mirdej/vmix/images/IMG_1347.jpg

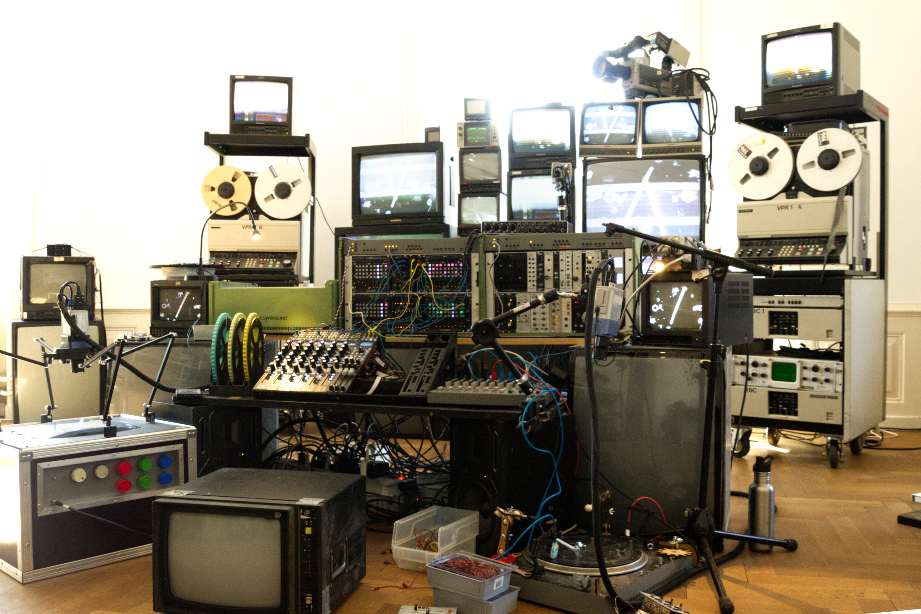
images/IMG_1347.jpg
