mirdej/vmix/electronics/vm106-mixbus/vm106-mixbus.kicad_pcb

## KiCad design electronics/vm106-mixbus/vm106-mixbus.kicad_pcb (2021-04-03)

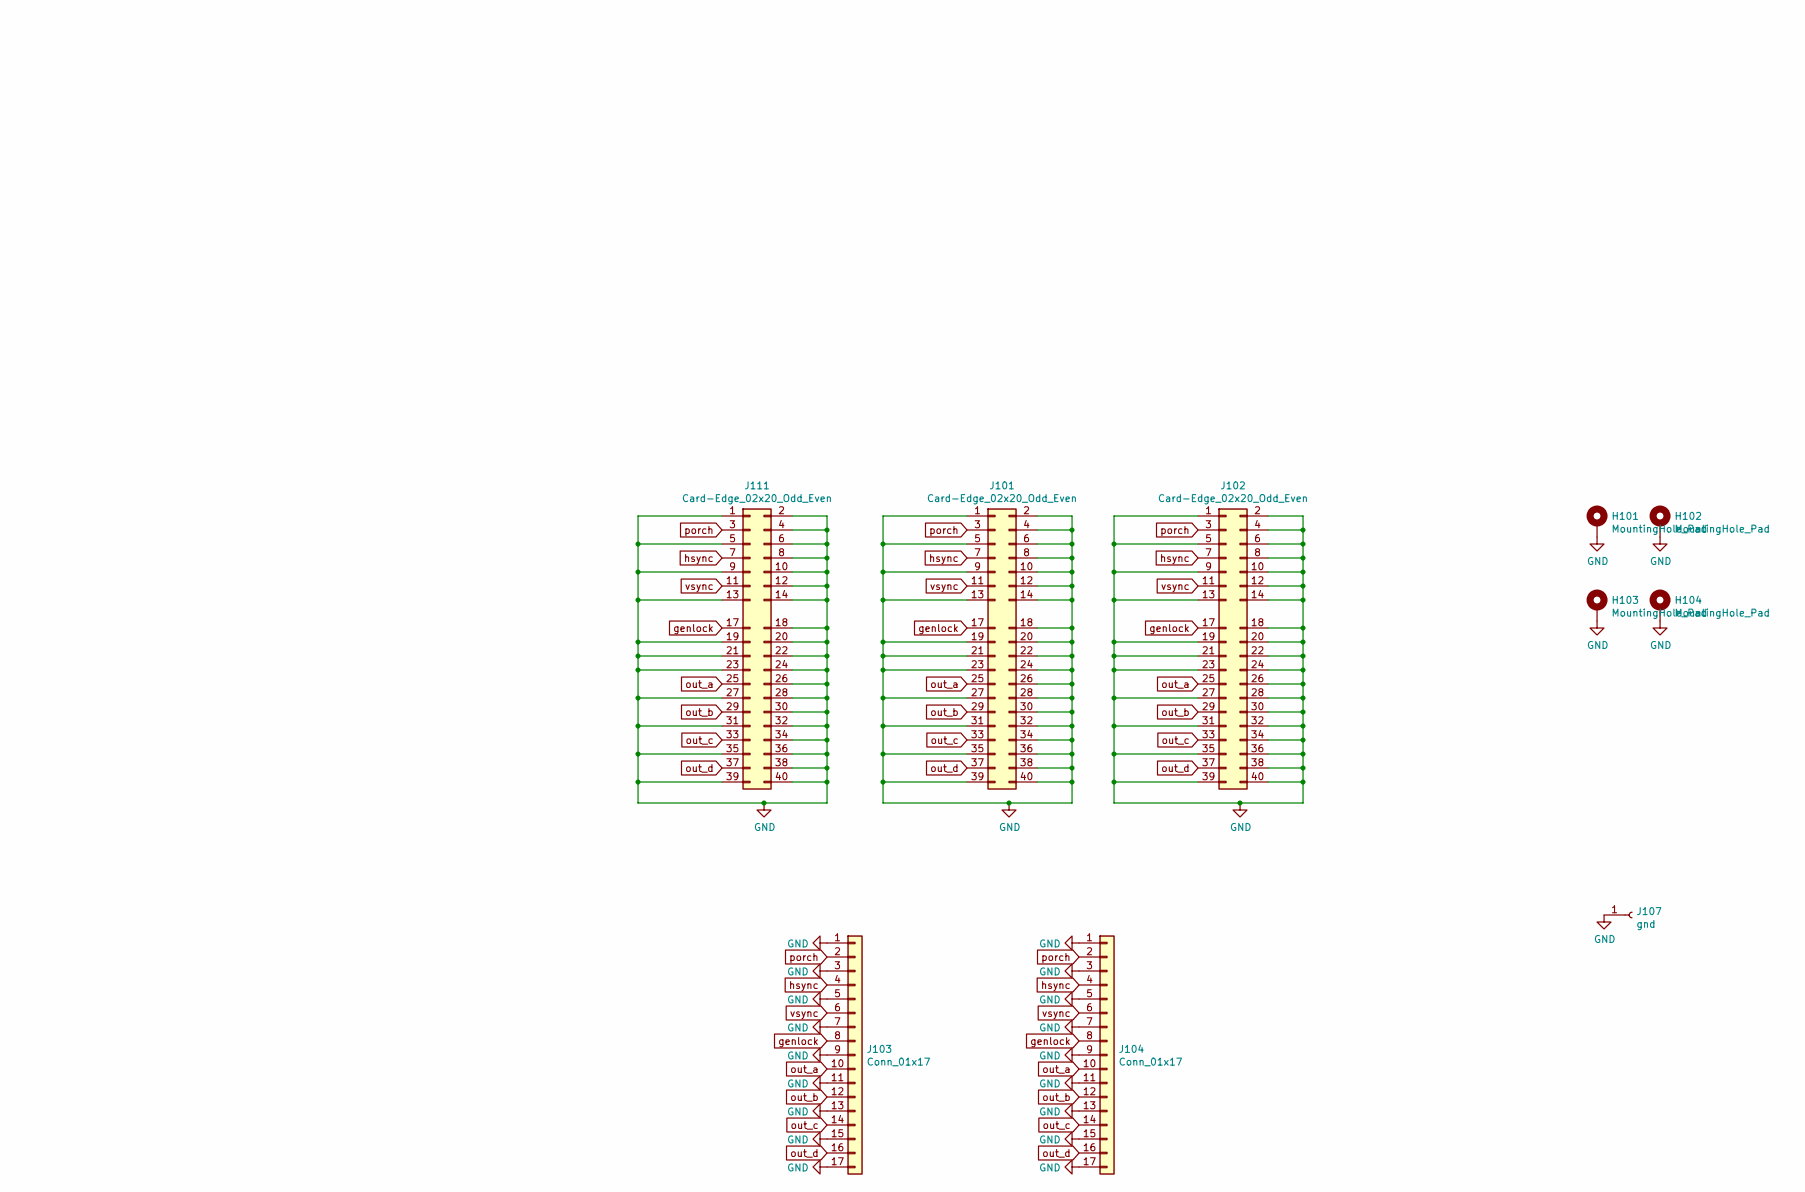
[picture p47: schematic vm106-mixbus.sch, part in row 2, column 2]

Parts:
H101, H102, H103, H104: MountingHole_Pad; MountingHole_3.2mm_M3_ISO7380_Pad
J101, J102, J111: Card-Edge_02x20_Odd_Even; Samtec_MECF-20-01-L-DV-WT_2x20_P1.27mm_Polarized_Socket_Hor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
J103, J104: Conn_01x17; 17pin-smd
J107: gnd; Solderpad_1mm

Connections:
GND: H101.1, H102.1, H103.1, H104.1, J101.1, J101.2, J101.4, J101.5, J101.6, J101.8, J101.9, J101.10, J101.12, J101.13, J101.14, J101.18, J101.19, J101.20, J101.21, J101.22, J101.23, J101.24, J101.26, J101.27, J101.28, J101.30, J101.31, J101.32, J101.34, J101.35, J101.36, J101.38, J101.39, J101.40, J102.1, J102.2, J102.4, J102.5, J102.6, J102.8, J102.9, J102.10, J102.12, J102.13, J102.14, J102.18, J102.19, J102.20, J102.21, J102.22, J102.23, J102.24, J102.26, J102.27, J102.28, J102.30, J102.31, J102.32, J102.34, J102.35, J102.36, J102.38, J102.39, J102.40, J103.1, J103.3, J103.5, J103.7, J103.9, J103.11, J103.13, J103.15, J103.17, J104.1, J104.3, J104.5, J104.7, J104.9, J104.11, J104.13, J104.15, J104.17, J107.1, J111.1, J111.2, J111.4, J111.5, J111.6, J111.8, J111.9, J111.10, J111.12, J111.13, J111.14, J111.18, J111.19, J111.20, J111.21, J111.22, J111.23, J111.24, J111.26, J111.27, J111.28, J111.30, J111.31, J111.32, J111.34, J111.35, J111.36, J111.38, J111.39, J111.40
genlock: J101.17, J102.17, J103.8, J104.8, J111.17
hsync: J101.7, J102.7, J103.4, J104.4, J111.7
out_a: J101.25, J102.25, J103.10, J104.10, J111.25
out_b: J101.29, J102.29, J103.12, J104.12, J111.29
out_c: J101.33, J102.33, J103.14, J104.14, J111.33
out_d: J101.37, J102.37, J103.16, J104.16, J111.37
porch: J101.3, J102.3, J103.2, J104.2, J111.3
vsync: J101.11, J102.11, J103.6, J104.6, J111.11

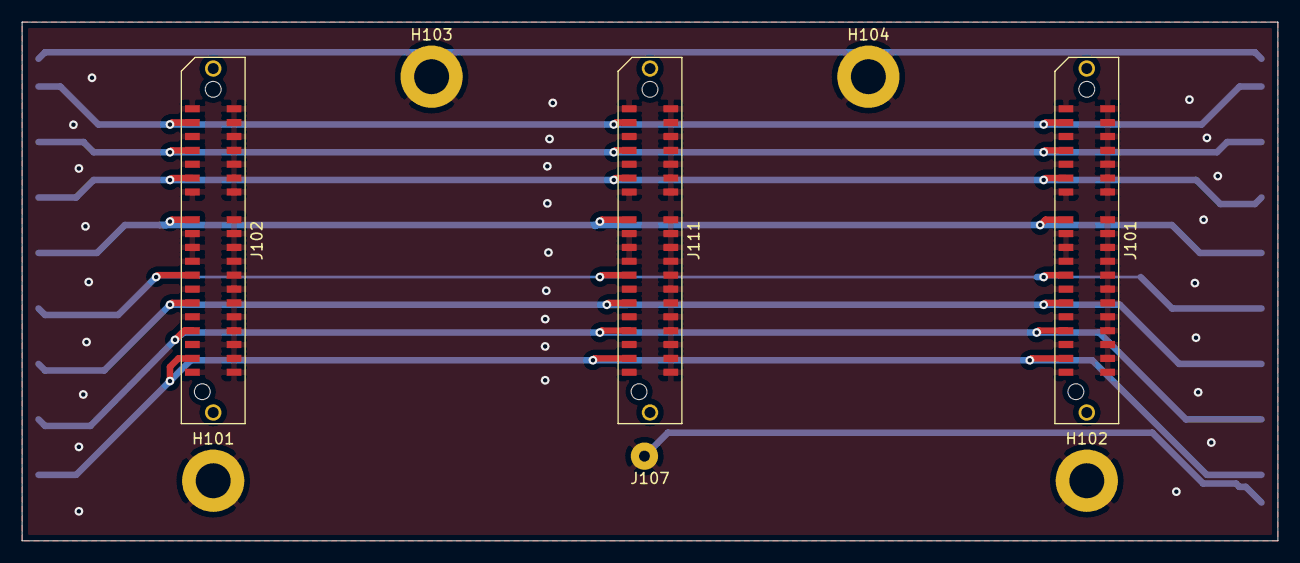
[picture p48: board vm106-mixbus.kicad_pcb from above]

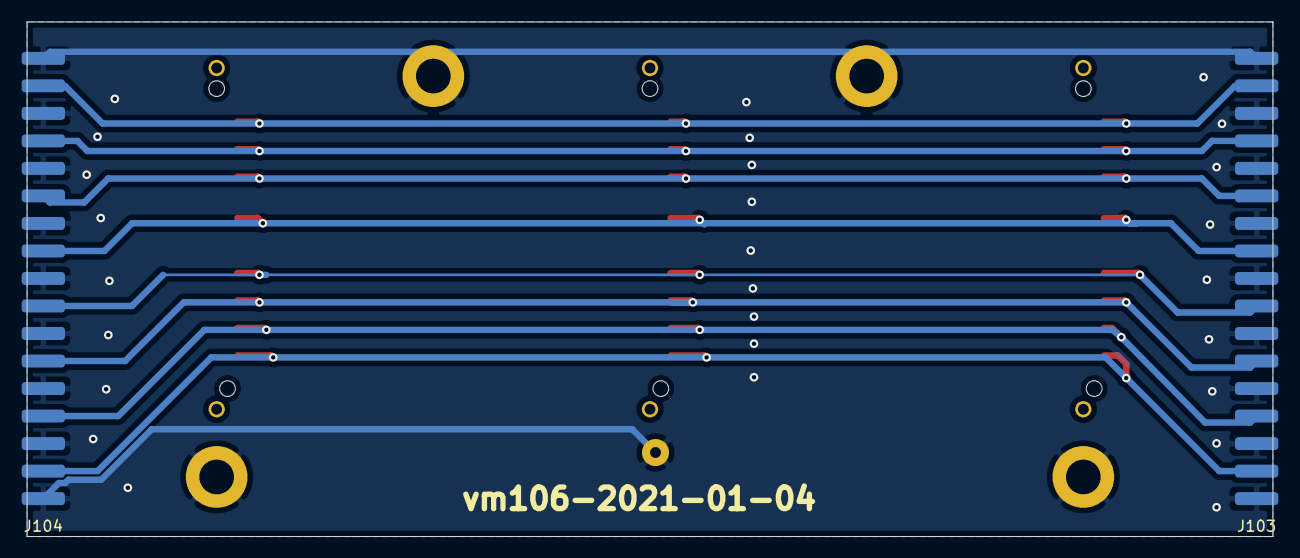
[picture p49: board vm106-mixbus.kicad_pcb from below]

Board: 2 copper layers, 115.0 x 47.5 mm, 10 parts (2 on the bottom side), 9 nets.
