mirdej/vmix/electronics/vm113-effects/vm113-effects.kicad_pcb

## KiCad design electronics/vm113-effects/vm113-effects.kicad_pcb (2021-01-17)

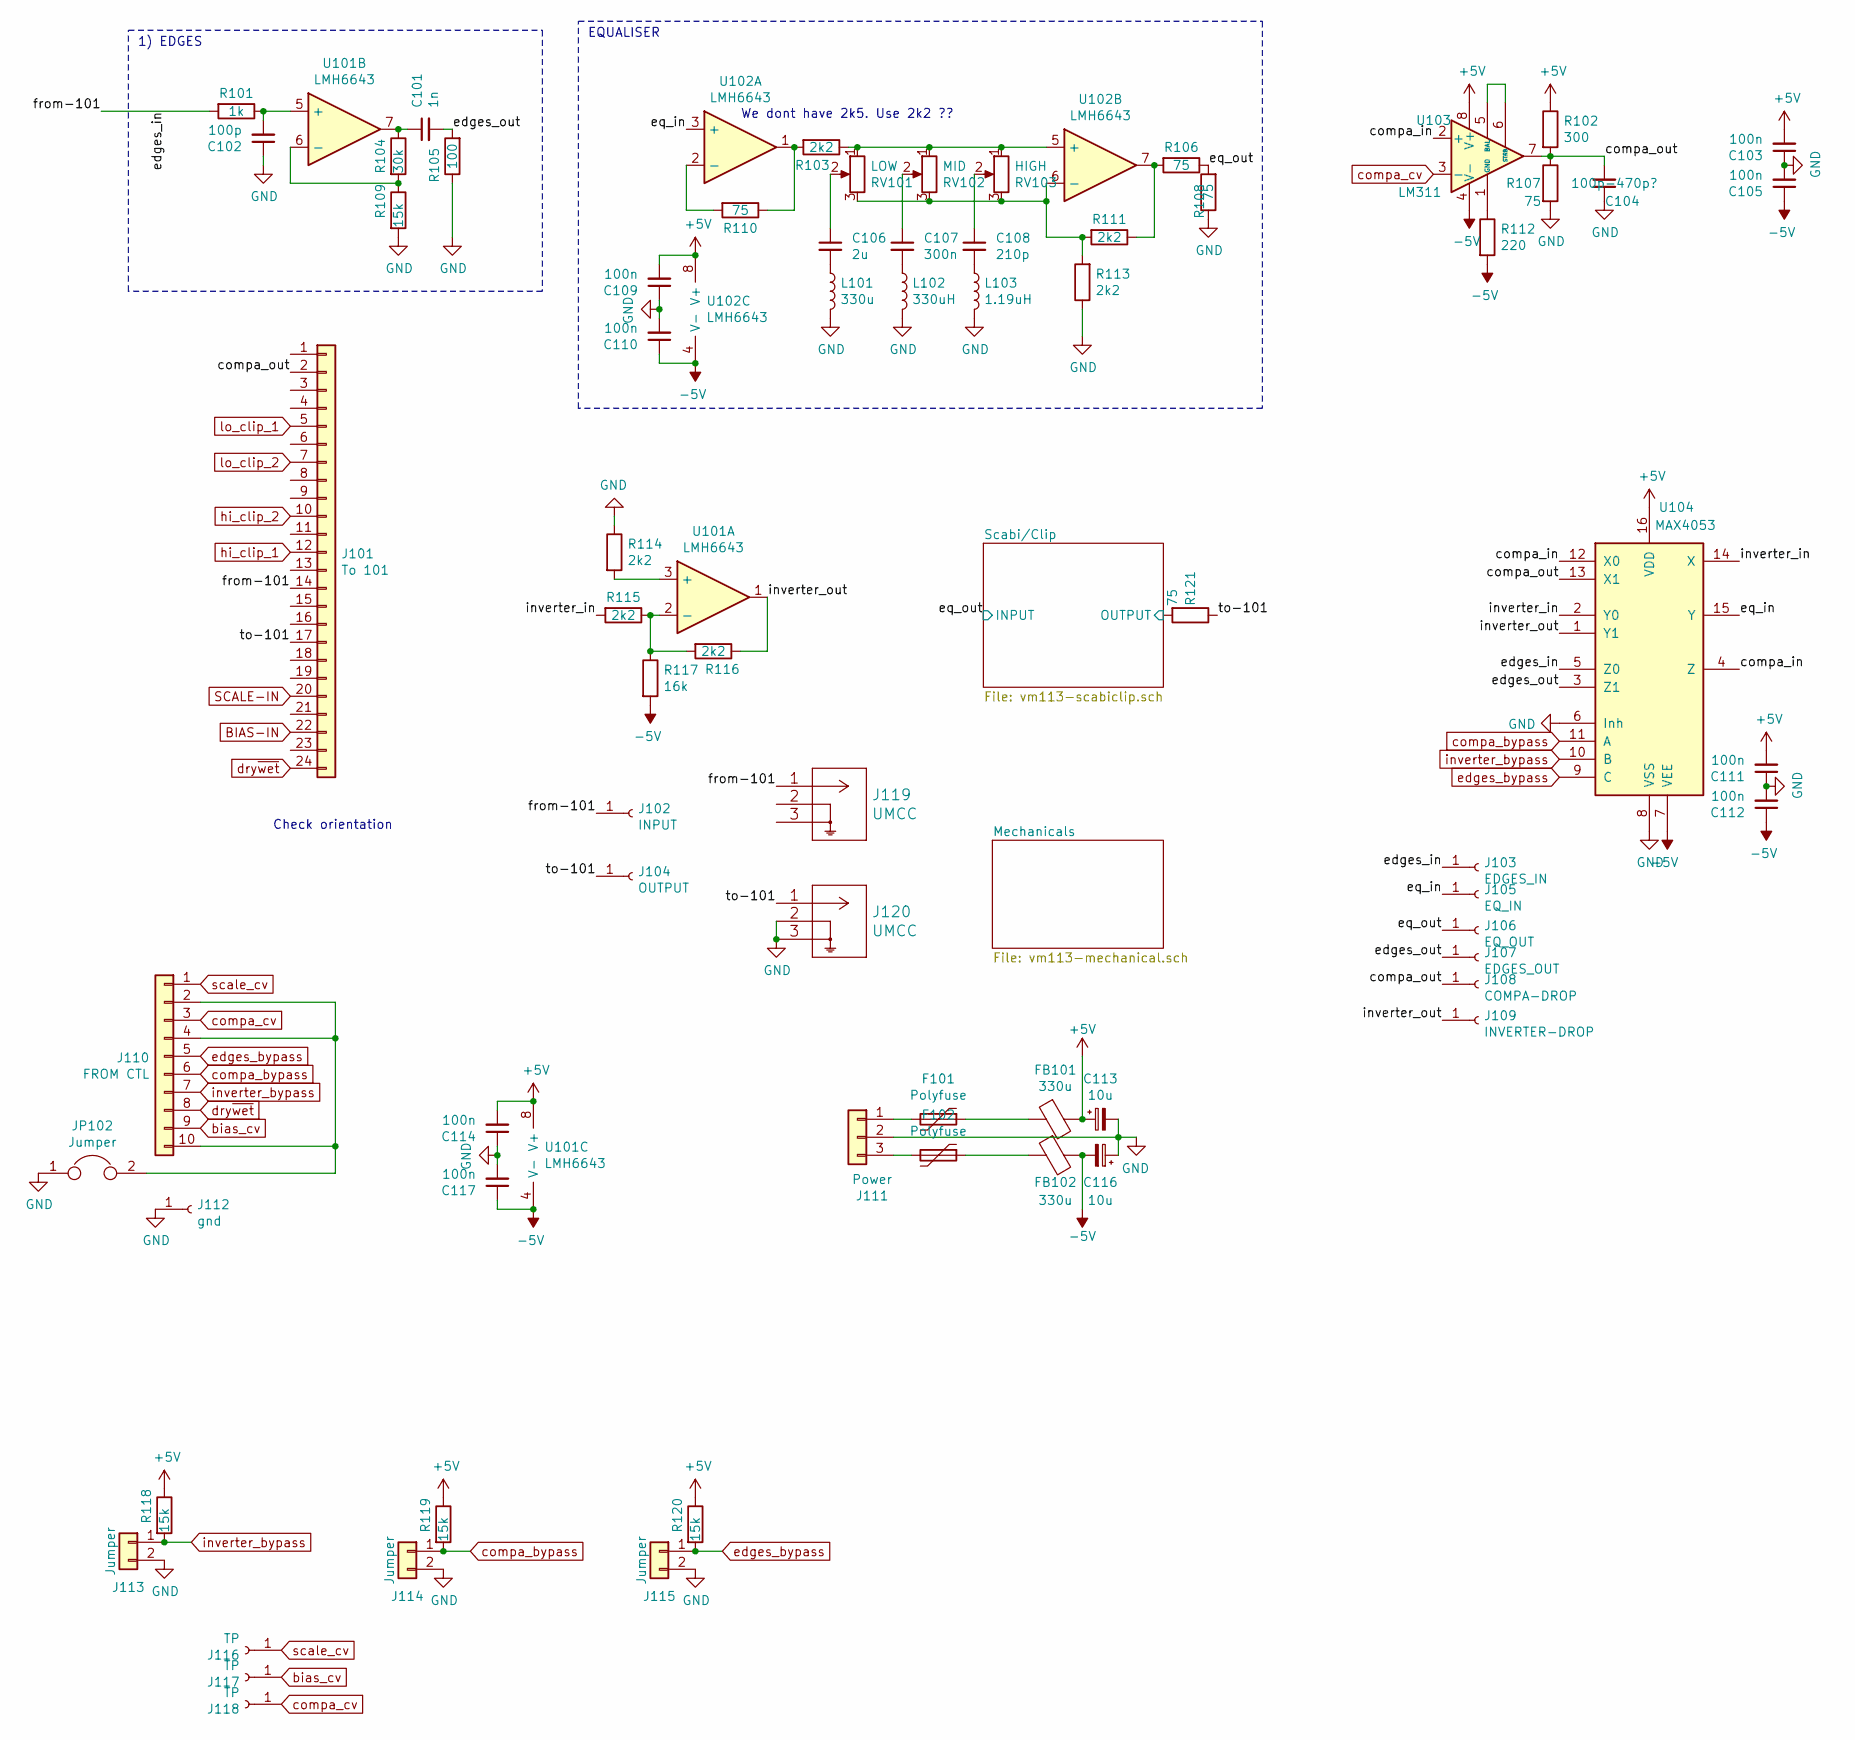
[picture p50: schematic vm113-effects.sch, vMIX20-Effects]

Parts:
C101: 1n; C_0805_2012Metric_Pad1.15x1.40mm_HandSolder
C102: 100p; C_0805_2012Metric_Pad1.15x1.40mm_HandSolder
C103, C105, C109, C110, C111, C112, C114, C117: 100n; C_0603_1608Metric_Pad1.05x0.95mm_HandSolder
C104: 100p-470p?; C_0603_1608Metric_Pad1.05x0.95mm_HandSolder
C106: 2u; C_1206_3216Metric_Pad1.42x1.75mm_HandSolder
C107: 300n; C_1206_3216Metric_Pad1.42x1.75mm_HandSolder
C108: 210p; C_0805_2012Metric_Pad1.15x1.40mm_HandSolder
C113, C116: 10u; CP_EIA-3528-21_Kemet-B_Pad1.50x2.35mm_HandSolder
F101, F102: Polyfuse; Fuse_0805_2012Metric
FB101, FB102: 330u; L_0805_2012Metric_Pad1.15x1.40mm_HandSolder
J101: To 101; Hirose_FH12-24S-0.5SH_1x24-1MP_P0.50mm_Horizontal
J102: INPUT; Solderpad_1mm
J103: EDGES_IN; Solderpad_1mm
J104: OUTPUT; Solderpad_1mm
J105: EQ_IN; Solderpad_1mm
J106: EQ_OUT; Solderpad_1mm
J107: EDGES_OUT; Solderpad_1mm
J108: COMPA-DROP; Solderpad_1mm
J109: INVERTER-DROP; Solderpad_1mm
J110: FROM CTL; IDC-Header_2x05_P2.54mm_Vertical
J111: Power; Molex_KK-254_AE-6410-03A_1x03_P2.54mm_Vertical
J112: gnd; Solderpad_1mm
J113, J114, J115: Jumper; PinHeader_1x02_P2.54mm_Vertical
J116, J117, J118: TP; Solderpad_1mm
J119, J120: UMCC; TE_UMCC_2337019-1
JP102: Jumper; SolderJumper-2_P1.3mm_Open_TrianglePad1.0x1.5mm
L101: 330u; L_1210_3225Metric_Pad1.42x2.65mm_HandSolder
L102: 330uH; L_1210_3225Metric_Pad1.42x2.65mm_HandSolder
L103: 1.19uH; L_1210_3225Metric_Pad1.42x2.65mm_HandSolder
R101: 1k; R_0805_2012Metric_Pad1.15x1.40mm_HandSolder
R102: 300; R_0805_2012Metric_Pad1.15x1.40mm_HandSolder
R103, R111, R113, R114, R115, R116: 2k2; R_0805_2012Metric_Pad1.15x1.40mm_HandSolder
R104: 30k; R_0805_2012Metric_Pad1.15x1.40mm_HandSolder
R105: 100; R_0805_2012Metric_Pad1.15x1.40mm_HandSolder
R106, R107, R108, R110, R121: 75; R_0805_2012Metric_Pad1.15x1.40mm_HandSolder
R109, R118, R119, R120: 15k; R_0805_2012Metric_Pad1.15x1.40mm_HandSolder
R112: 220; R_0805_2012Metric_Pad1.15x1.40mm_HandSolder
R117: 16k; R_0805_2012Metric_Pad1.15x1.40mm_HandSolder
RV101: LOW; Potentiometer_Alps_RK09K_Single_Horizontal
RV102: MID; Potentiometer_Alps_RK09K_Single_Horizontal
RV103: HIGH; Potentiometer_Alps_RK09K_Single_Horizontal
U101, U102: LMH6643; SOIC-8_3.9x4.9mm_P1.27mm
U103: LM311; SOIC-8_3.9x4.9mm_P1.27mm
U104: MAX4053; SOP-16_4.55x10.3mm_P1.27mm

Connections:
+5V: C103.2, C109.2, C111.2, C113.1, C114.2, FB101.2, R102.1, R118.1, R119.1, R120.1, U101.8 (V+), U102.8 (V+), U103.8 (V+), U104.16 (VDD); also elsewhere on the board
-5V: C105.1, C110.1, C112.1, C116.2, C117.1, FB102.2, R112.2, R117.2, U101.4 (V-), U102.4 (V-), U103.4 (V-), U104.7 (VEE); also elsewhere on the board
/Scabi/Clip/OUTPUT: R121.2; also elsewhere on the board
/compa_in: U103.2 (+), U104.4 (Z), U104.12 (X0)
/compa_out: C104.2, J101.2, J108.1, R102.2, R107.1, U103.7, U104.13 (X1)
/edges_in: J101.14, J102.1, J103.1, J119.1, R101.2, U104.5 (Z0)
/edges_out: C101.2, J107.1, R105.2, U104.3 (Z1)
/eq_in: J105.1, U102.3 (+), U104.15 (Y)
/eq_out: J106.1, R106.1, R108.2; also elsewhere on the board
/inverter_in: R115.2, U104.2 (Y0), U104.14 (X)
/inverter_out: J109.1, R116.1, U101.1, U104.1 (Y1)
/to-101: J101.17, J104.1, J120.1, R121.1
BIAS-IN: J101.22; also elsewhere on the board
GND: C102.1, C103.1, C104.1, C105.2, C109.1, C110.2, C111.1, C112.2, C113.2, C114.1, C116.1, C117.2, J111.2, J112.1, J113.2, J114.2, J115.2, J120.2, J120.3, JP102.1, L101.2, L102.2, L103.2, R105.1, R107.2, R108.1, R109.2, R113.1, R114.1, U104.6 (Inh), U104.8 (VSS); also elsewhere on the board
unnamed: C101.1, R104.1, U101.7
unnamed: C102.2, R101.1, U101.5 (+)
unnamed: C106.1, RV101.2
unnamed: C106.2, L101.1
unnamed: C107.1, RV102.2
unnamed: C107.2, L102.1
unnamed: C108.1, RV103.2
unnamed: C108.2, L103.1
unnamed: F101.1, FB101.1
unnamed: F101.2, J111.1
unnamed: F102.1, FB102.1
unnamed: F102.2, J111.3
unnamed: J110.2, J110.4, J110.10, JP102.2
unnamed: R103.1, RV101.1, RV102.1, RV103.1, U102.5 (+)
unnamed: R103.2, R110.1, U102.1
unnamed: R104.2, R109.1, U101.6 (-)
unnamed: R106.2, R111.1, U102.7
unnamed: R110.2, U102.2 (-)
unnamed: R111.2, R113.2, RV101.3, RV102.3, RV103.3, U102.6 (-)
unnamed: R112.1, U103.1 (GND)
unnamed: R114.2, U101.3 (+)
unnamed: R115.1, R116.2, R117.1, U101.2 (-)
unnamed: U103.5 (BAL), U103.6 (STRB)
SCALE-IN: J101.20; also elsewhere on the board
bias_cv: J110.9, J117.1; also elsewhere on the board
compa_bypass: J110.6, J114.1, R119.2, U104.11 (A)
compa_cv: J110.3, J118.1, U103.3 (-)
dry~wet~: J101.24, J110.8
edges_bypass: J110.5, J115.1, R120.2, U104.9 (C)
hi_clip_1: J101.12; also elsewhere on the board
hi_clip_2: J101.10; also elsewhere on the board
inverter_bypass: J110.7, J113.1, R118.2, U104.10 (B)
lo_clip_1: J101.5; also elsewhere on the board
lo_clip_2: J101.7; also elsewhere on the board
scale_cv: J110.1, J116.1; also elsewhere on the board

Notes on the sheet:
EQUALISER
1) EDGES
Check orientation
We dont have 2k5. Use 2k2 ??

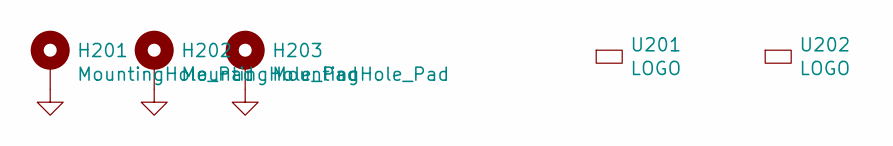
[picture p51: schematic vm113-mechanical.sch]

Parts:
H201, H202, H203: MountingHole_Pad; MountingHole_3.2mm_M3_ISO7380_Pad
U201: LOGO; logo_anyma
U202: LOGO; OSHW-Logo2_7.3x6mm_SilkScreen

Connections:
GND: H201.1, H202.1, H203.1; also elsewhere on the board

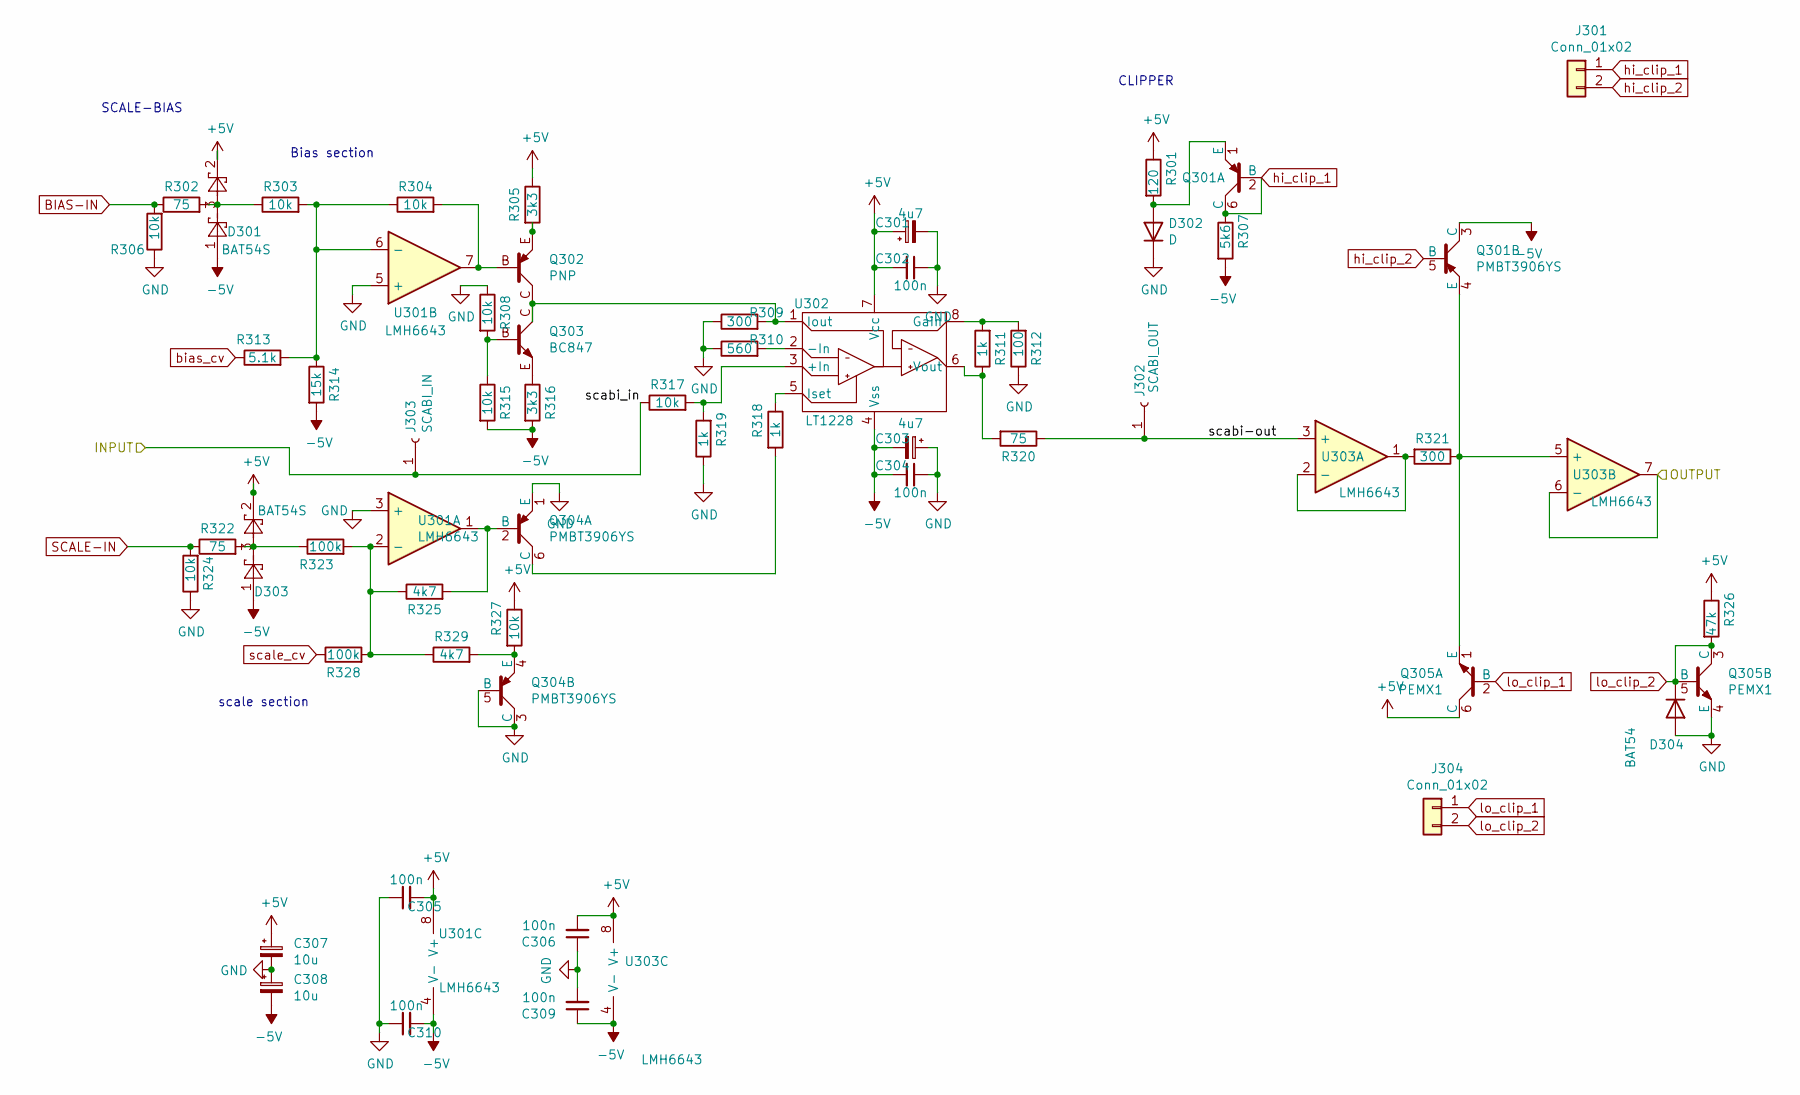
[picture p52: schematic vm113-scabiclip.sch, vMIX20-Scale,Bias, Clip]

Parts:
C301, C303: 4u7; CP_EIA-3528-21_Kemet-B_Pad1.50x2.35mm_HandSolder
C302, C304, C305, C306, C309, C310: 100n; C_0603_1608Metric_Pad1.05x0.95mm_HandSolder
C307, C308: 10u; CP_EIA-3528-21_Kemet-B_Pad1.50x2.35mm_HandSolder
D301, D303: BAT54S; SOT-23
D302: D; D_MiniMELF
D304: BAT54; D_SOT-23_ANK
J301, J304: Conn_01x02; PinHeader_1x02_P2.54mm_Vertical
J302: SCABI_OUT; Solderpad_1mm
J303: SCABI_IN; Solderpad_1mm
Q301, Q304: PMBT3906YS; SOT-363_SC-70-6_Handsoldering
Q302: PNP; SOT-23_BEC
Q303: BC847; SOT-23_BEC
Q305: PEMX1; SOT-666
R301: 120; R_0805_2012Metric_Pad1.15x1.40mm_HandSolder
R302, R320, R322: 75; R_0805_2012Metric_Pad1.15x1.40mm_HandSolder
R303, R304, R306, R308, R315, R317, R324, R327: 10k; R_0805_2012Metric_Pad1.15x1.40mm_HandSolder
R305, R316: 3k3; R_0805_2012Metric_Pad1.15x1.40mm_HandSolder
R307: 5k6; R_0805_2012Metric_Pad1.15x1.40mm_HandSolder
R309, R321: 300; R_0805_2012Metric_Pad1.15x1.40mm_HandSolder
R310: 560; R_0805_2012Metric_Pad1.15x1.40mm_HandSolder
R311, R318, R319: 1k; R_0805_2012Metric_Pad1.15x1.40mm_HandSolder
R312: 100; R_0805_2012Metric_Pad1.15x1.40mm_HandSolder
R313: 5.1k; R_0805_2012Metric_Pad1.15x1.40mm_HandSolder
R314: 15k; R_0805_2012Metric_Pad1.15x1.40mm_HandSolder
R323, R328: 100k; R_0805_2012Metric_Pad1.15x1.40mm_HandSolder
R325, R329: 4k7; R_0805_2012Metric_Pad1.15x1.40mm_HandSolder
R326: 47k; R_0805_2012Metric_Pad1.15x1.40mm_HandSolder
U301, U303: LMH6643; SOIC-8_3.9x4.9mm_P1.27mm
U302: LT1228; SOIC-8_3.9x4.9mm_P1.27mm

Connections:
+5V: C301.1, C302.2, C305.2, C306.2, C307.1, D301.2, D303.2, Q305.6 (C), R301.1, R305.1, R326.1, R327.1, U301.8 (V+), U302.7 (Vcc), U303.8 (V+); also elsewhere on the board
-5V: C303.2, C304.2, C308.2, C309.1, C310.2, D301.1, D303.1, Q301.3 (C), R307.2, R314.2, R315.2, R316.2, U301.4 (V-), U302.4 (Vss), U303.4 (V-); also elsewhere on the board
/Scabi/Clip/OUTPUT: U303.6 (-), U303.7; also elsewhere on the board
/Scabi/Clip/scabi-out: J302.1, R320.1, U303.3 (+)
/eq_out: J303.1, R317.1; also elsewhere on the board
BIAS-IN: R302.1, R306.2; also elsewhere on the board
GND: C301.2, C302.1, C303.1, C304.1, C305.1, C306.1, C307.2, C308.1, C309.2, C310.1, D302.1 (K), D304.2 (A), Q304.1 (E), Q304.3 (C), Q304.5 (B), Q305.4 (E), R306.1, R308.1, R309.1, R310.1, R312.1, R319.1, R324.1, U301.3 (+), U301.5 (+); also elsewhere on the board
unnamed: D301.3, R302.2, R303.1
unnamed: D302.2 (A), Q301.1 (E), R301.2
unnamed: D303.3, R322.2, R323.1
unnamed: Q301.4 (E), Q305.1 (E), R321.1, U303.5 (+)
unnamed: Q302.B, R304.2, U301.7
unnamed: Q302.C, Q303.C, R309.2, U302.1 (Iout)
unnamed: Q302.E, R305.2
unnamed: Q303.B, R308.2, R315.1
unnamed: Q303.E, R316.1
unnamed: Q304.2 (B), R325.2, U301.1
unnamed: Q304.4 (E), R327.2, R329.2
unnamed: Q304.6 (C), R318.2
unnamed: R303.2, R304.1, R313.2, R314.1, U301.6 (-)
unnamed: R310.2, U302.2 (-In)
unnamed: R311.1, R320.2, U302.6 (Vout)
unnamed: R311.2, R312.2, U302.8 (Gain)
unnamed: R317.2, R319.2, U302.3 (+In)
unnamed: R318.1, U302.5 (Iset)
unnamed: R321.2, U303.1, U303.2 (-)
unnamed: R323.2, R325.1, R328.2, R329.1, U301.2 (-)
SCALE-IN: R322.1, R324.2; also elsewhere on the board
bias_cv: R313.1; also elsewhere on the board
hi_clip_1: J301.1, Q301.2 (B), Q301.6 (C), R307.1; also elsewhere on the board
hi_clip_2: J301.2, Q301.5 (B); also elsewhere on the board
lo_clip_1: J304.1, Q305.2 (B); also elsewhere on the board
lo_clip_2: D304.1 (K), J304.2, Q305.3 (C), Q305.5 (B), R326.2; also elsewhere on the board
scale_cv: R328.1; also elsewhere on the board

Notes on the sheet:
Bias section
scale section
SCALE-BIAS
CLIPPER

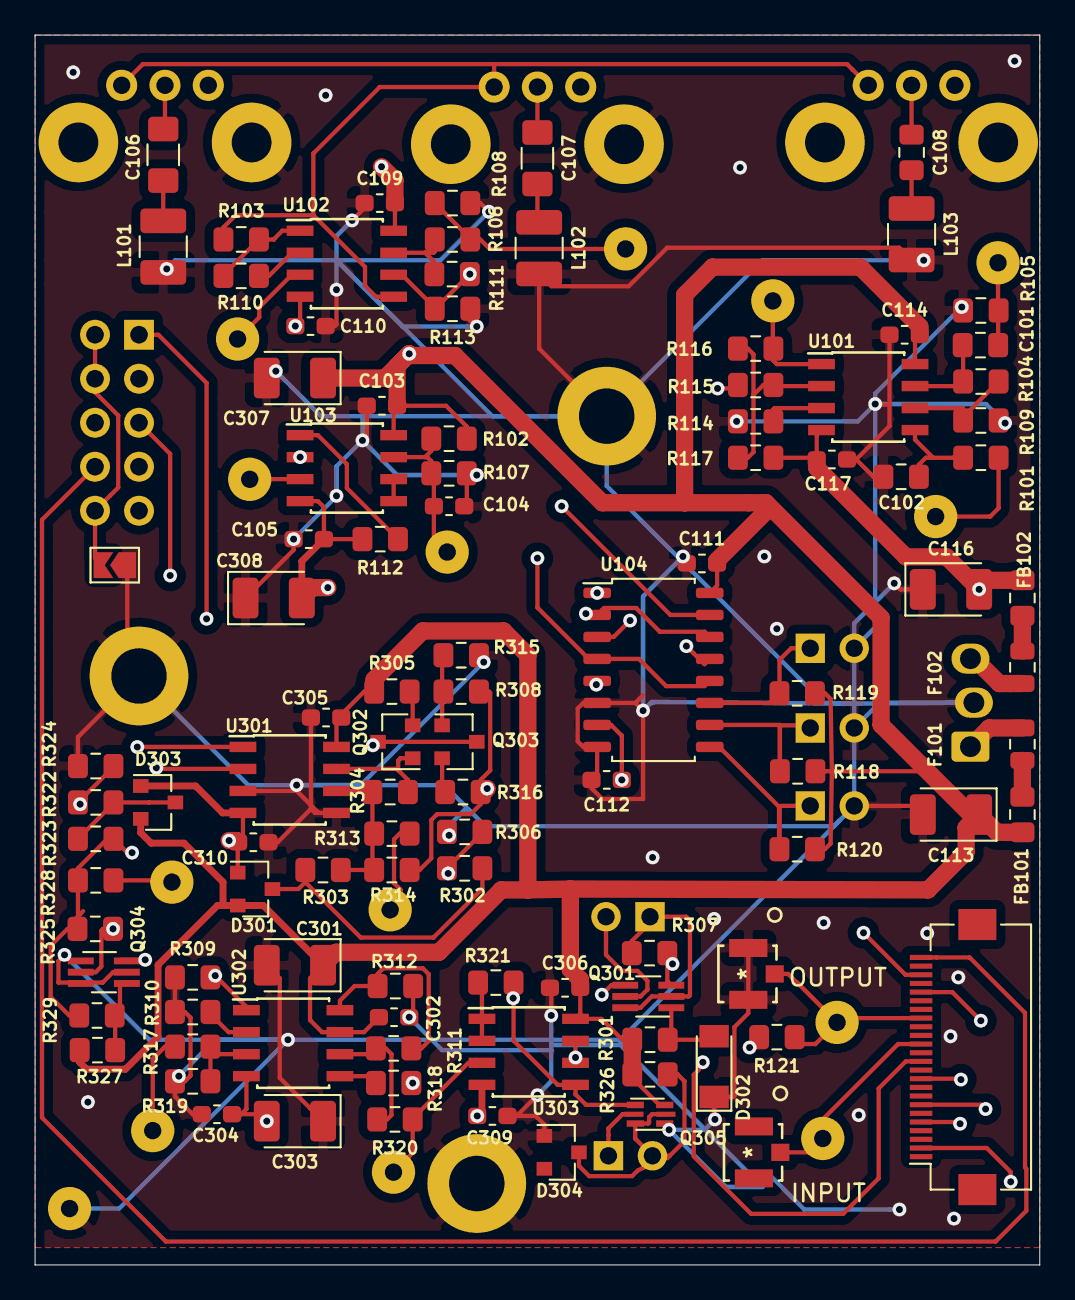
[picture p53: board vm113-effects.kicad_pcb from above]

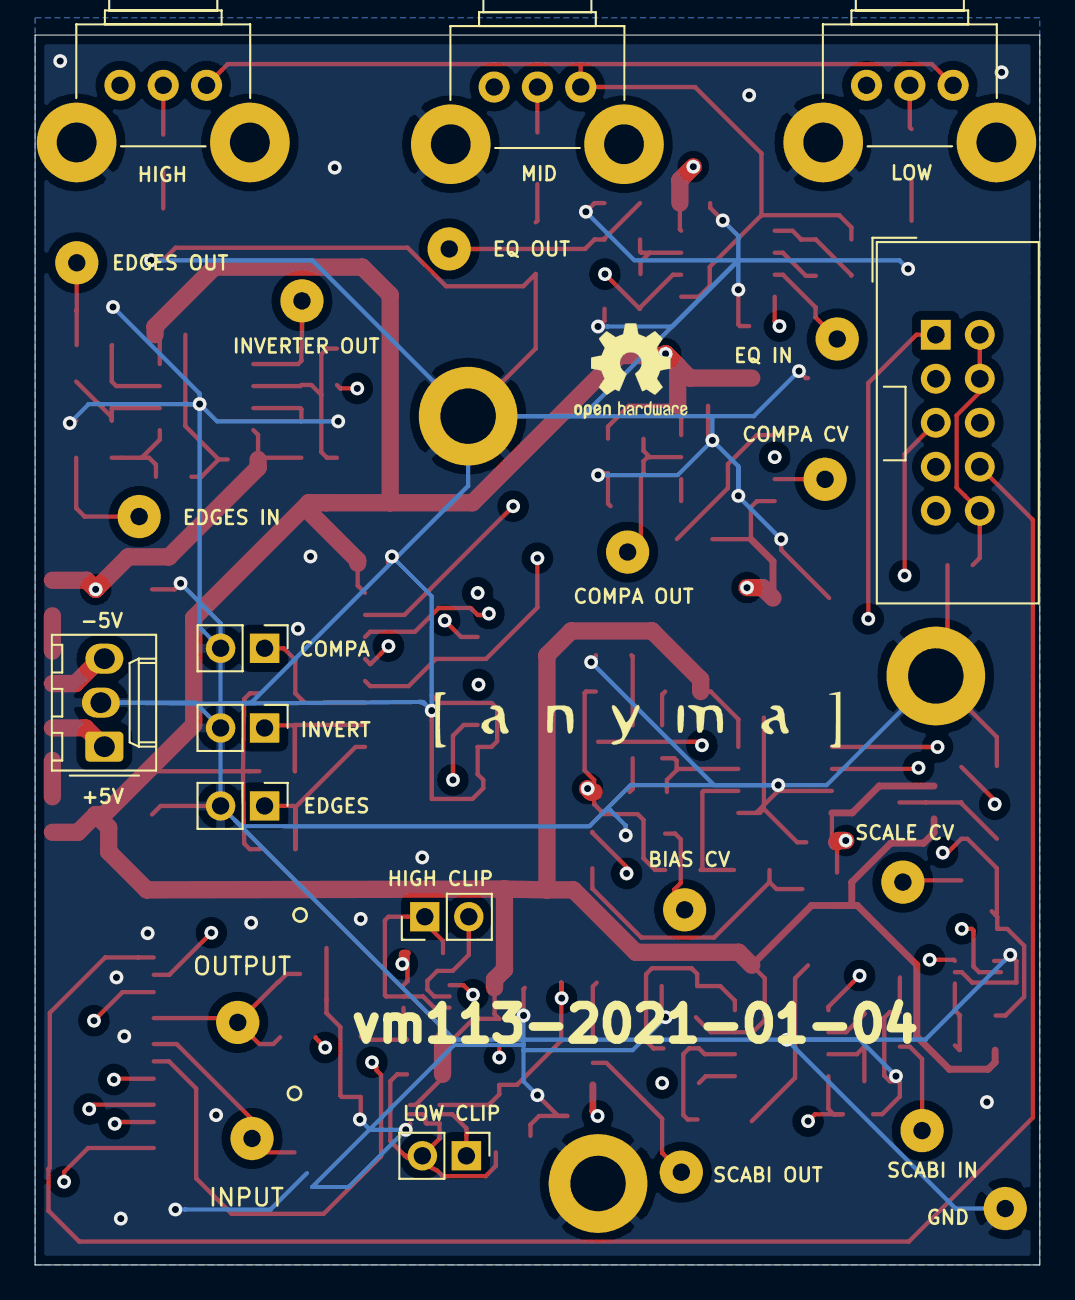
[picture p54: board vm113-effects.kicad_pcb from below]

Board: 4 copper layers, 58.0 x 71.0 mm, 132 parts (12 on the bottom side), 70 nets.
