mirdej/vmix/electronics/vm123-genlock-in/vm123-genlock-in.kicad_pcb

## KiCad design electronics/vm123-genlock-in/vm123-genlock-in.kicad_pcb (2021-03-14)

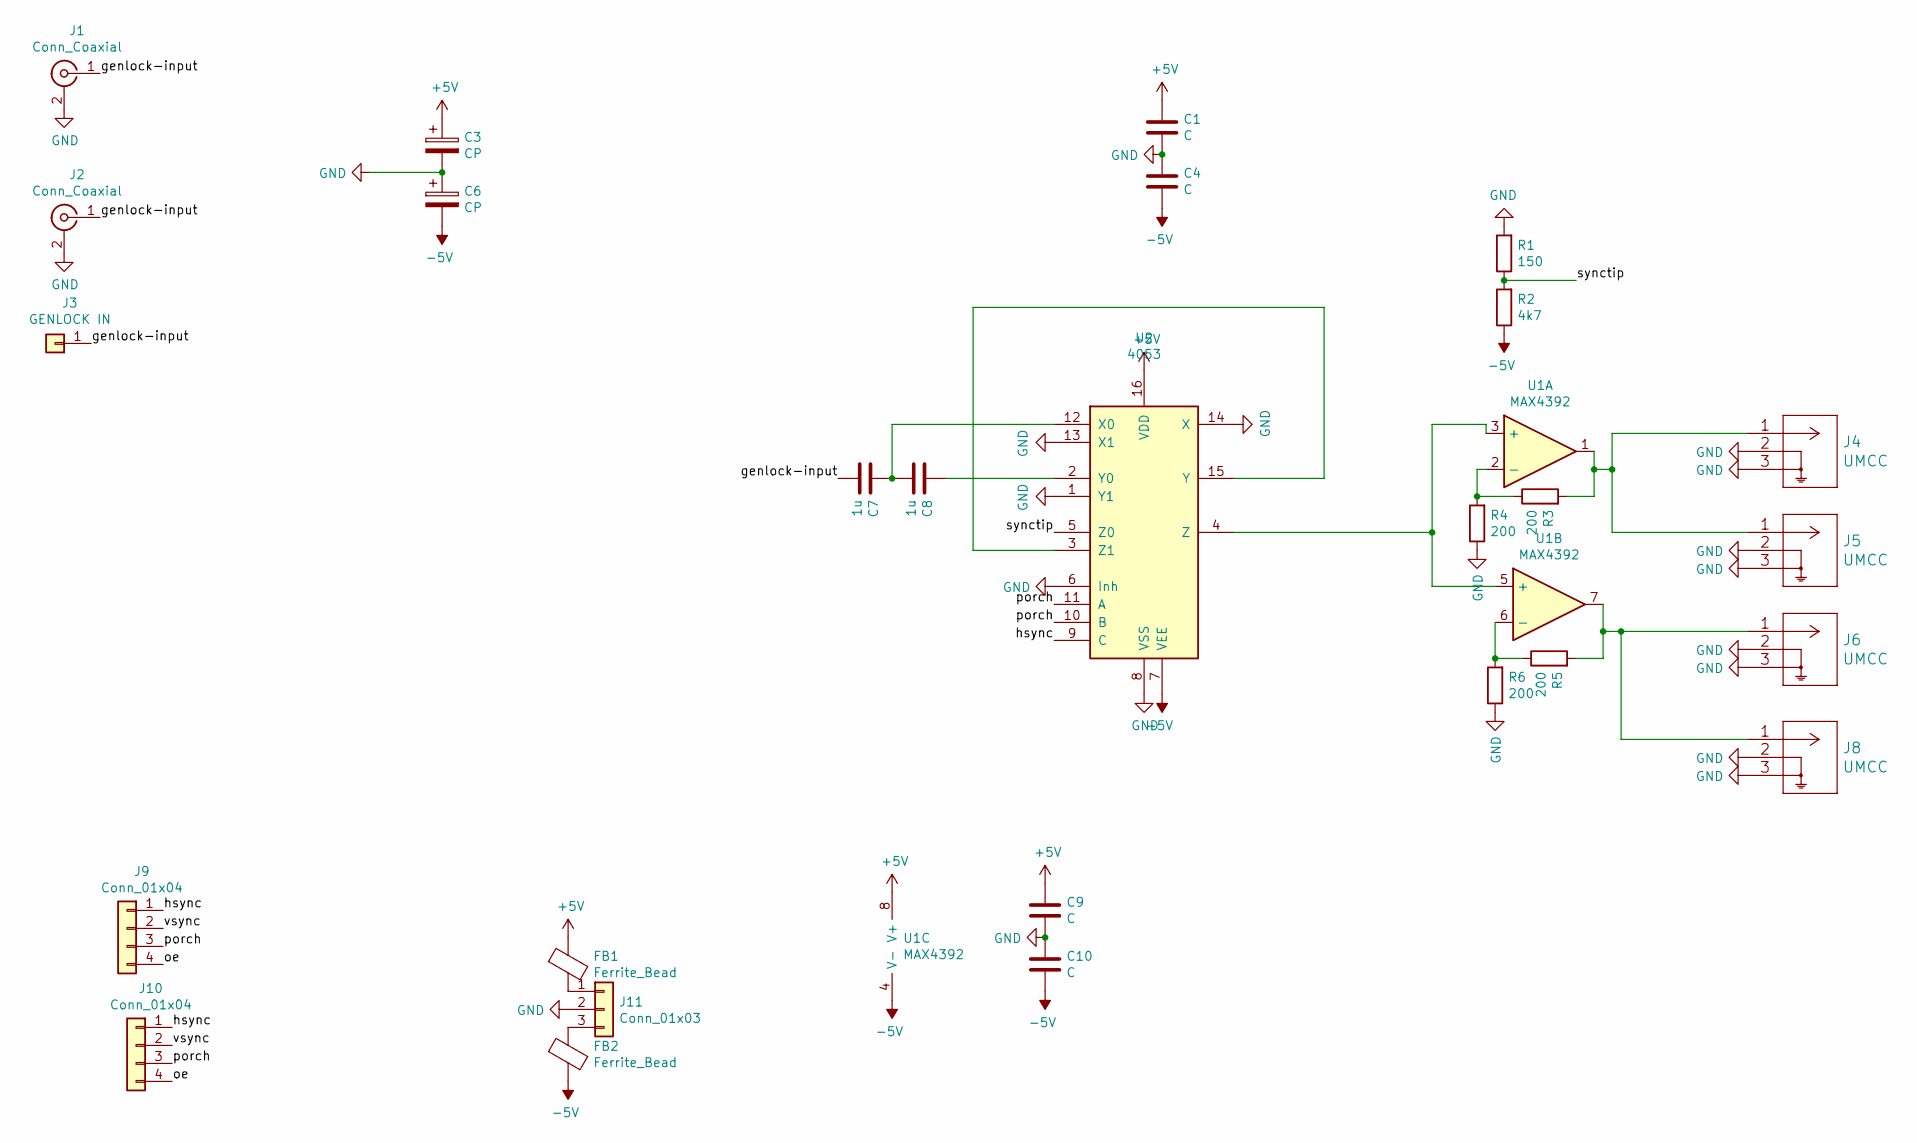
[picture p55: schematic vm123-genlock-in.sch]

Parts:
C1, C4, C9, C10: C; C_0603_1608Metric_Pad1.05x0.95mm_HandSolder
C3, C6: CP; CP_EIA-3528-21_Kemet-B_Pad1.50x2.35mm_HandSolder
C7, C8: 1u; C_1206_3216Metric_Pad1.42x1.75mm_HandSolder
FB1, FB2: Ferrite_Bead; L_1206_3216Metric_Pad1.42x1.75mm_HandSolder
J1, J2: Conn_Coaxial; BNC_MOLEX_0731000080_Horizontal
J3: GENLOCK IN; Solderpad_1mm
J4, J5, J6, J8: UMCC; TE_UMCC_2337019-1
J9, J10: Conn_01x04; Molex_KK-254_AE-6410-04A_1x04_P2.54mm_Vertical
J11: Conn_01x03; PinHeader_1x03_P2.54mm_Vertical
R1: 150; R_1206_3216Metric_Pad1.42x1.75mm_HandSolder
R2: 4k7; R_1206_3216Metric_Pad1.42x1.75mm_HandSolder
R3, R4, R5, R6: 200; R_1206_3216Metric_Pad1.42x1.75mm_HandSolder
U1: MAX4392; SOIC-8_3.9x4.9mm_P1.27mm
U2: 4053; SOIC-16_3.9x9.9mm_P1.27mm

Connections:
+5V: C1.1, C3.1, C9.1, FB1.1, U1.8 (V+), U2.16 (VDD)
-5V: C4.2, C6.2, C10.2, FB2.2, R2.1, U1.4 (V-), U2.7 (VEE)
/genlock-input: C7.2, J1.1 (In), J2.1 (In), J3.1
/hsync: J9.1, J10.1, U2.9 (C)
/oe: J9.4, J10.4
/porch: J9.3, J10.3, U2.10 (B), U2.11 (A)
/synctip: R1.1, R2.2, U2.5 (Z0)
/vsync: J9.2, J10.2
GND: C1.2, C3.2, C4.1, C6.1, C9.2, C10.1, J1.2 (Ext), J2.2 (Ext), J4.2, J4.3, J5.2, J5.3, J6.2, J6.3, J8.2, J8.3, J11.2, R1.2, R4.1, R6.1, U2.1 (Y1), U2.6 (Inh), U2.8 (VSS), U2.13 (X1), U2.14 (X)
unnamed: C7.1, C8.2, U2.12 (X0)
unnamed: C8.1, U2.2 (Y0)
unnamed: FB1.2, J11.1
unnamed: FB2.1, J11.3
unnamed: J4.1, J5.1, R3.2, U1.1
unnamed: J6.1, J8.1, R5.2, U1.7
unnamed: R3.1, R4.2, U1.2 (-)
unnamed: R5.1, R6.2, U1.6 (-)
unnamed: U1.3 (+), U1.5 (+), U2.4 (Z)
unnamed: U2.3 (Z1), U2.15 (Y)
