mirdej/vmix/electronics/vm123-genlock-in/vm123-genlock-in.kicad_pcb

## KiCad design electronics/vm123-genlock-in/vm123-genlock-in.kicad_pcb (continued)

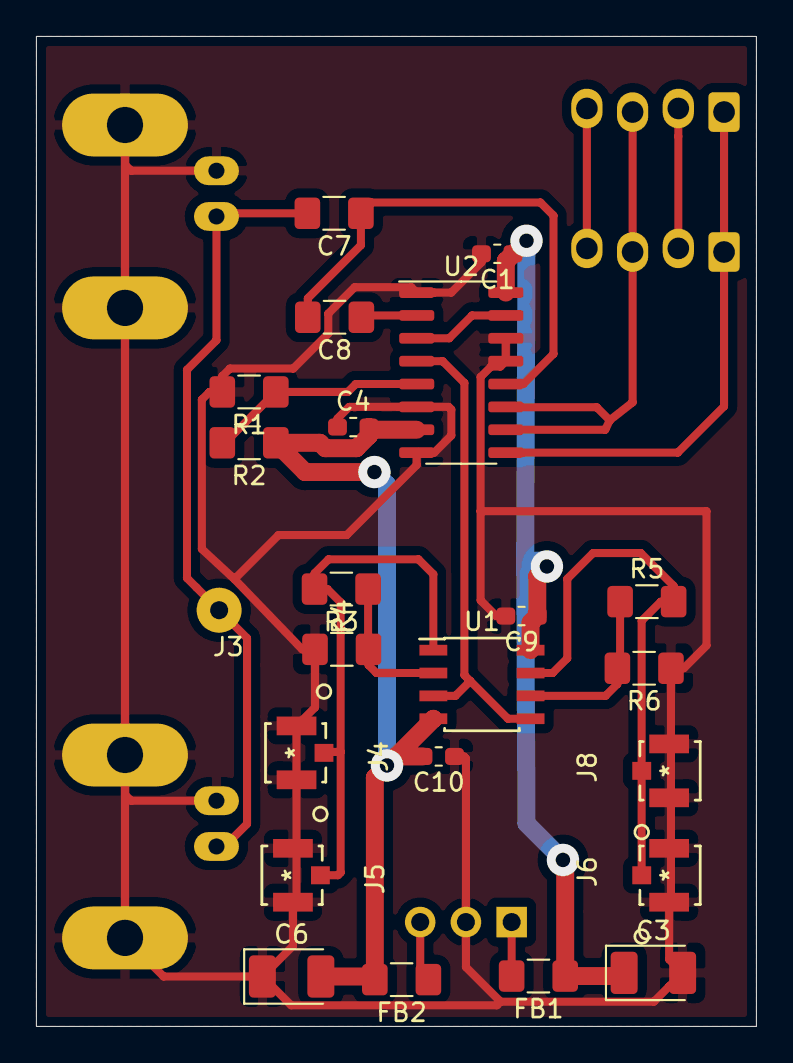
[picture p56: board vm123-genlock-in.kicad_pcb from above]

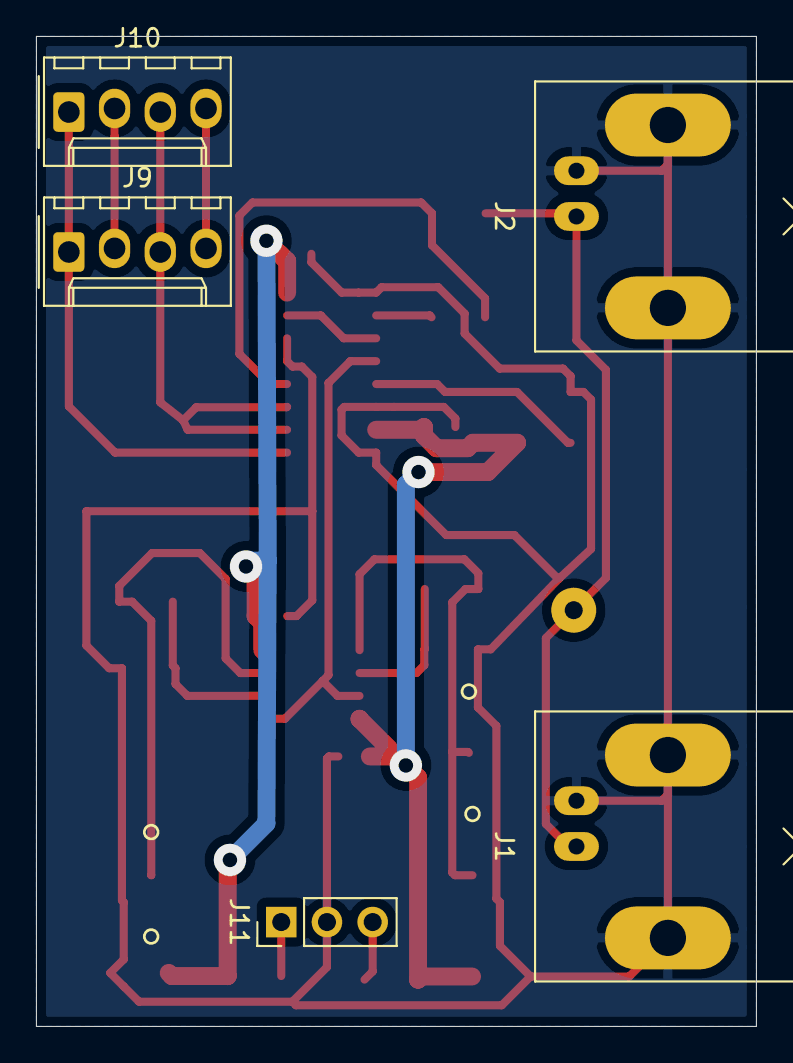
[picture p57: board vm123-genlock-in.kicad_pcb from below]

Board: 2 copper layers, 40.0 x 55.0 mm, 28 parts (5 on the bottom side), 19 nets.
