mirdej/vmix/electronics/vm109-busbuffer/vm109-busbuffer.kicad_pcb

## KiCad design electronics/vm109-busbuffer/vm109-busbuffer.kicad_pcb (2021-04-03)

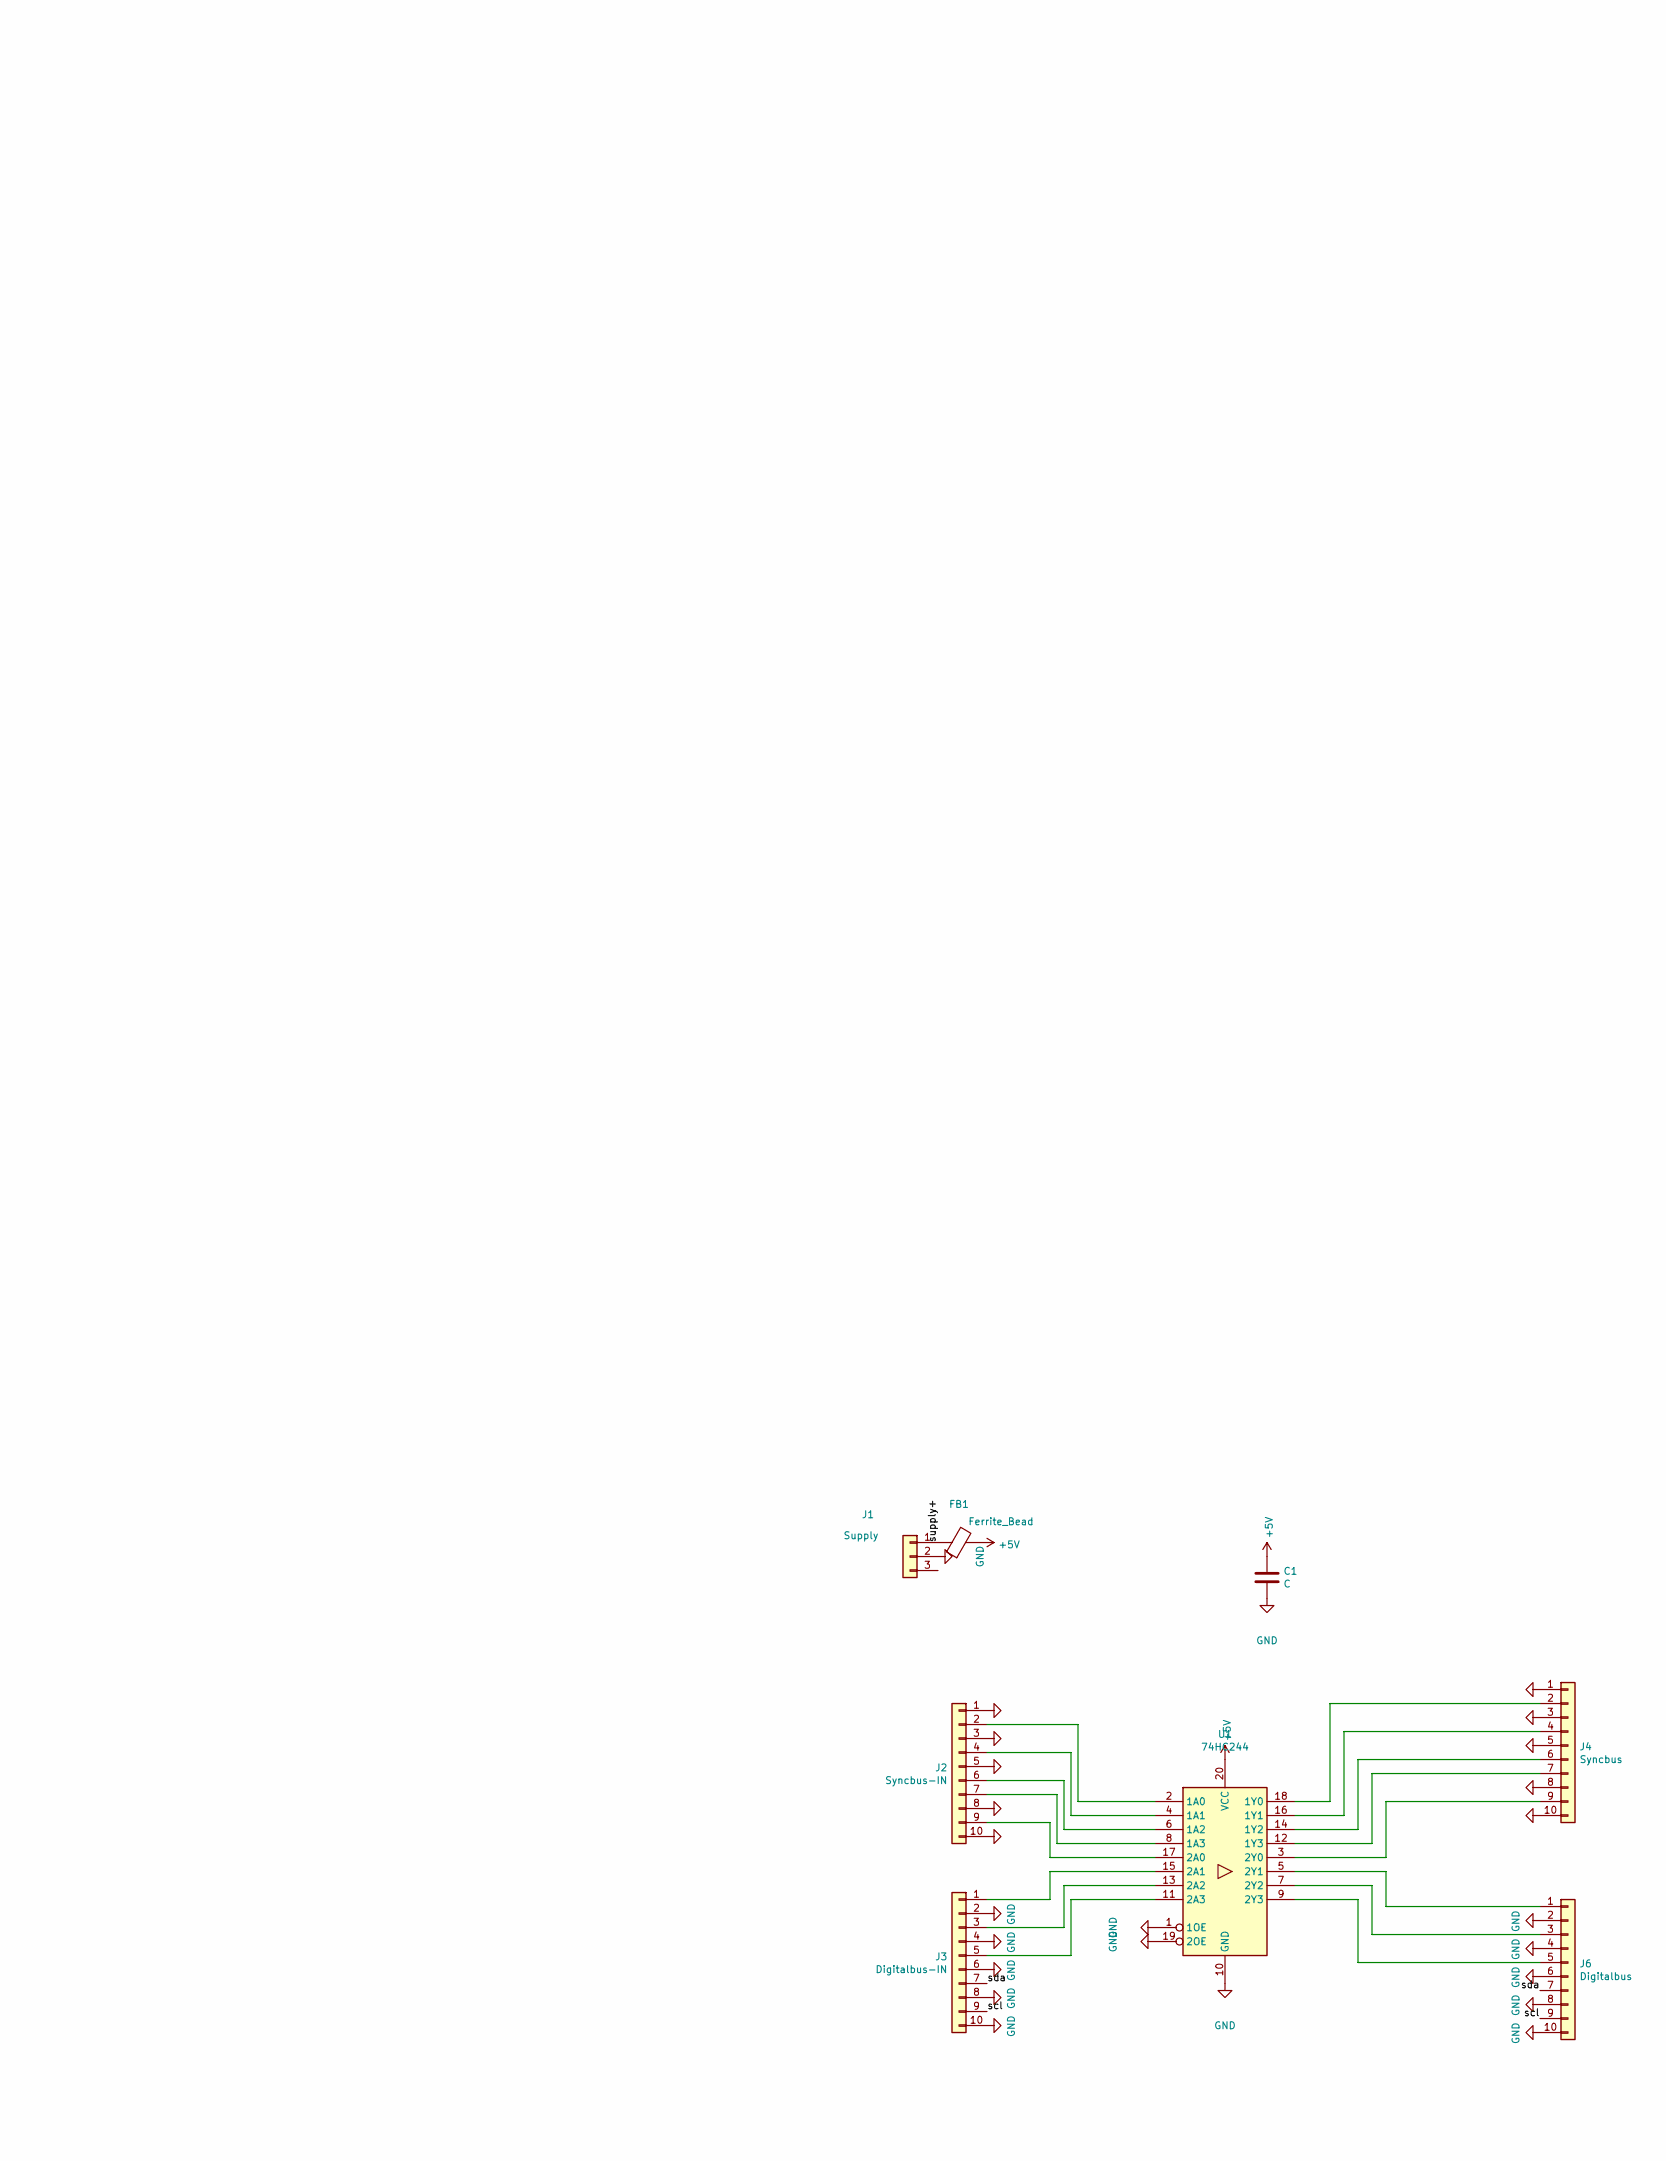
[picture p58: schematic vm109-busbuffer.sch, part in row 1, column 2]

Parts:
C1: C; R_0603_1608Metric_Pad1.05x0.95mm_HandSolder
FB1: Ferrite_Bead; L_0805_2012Metric_Pad1.15x1.40mm_HandSolder
J1: Supply; Molex_KK-254_AE-6410-03A_1x03_P2.54mm_Vertical
J2: Syncbus-IN; IDC-Header_2x05_P2.54mm_Vertical
J3: Digitalbus-IN; IDC-Header_2x05_P2.54mm_Vertical
J4: Syncbus; IDC-Header_2x05_P2.54mm_Vertical
J6: Digitalbus; IDC-Header_2x05_P2.54mm_Vertical
U1: 74HC244; SO-20_12.8x7.5mm_P1.27mm

Connections:
+5V: C1.1, FB1.2, U1.20 (VCC)
/scl: J3.9, J6.9
/sda: J3.7, J6.7
/supply+: FB1.1, J1.1
GND: C1.2, J1.2, J2.1, J2.3, J2.5, J2.8, J2.10, J3.2, J3.4, J3.6, J3.8, J3.10, J4.1, J4.3, J4.5, J4.8, J4.10, J6.2, J6.4, J6.6, J6.8, J6.10, U1.1 (1OE), U1.10 (GND), U1.19 (2OE)
unnamed: J2.2, U1.2 (1A0)
unnamed: J2.4, U1.4 (1A1)
unnamed: J2.6, U1.6 (1A2)
unnamed: J2.7, U1.8 (1A3)
unnamed: J2.9, U1.17 (2A0)
unnamed: J3.1, U1.15 (2A1)
unnamed: J3.3, U1.13 (2A2)
unnamed: J3.5, U1.11 (2A3)
unnamed: J4.2, U1.18 (1Y0)
unnamed: J4.4, U1.16 (1Y1)
unnamed: J4.6, U1.14 (1Y2)
unnamed: J4.7, U1.12 (1Y3)
unnamed: J4.9, U1.3 (2Y0)
unnamed: J6.1, U1.5 (2Y1)
unnamed: J6.3, U1.7 (2Y2)
unnamed: J6.5, U1.9 (2Y3)

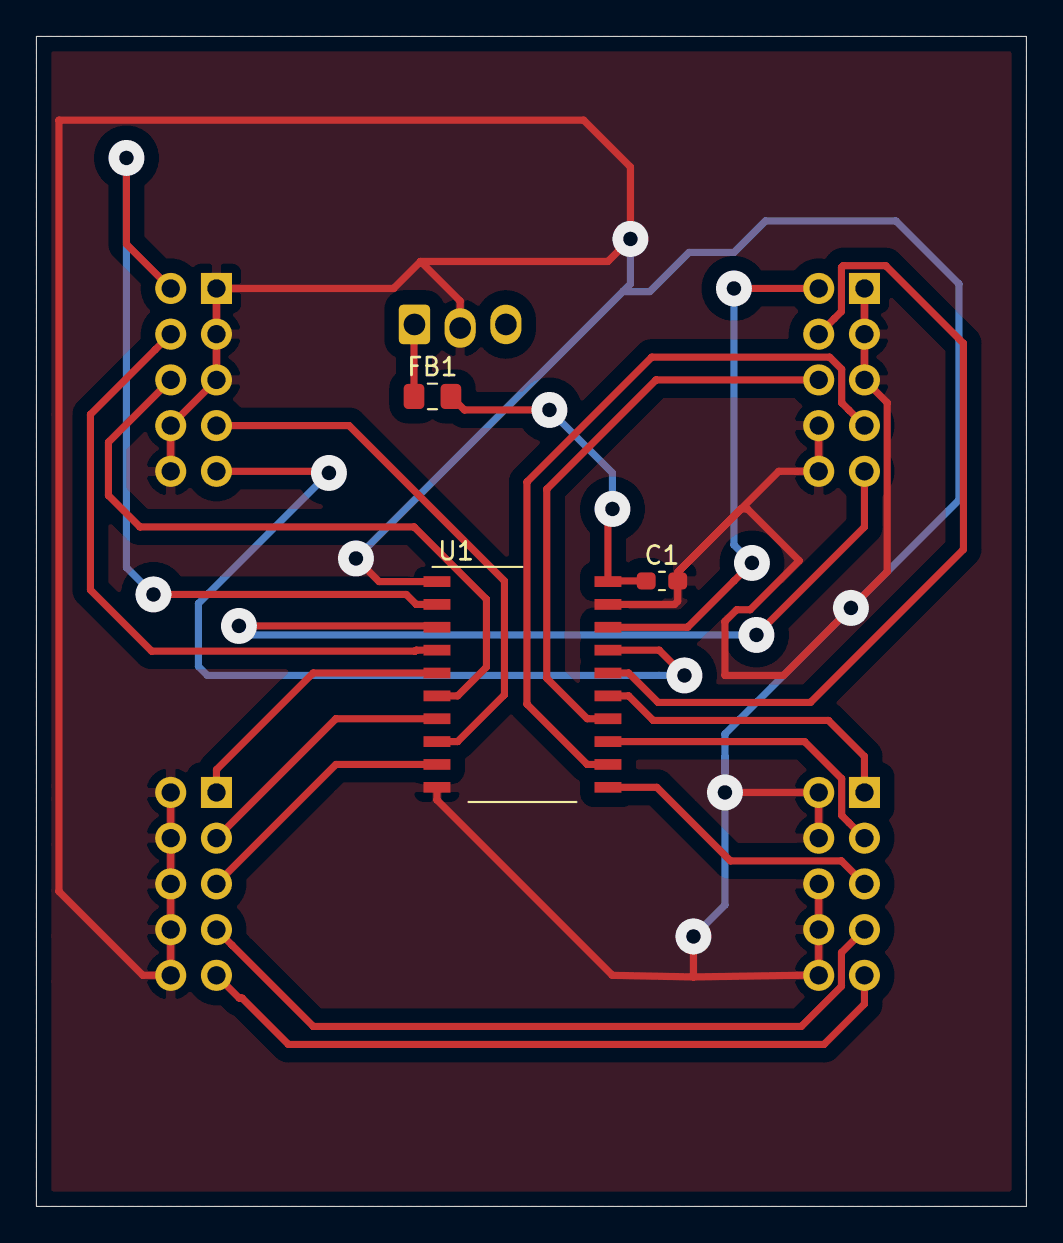
[picture p59: board vm109-busbuffer.kicad_pcb from above]

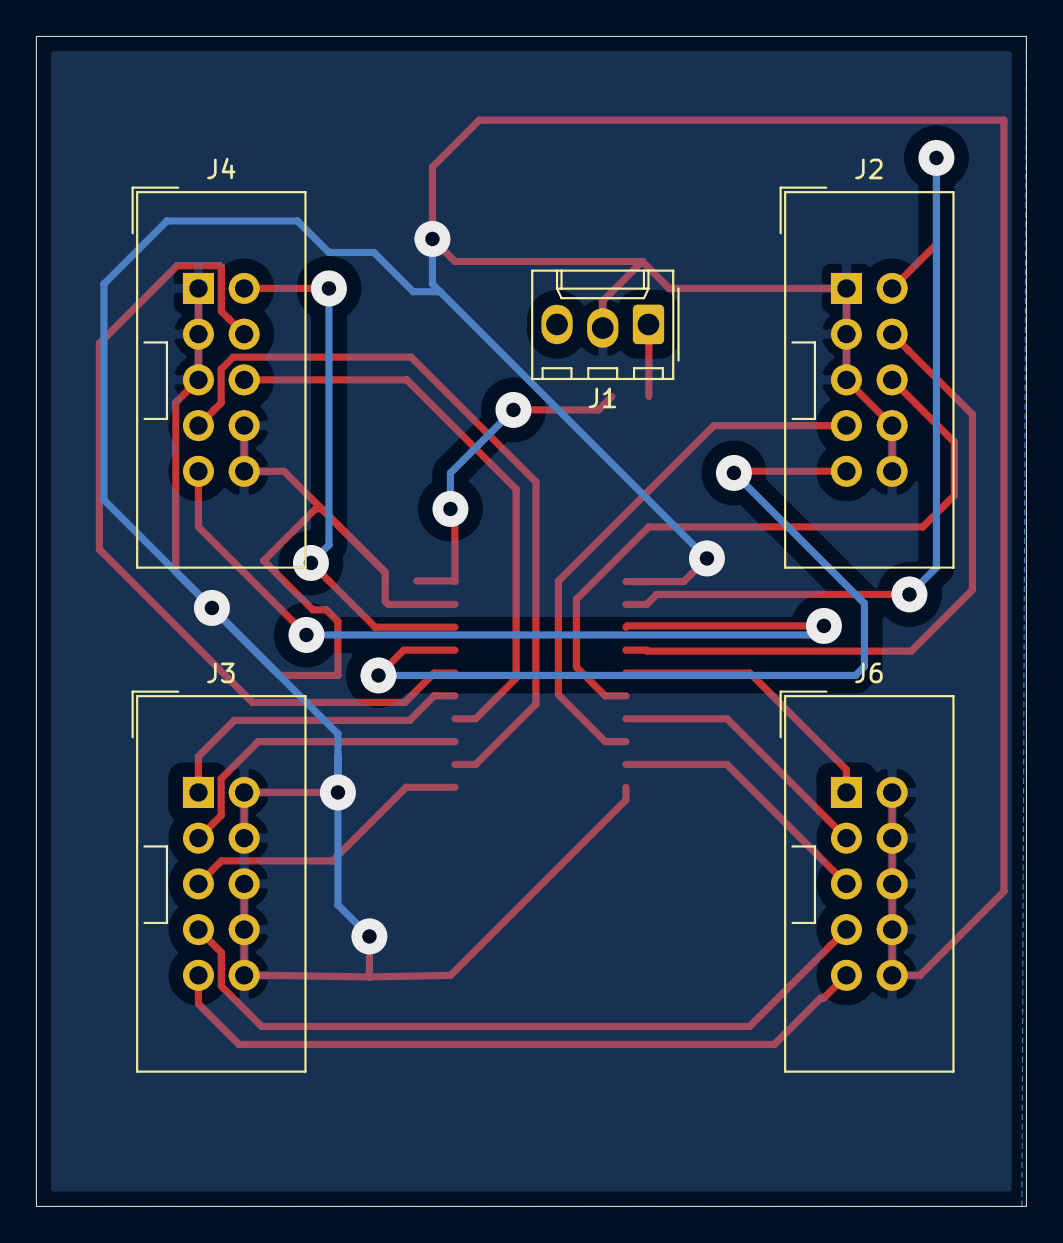
[picture p60: board vm109-busbuffer.kicad_pcb from below]

Board: 2 copper layers, 55.0 x 65.0 mm, 8 parts (5 on the bottom side), 21 nets.
