mirdej/vmix/vm020-output/vm020-output.kicad_pcb

## KiCad design vm020-output/vm020-output.kicad_pcb (2020-12-28)

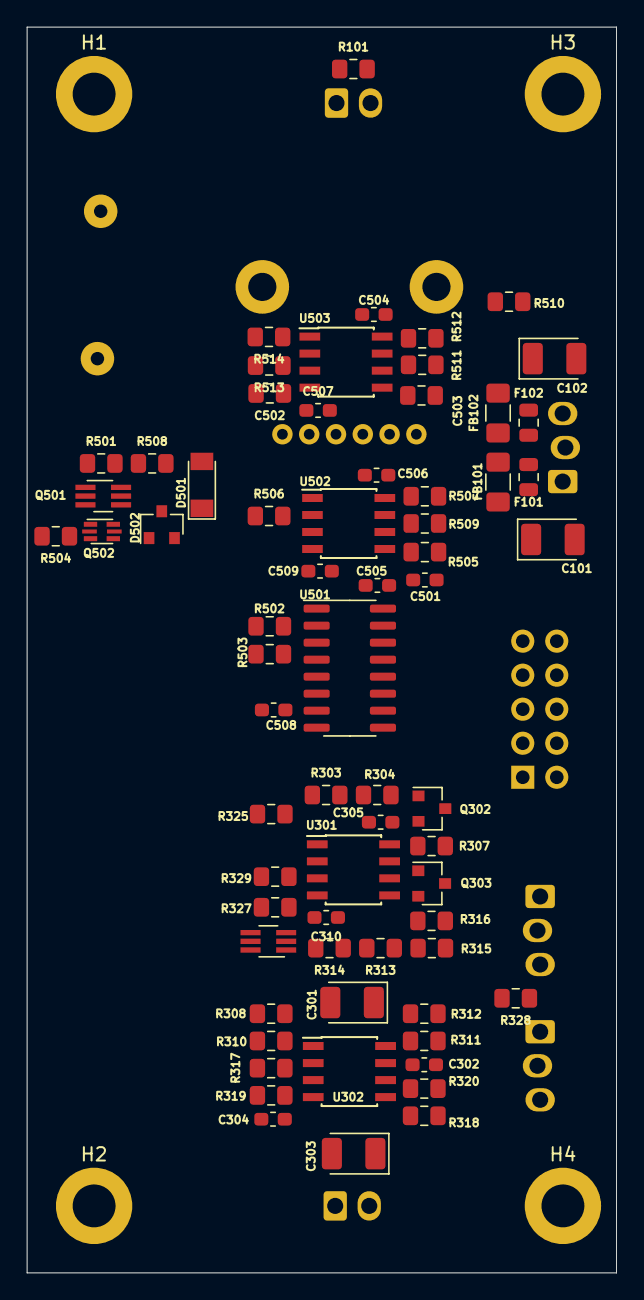
[picture p61: board vm020-output.kicad_pcb from above]

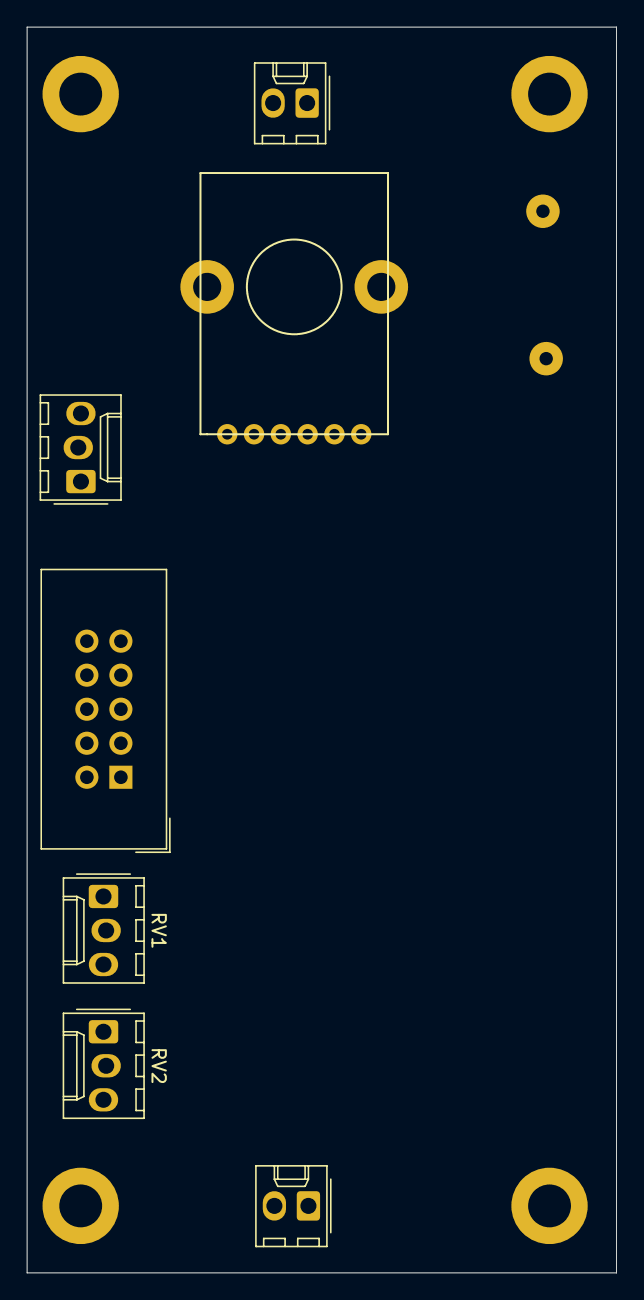
[picture p62: board vm020-output.kicad_pcb from below]

Board: 4 copper layers, 44.0 x 93.0 mm, 80 parts (7 on the bottom side), 47 nets, no tracks yet.

Parts:
C101, C102: 10u; CP_EIA-3528-21_Kemet-B_Pad1.50x2.35mm_HandSolder
C301, C303: 4u7; CP_EIA-3528-21_Kemet-B_Pad1.50x2.35mm_HandSolder
C302, C304, C305, C310, C504, C505, C506, C507, C508, C509: 100n; C_0603_1608Metric_Pad1.05x0.95mm_HandSolder
C501: 120p; C_0603_1608Metric_Pad1.05x0.95mm_HandSolder
C502, C503: 10p; C_0805_2012Metric_Pad1.15x1.40mm_HandSolder
D501: D; D_MiniMELF
D502: BAT54; D_SOT-23_ANK
F101, F102: Polyfuse; Fuse_0805_2012Metric
FB101, FB102: 330u; L_1206_3216Metric_Pad1.42x1.75mm_HandSolder
H1, H2, H3, H4: MountingHole_Pad; MountingHole_3.2mm_M3_ISO7380_Pad
J104: OUT; Molex_KK-254_AE-6410-02A_1x02_P2.54mm_Vertical
J105: Power; Molex_KK-254_AE-6410-03A_1x03_P2.54mm_Vertical
J106: SIFF-INPUT; Molex_KK-254_AE-6410-02A_1x02_P2.54mm_Vertical
J109: gnd; Solderpad_1mm
J110: SYNC-BUS; IDC-Header_2x05_P2.54mm_Vertical
Q302: PNP; SOT-23_BEC
Q303: BC847; SOT-23_BEC
Q304, Q501: PMBT3906YS; SOT-363_SC-70-6_Handsoldering
Q502: PEMX1; SOT-666
R101, R320, R510: 75; R_0805_2012Metric_Pad1.15x1.40mm_HandSolder
R303, R307, R315, R317, R327: 10k; R_0805_2012Metric_Pad1.15x1.40mm_HandSolder
R304, R316: 3k3; R_0805_2012Metric_Pad1.15x1.40mm_HandSolder
R308, R502: 300; R_0805_2012Metric_Pad1.15x1.40mm_HandSolder
R310: 560; R_0805_2012Metric_Pad1.15x1.40mm_HandSolder
R311, R318, R319: 1k; R_0805_2012Metric_Pad1.15x1.40mm_HandSolder
R312: 100; R_0805_2012Metric_Pad1.15x1.40mm_HandSolder
R313: 5.1k; R_0805_2012Metric_Pad1.15x1.40mm_HandSolder
R314: 15k; R_0805_2012Metric_Pad1.15x1.40mm_HandSolder
R325, R329, R503: 4k7; R_0805_2012Metric_Pad1.15x1.40mm_HandSolder
R328: 100k; R_0805_2012Metric_Pad1.15x1.40mm_HandSolder
R501, R505: 120; R_0805_2012Metric_Pad1.15x1.40mm_HandSolder
R504: 5k6; R_0805_2012Metric_Pad1.15x1.40mm_HandSolder
R506: 330; R_0805_2012Metric_Pad1.15x1.40mm_HandSolder
R507, R509, R511, R512, R513, R514: 220; R_0805_2012Metric_Pad1.15x1.40mm_HandSolder
R508: 47k; R_0805_2012Metric_Pad1.15x1.40mm_HandSolder
RV1, RV2: R_POT; Molex_KK-254_AE-6410-03A_1x03_P2.54mm_Vertical
RV501: R_POT_Dual; RK12L123
TP501: TestPoint; Solderpad_1mm
U301, U502, U503: LMH6643; SOIC-8_3.9x4.9mm_P1.27mm
U302: LT1228; SOIC-8_3.9x4.9mm_P1.27mm
U501: 4053; SOIC-16_3.9x9.9mm_P1.27mm

Connections:
+5V: C101.1, C301.1, C302.2, C305.2, C504.2, C505.2, C506.2, FB101.2, Q502.6, R304.1, R327.1, R501.2, R508.1, RV1.1, RV2.1, U301.8, U302.7, U501.16, U502.8, U503.8
-5V: C102.2, C303.2, C304.2, C310.2, C507.1, C508.1, C509.1, FB102.2, Q501.3, R314.2, R315.2, R316.2, R503.2, R504.1, RV1.3, RV2.3, U301.4, U302.4, U501.7, U502.4, U503.4
/Resyncer/OUTPUT: R101.1, R507.1, U502.7
/Resyncer/clipper_out: Q501.4, Q502.1, R506.1, U501.13
/Resyncer/delayed_burst: R514.1, TP501.1, U501.12, U503.1
/Resyncer/synctip: R502.2, R503.1, U501.5
/Scabi/INPUT: J106.1, R317.1
/supply+: F101.2, J105.1
/supply-: F102.2, J105.3
GND: C101.2, C102.1, C301.2, C302.1, C303.1, C304.1, C305.1, C310.1, C501.2, C502.2, C503.2, C504.1, C505.1, C506.1, C507.2, C508.2, C509.2, D501.1, D502.2, H1.1, H2.1, H3.1, H4.1, J104.2, J105.2, J106.2, J109.1, J110.1, J110.3, J110.5, J110.6, J110.8, J110.10, Q304.1, Q304.3, Q304.5, Q502.4, R307.1, R308.1, R310.1, R312.1, R319.1, R502.1, R509.1, U301.3, U301.5, U501.6, U501.8, U501.10
unnamed: C501.1, R505.1, U502.5
unnamed: C502.1, RV501.6, U503.3
unnamed: C503.1, RV501.3, U503.5
unnamed: D501.2, Q501.1, R501.1
unnamed: D502.1, Q502.2, Q502.3, Q502.5, R508.2
unnamed: F101.1, FB101.1
unnamed: F102.1, FB102.1
unnamed: J104.1, R101.2
unnamed: Q302.B, R303.2, U301.7
unnamed: Q302.C, Q303.C, R308.2, U302.1
unnamed: Q302.E, R304.2
unnamed: Q303.B, R307.2, R315.1
unnamed: Q303.E, R316.1
unnamed: Q304.2, R325.2, U301.1
unnamed: Q304.4, R327.2, R329.2
unnamed: Q304.6, R318.2
unnamed: Q501.2, Q501.5, Q501.6, R504.2
unnamed: R303.1, R313.2, R314.1, U301.6
unnamed: R310.2, U302.2
unnamed: R311.1, R320.2, U302.6
unnamed: R311.2, R312.2, U302.8
unnamed: R317.2, R319.2, U302.3
unnamed: R318.1, U302.5
unnamed: R325.1, R328.2, R329.1, U301.2
unnamed: R505.2, U501.4
unnamed: R506.2, U502.1, U502.2
unnamed: R507.2, R509.2, U502.6
unnamed: R510.2, R511.2, RV501.1, RV501.2
unnamed: R511.1, R512.2, U503.6
unnamed: R512.1, R513.2, RV501.4, RV501.5, U503.7
unnamed: R513.1, R514.2, U503.2
unnamed: U501.2, U501.14
unnamed: U501.3, U501.15
bias_cv: R313.1, RV1.2
hsync: J110.2, U501.9
porch: J110.4, U501.11
scale_cv: R328.1, RV2.2
