mirdej/vmix/vm013-analog-section/vm013-analog-section.kicad_pcb

## KiCad design vm013-analog-section/vm013-analog-section.kicad_pcb (2020-12-27)

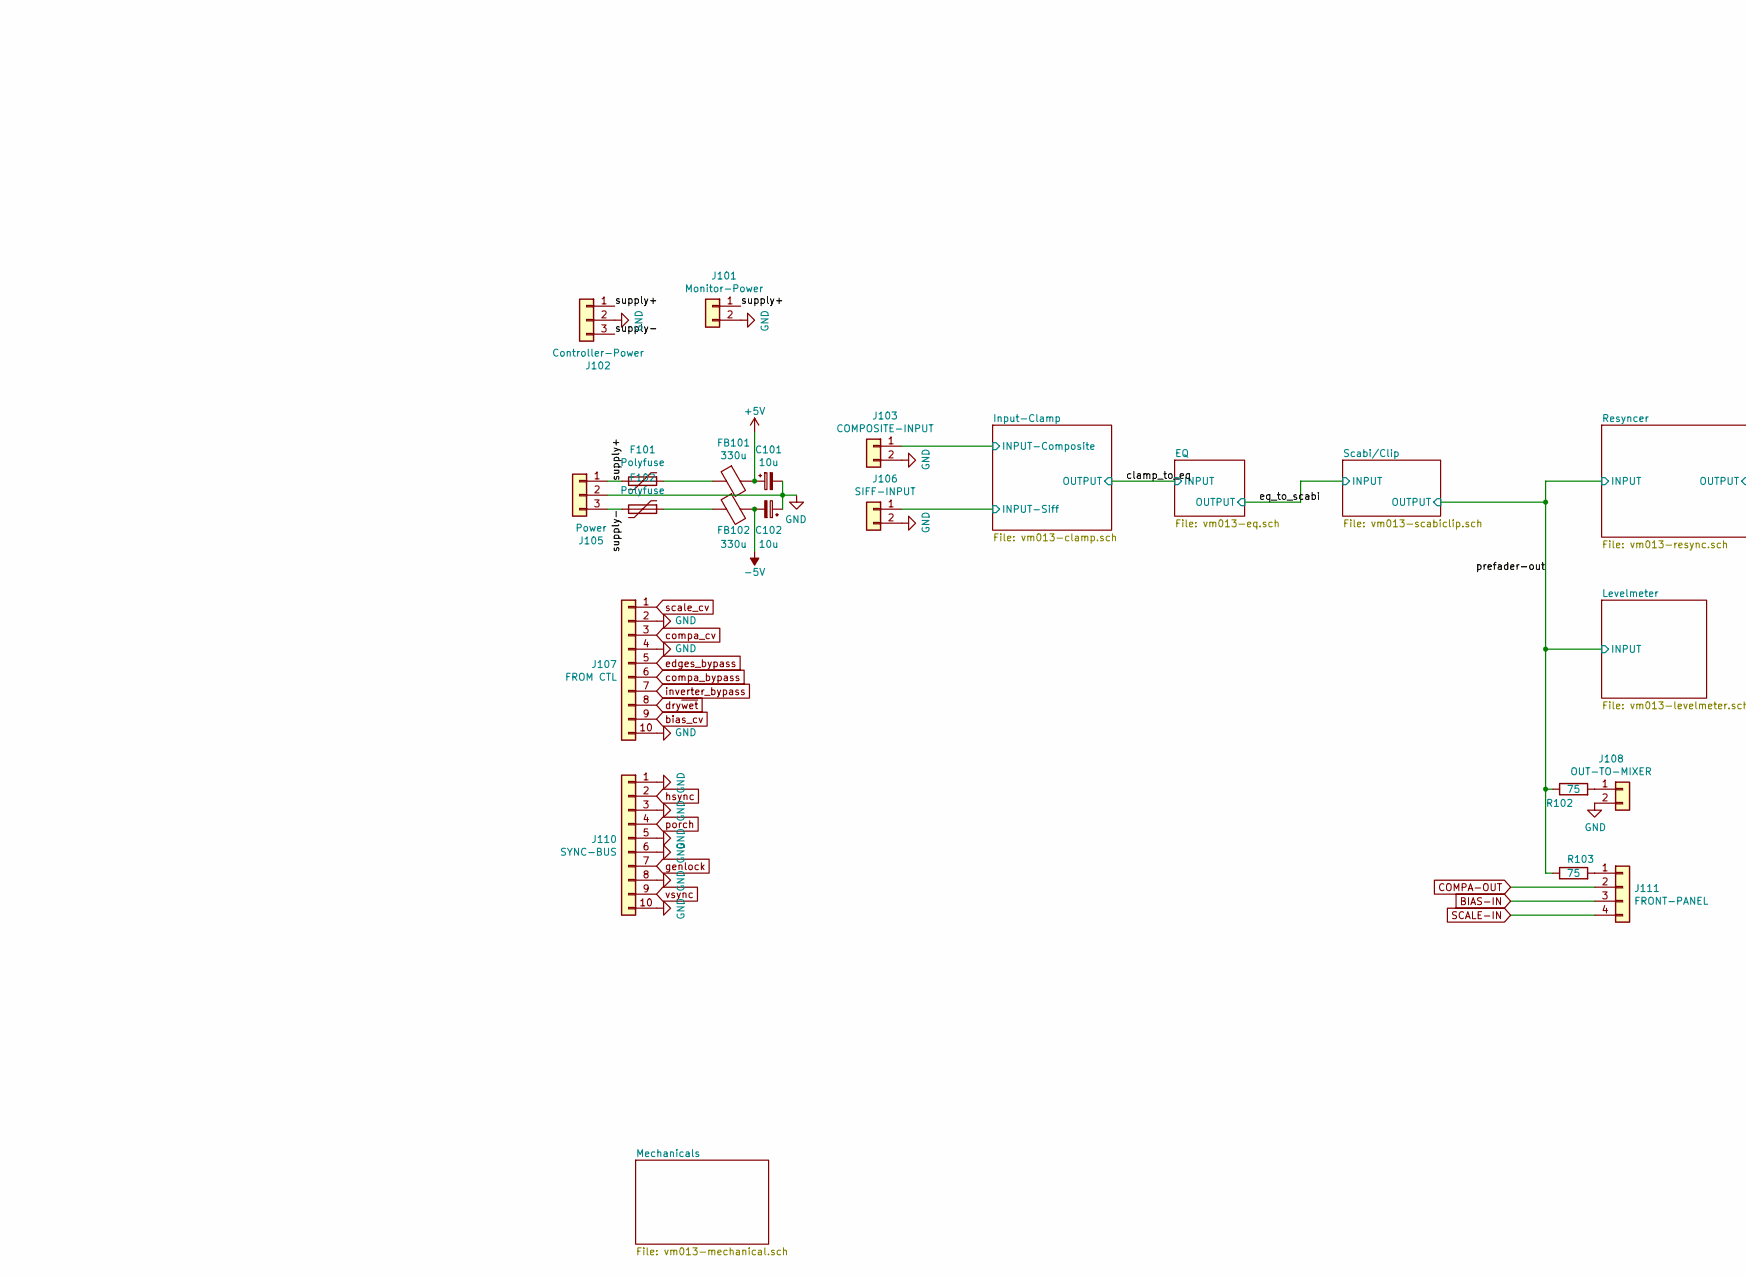
[picture p63: schematic vm013-analog-section.sch, vMIX20-Analog-Signal-Section, part in row 2, column 2]

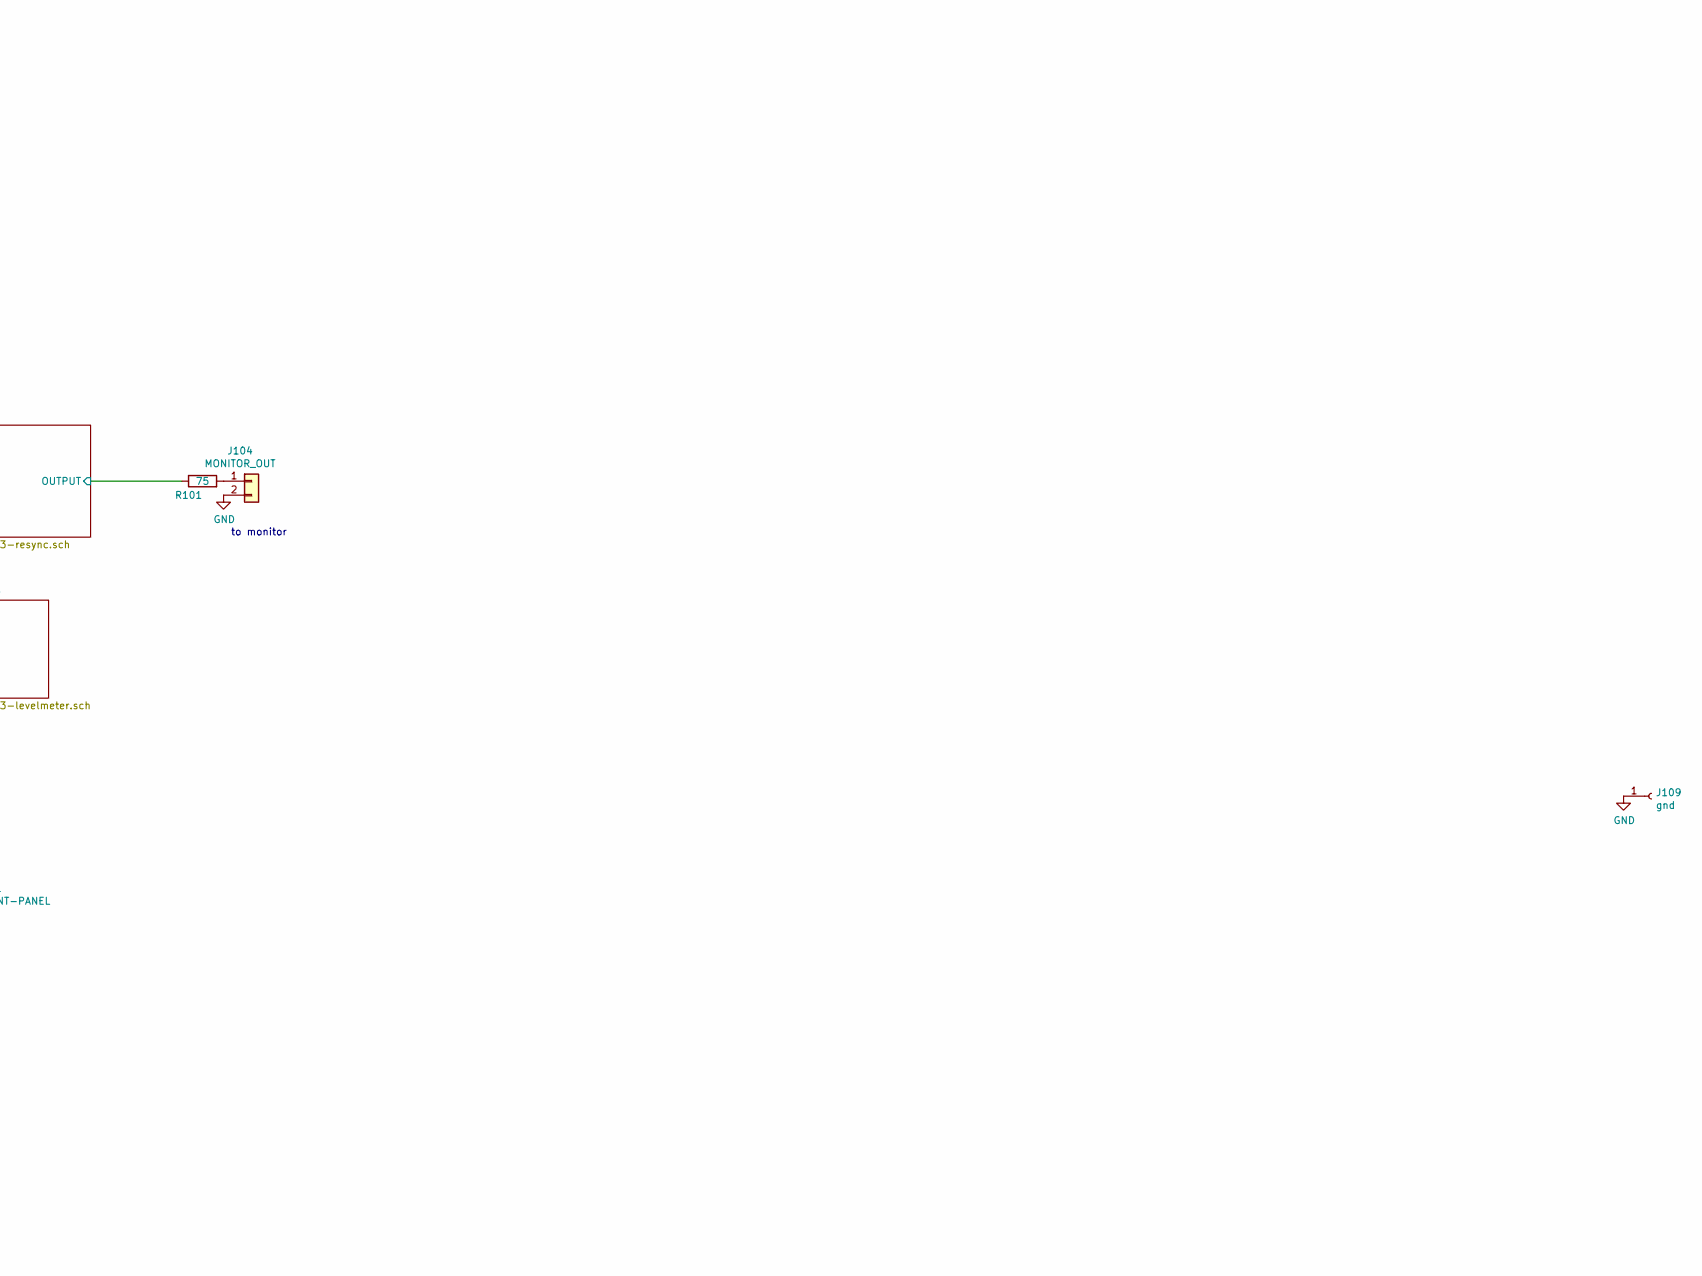
[picture p64: schematic vm013-analog-section.sch, vMIX20-Analog-Signal-Section, part in row 2, column 3]

Parts:
C101, C102: 10u; CP_EIA-3528-21_Kemet-B_Pad1.50x2.35mm_HandSolder
F101, F102: Polyfuse; Fuse_0805_2012Metric
FB101, FB102: 330u; L_0805_2012Metric_Pad1.15x1.40mm_HandSolder
J101: Monitor-Power; Molex_KK-254_AE-6410-02A_1x02_P2.54mm_Vertical
J102: Controller-Power; Molex_KK-254_AE-6410-03A_1x03_P2.54mm_Vertical
J103: COMPOSITE-INPUT; Molex_KK-254_AE-6410-02A_1x02_P2.54mm_Vertical
J104: MONITOR_OUT; Molex_KK-254_AE-6410-02A_1x02_P2.54mm_Vertical
J105: Power; Molex_KK-254_AE-6410-03A_1x03_P2.54mm_Vertical
J106: SIFF-INPUT; Molex_KK-254_AE-6410-02A_1x02_P2.54mm_Vertical
J107: FROM CTL; IDC-Header_2x05_P2.54mm_Vertical
J108: OUT-TO-MIXER; Molex_KK-254_AE-6410-02A_1x02_P2.54mm_Vertical
J109: gnd; Solderpad_1mm
J110: SYNC-BUS; IDC-Header_2x05_P2.54mm_Vertical
J111: FRONT-PANEL; Molex_KK-254_AE-6410-04A_1x04_P2.54mm_Vertical
R101, R102, R103: 75; R_0805_2012Metric_Pad1.15x1.40mm_HandSolder

Connections:
+5V: C101.1, FB101.2; also elsewhere on the board
-5V: C102.2, FB102.2; also elsewhere on the board
/Input-Clamp/INPUT-Composite: J103.1; also elsewhere on the board
/Input-Clamp/INPUT-Siff: J106.1; also elsewhere on the board
/Resyncer/OUTPUT: R101.1; also elsewhere on the board
/prefader-out: R102.1, R103.1; also elsewhere on the board
/supply+: F101.2, J101.1, J102.1, J105.1
/supply-: F102.2, J102.3, J105.3
BIAS-IN: J111.3; also elsewhere on the board
COMPA-OUT: J111.2; also elsewhere on the board
GND: C101.2, C102.1, J101.2, J102.2, J103.2, J104.2, J105.2, J106.2, J107.2, J107.4, J107.10, J108.2, J109.1, J110.1, J110.3, J110.5, J110.6, J110.8, J110.10; also elsewhere on the board
unnamed: F101.1, FB101.1
unnamed: F102.1, FB102.1
unnamed: J104.1, R101.2
unnamed: J108.1, R102.2
unnamed: J111.1, R103.2
SCALE-IN: J111.4; also elsewhere on the board
bias_cv: J107.9; also elsewhere on the board
compa_bypass: J107.6; also elsewhere on the board
compa_cv: J107.3; also elsewhere on the board
dry~wet~: J107.8; also elsewhere on the board
edges_bypass: J107.5; also elsewhere on the board
genlock: J110.7; also elsewhere on the board
hsync: J110.2; also elsewhere on the board
inverter_bypass: J107.7; also elsewhere on the board
porch: J110.4; also elsewhere on the board
scale_cv: J107.1; also elsewhere on the board
vsync: J110.9; also elsewhere on the board

Notes on the sheet:
to monitor
