mirdej/vmix/vm013-analog-section/vm013-analog-section.kicad_pcb

## KiCad design vm013-analog-section/vm013-analog-section.kicad_pcb (continued)

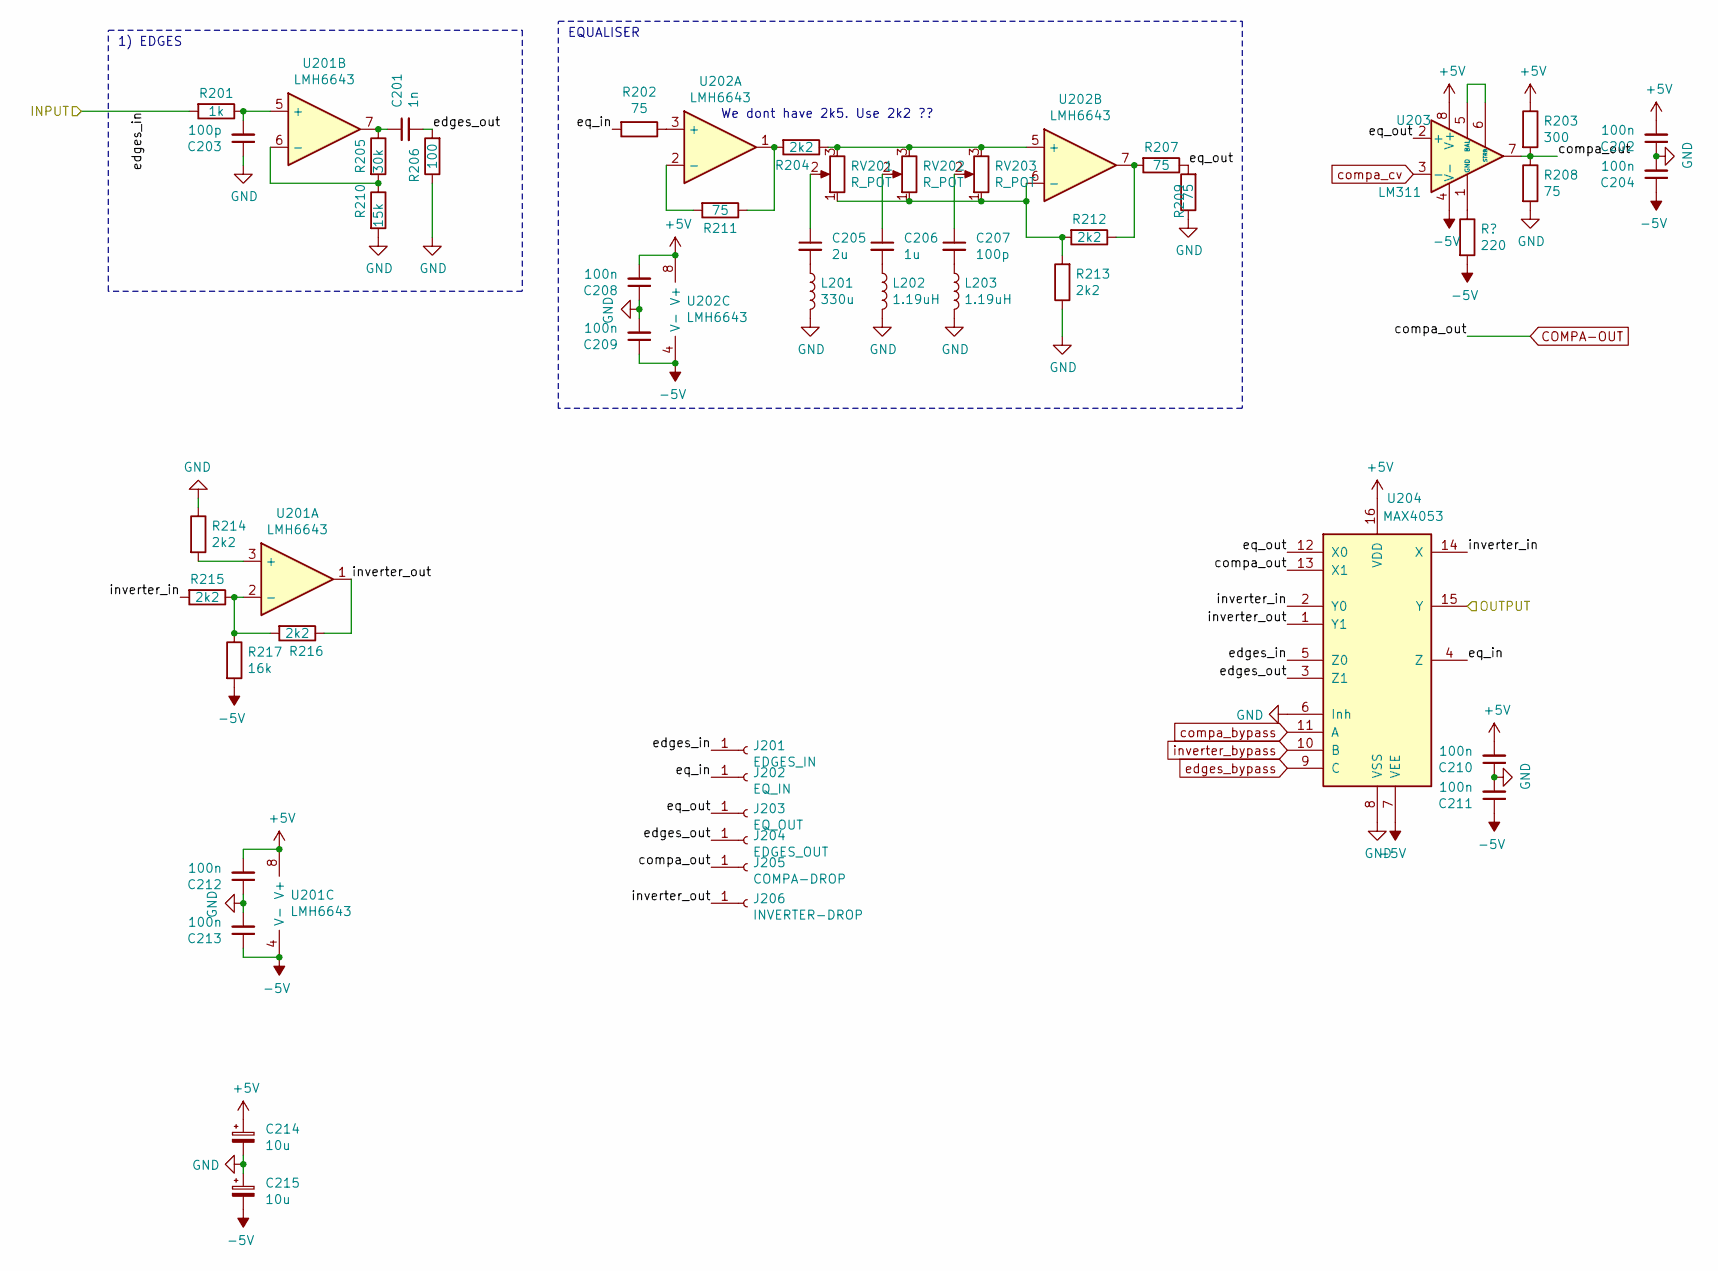
[picture p65: schematic vm013-eq.sch, vMIX20-EQ and Effects]

Parts:
C201: 1n; C_0805_2012Metric_Pad1.15x1.40mm_HandSolder
C202, C204, C208, C209, C210, C211, C212, C213: 100n; C_0603_1608Metric_Pad1.05x0.95mm_HandSolder
C203, C207: 100p; C_0805_2012Metric_Pad1.15x1.40mm_HandSolder
C205: 2u; C_1206_3216Metric_Pad1.42x1.75mm_HandSolder
C206: 1u; C_1206_3216Metric_Pad1.42x1.75mm_HandSolder
C214, C215: 10u; CP_EIA-3528-21_Kemet-B_Pad1.50x2.35mm_HandSolder
J201: EDGES_IN; Solderpad_1mm
J202: EQ_IN; Solderpad_1mm
J203: EQ_OUT; Solderpad_1mm
J204: EDGES_OUT; Solderpad_1mm
J205: COMPA-DROP; Solderpad_1mm
J206: INVERTER-DROP; Solderpad_1mm
L201: 330u; L_1210_3225Metric_Pad1.42x2.65mm_HandSolder
L202, L203: 1.19uH; L_1210_3225Metric_Pad1.42x2.65mm_HandSolder
R201: 1k; R_0805_2012Metric_Pad1.15x1.40mm_HandSolder
R202, R207, R208, R209, R211: 75; R_0805_2012Metric_Pad1.15x1.40mm_HandSolder
R203: 300; R_0805_2012Metric_Pad1.15x1.40mm_HandSolder
R204, R212, R213, R214, R215, R216: 2k2; R_0805_2012Metric_Pad1.15x1.40mm_HandSolder
R205: 30k; R_0805_2012Metric_Pad1.15x1.40mm_HandSolder
R206: 100; R_0805_2012Metric_Pad1.15x1.40mm_HandSolder
R210: 15k; R_0805_2012Metric_Pad1.15x1.40mm_HandSolder
R217: 16k; R_0805_2012Metric_Pad1.15x1.40mm_HandSolder
RV201, RV202, RV203: R_POT; Potentiometer_Alps_RK09K_Single_Horizontal
U201, U202: LMH6643; SOIC-8_3.9x4.9mm_P1.27mm
U203: LM311; SOIC-8_3.9x4.9mm_P1.27mm
U204: MAX4053; SOP-16_4.55x10.3mm_P1.27mm

Connections:
+5V: C202.2, C208.2, C210.2, C212.2, C214.1, R203.1, U201.8 (V+), U202.8 (V+), U203.8 (V+), U204.16 (VDD); also elsewhere on the board
-5V: C204.1, C209.1, C211.1, C213.1, C215.2, R217.2, U201.4 (V-), U202.4 (V-), U203.4 (V-), U204.7 (VEE); also elsewhere on the board
/EQ/edges_out: C201.2, J204.1, R206.2, U204.3 (Z1)
/EQ/eq_in: J202.1, R202.2, U204.4 (Z)
/EQ/eq_out: J203.1, R207.1, R209.2, U203.2 (+), U204.12 (X0)
/EQ/inverter_in: R215.2, U204.2 (Y0), U204.14 (X)
/EQ/inverter_out: J206.1, R216.1, U201.1, U204.1 (Y1)
/clamp_to_eq: J201.1, R201.2, U204.5 (Z0); also elsewhere on the board
/eq_to_scabi: U204.15 (Y); also elsewhere on the board
COMPA-OUT: J205.1, R203.2, R208.1, U203.7, U204.13 (X1); also elsewhere on the board
GND: C202.1, C203.1, C204.2, C208.1, C209.2, C210.1, C211.2, C212.1, C213.2, C214.2, C215.1, L201.2, L202.2, L203.2, R206.1, R208.2, R209.1, R210.2, R213.1, R214.1, U203.1 (GND), U204.6 (Inh), U204.8 (VSS); also elsewhere on the board
unnamed: C201.1, R205.1, U201.7
unnamed: C203.2, R201.1, U201.5 (+)
unnamed: C205.1, RV201.2
unnamed: C205.2, L201.1
unnamed: C206.1, RV202.2
unnamed: C206.2, L202.1
unnamed: C207.1, RV203.2
unnamed: C207.2, L203.1
unnamed: R202.1, U202.3 (+)
unnamed: R204.1, RV201.3, RV202.3, RV203.3, U202.5 (+)
unnamed: R204.2, R211.1, U202.1
unnamed: R205.2, R210.1, U201.6 (-)
unnamed: R207.2, R212.1, U202.7
unnamed: R211.2, U202.2 (-)
unnamed: R212.2, R213.2, RV201.1, RV202.1, RV203.1, U202.6 (-)
unnamed: R214.2, U201.3 (+)
unnamed: R215.1, R216.2, R217.1, U201.2 (-)
unnamed: U203.5 (BAL), U203.6 (STRB)
compa_bypass: U204.11 (A); also elsewhere on the board
compa_cv: U203.3 (-); also elsewhere on the board
edges_bypass: U204.9 (C); also elsewhere on the board
inverter_bypass: U204.10 (B); also elsewhere on the board

Notes on the sheet:
EQUALISER
We dont have 2k5. Use 2k2 ??
1) EDGES

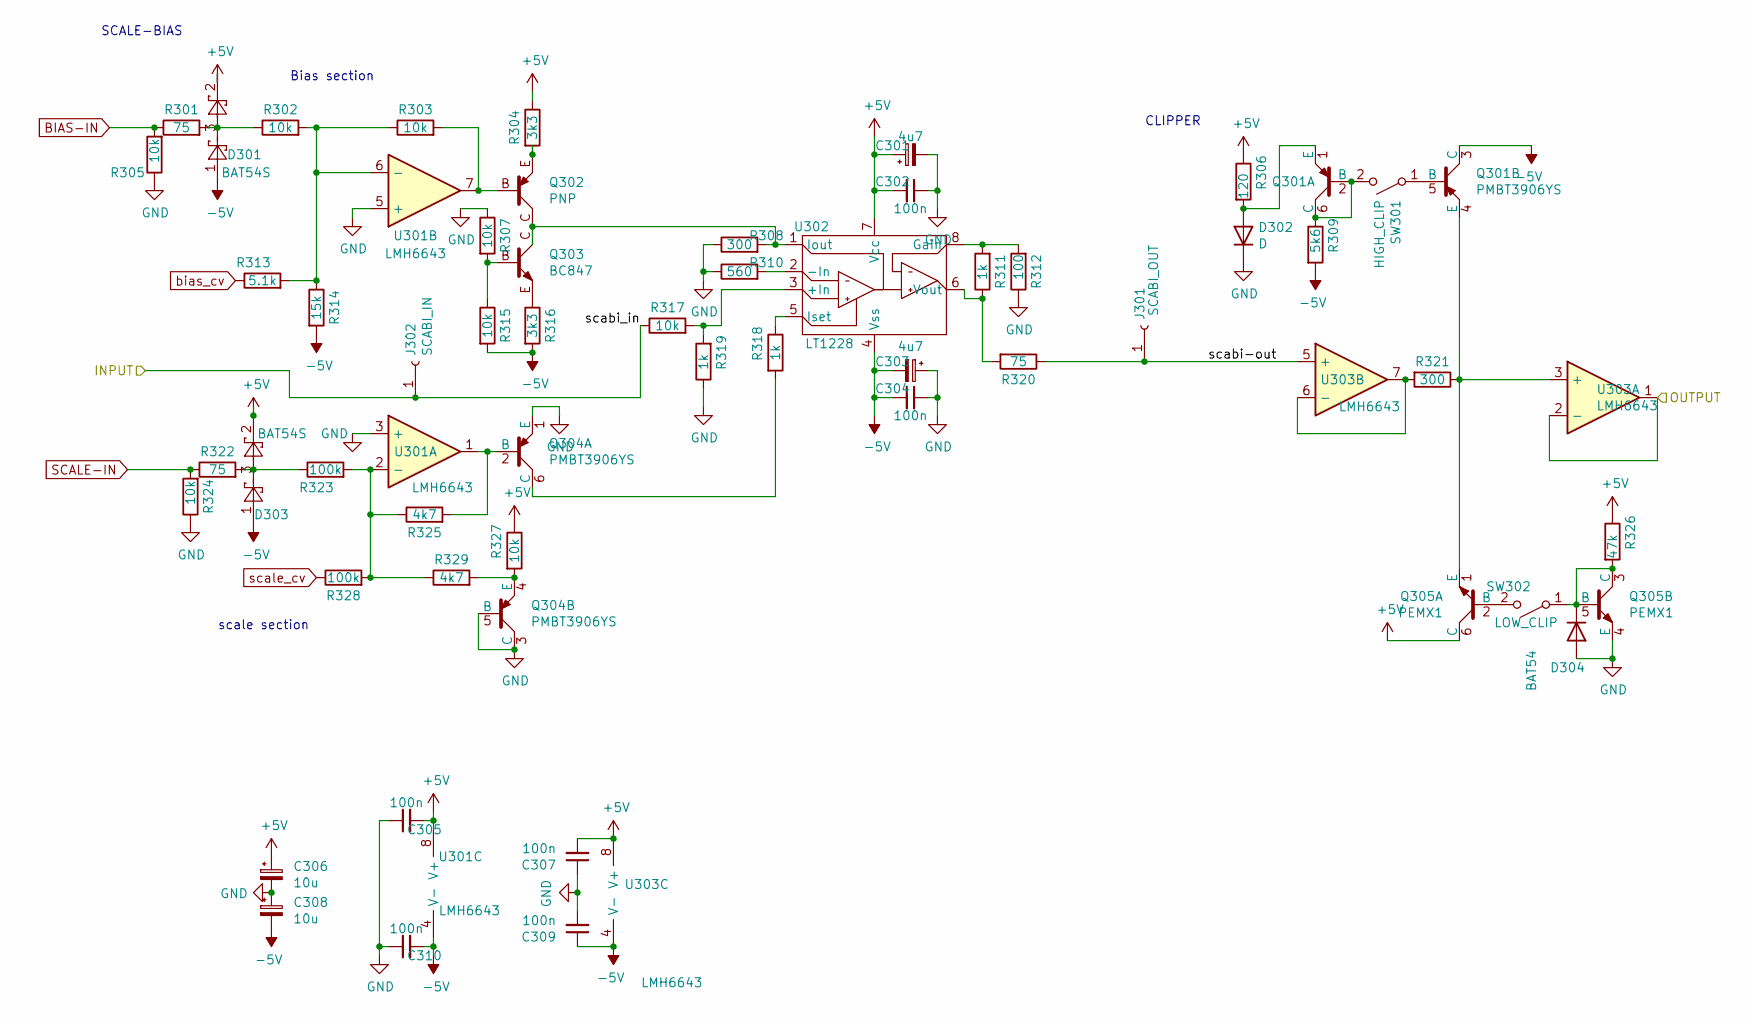
[picture p66: schematic vm013-scabiclip.sch, vMIX20-Scale,Bias, Clip]

Parts:
C301, C303: 4u7; CP_EIA-3528-21_Kemet-B_Pad1.50x2.35mm_HandSolder
C302, C304, C305, C307, C309, C310: 100n; C_0603_1608Metric_Pad1.05x0.95mm_HandSolder
C306, C308: 10u; CP_EIA-3528-21_Kemet-B_Pad1.50x2.35mm_HandSolder
D301, D303: BAT54S; SOT-23
D302: D; D_MiniMELF
D304: BAT54; D_SOT-23_ANK
J301: SCABI_OUT; Solderpad_1mm
J302: SCABI_IN; Solderpad_1mm
Q301, Q304: PMBT3906YS; SOT-363_SC-70-6_Handsoldering
Q302: PNP; SOT-23_BEC
Q303: BC847; SOT-23_BEC
Q305: PEMX1; SOT-666
R301, R320, R322: 75; R_0805_2012Metric_Pad1.15x1.40mm_HandSolder
R302, R303, R305, R307, R315, R317, R324, R327: 10k; R_0805_2012Metric_Pad1.15x1.40mm_HandSolder
R304, R316: 3k3; R_0805_2012Metric_Pad1.15x1.40mm_HandSolder
R306: 120; R_0805_2012Metric_Pad1.15x1.40mm_HandSolder
R308, R321: 300; R_0805_2012Metric_Pad1.15x1.40mm_HandSolder
R309: 5k6; R_0805_2012Metric_Pad1.15x1.40mm_HandSolder
R310: 560; R_0805_2012Metric_Pad1.15x1.40mm_HandSolder
R311, R318, R319: 1k; R_0805_2012Metric_Pad1.15x1.40mm_HandSolder
R312: 100; R_0805_2012Metric_Pad1.15x1.40mm_HandSolder
R313: 5.1k; R_0805_2012Metric_Pad1.15x1.40mm_HandSolder
R314: 15k; R_0805_2012Metric_Pad1.15x1.40mm_HandSolder
R323, R328: 100k; R_0805_2012Metric_Pad1.15x1.40mm_HandSolder
R325, R329: 4k7; R_0805_2012Metric_Pad1.15x1.40mm_HandSolder
R326: 47k; R_0805_2012Metric_Pad1.15x1.40mm_HandSolder
SW301: HIGH_CLIP; Molex_KK-254_AE-6410-02A_1x02_P2.54mm_Vertical
SW302: LOW_CLIP; Molex_KK-254_AE-6410-02A_1x02_P2.54mm_Vertical
U301, U303: LMH6643; SOIC-8_3.9x4.9mm_P1.27mm
U302: LT1228; SOIC-8_3.9x4.9mm_P1.27mm

Connections:
+5V: C301.1, C302.2, C305.2, C306.1, C307.2, D301.2, D303.2, Q305.6 (C), R304.1, R306.1, R326.1, R327.1, U301.8 (V+), U302.7 (Vcc), U303.8 (V+); also elsewhere on the board
-5V: C303.2, C304.2, C308.2, C309.1, C310.2, D301.1, D303.1, Q301.3 (C), R309.2, R314.2, R315.2, R316.2, U301.4 (V-), U302.4 (Vss), U303.4 (V-); also elsewhere on the board
/Scabi/Clip/scabi-out: J301.1, R320.1, U303.5 (+)
/eq_to_scabi: J302.1, R317.1; also elsewhere on the board
/prefader-out: U303.1, U303.2 (-); also elsewhere on the board
BIAS-IN: R301.1, R305.2; also elsewhere on the board
GND: C301.2, C302.1, C303.1, C304.1, C305.1, C306.2, C307.1, C308.1, C309.2, C310.1, D302.1 (K), D304.2 (A), Q304.1 (E), Q304.3 (C), Q304.5 (B), Q305.4 (E), R305.1, R307.1, R308.1, R310.1, R312.1, R319.1, R324.1, U301.3 (+), U301.5 (+); also elsewhere on the board
unnamed: D301.3, R301.2, R302.1
unnamed: D302.2 (A), Q301.1 (E), R306.2
unnamed: D303.3, R322.2, R323.1
unnamed: D304.1 (K), Q305.3 (C), Q305.5 (B), R326.2, SW302.1 (A)
unnamed: Q301.2 (B), Q301.6 (C), R309.1, SW301.2 (B)
unnamed: Q301.4 (E), Q305.1 (E), R321.1, U303.3 (+)
unnamed: Q301.5 (B), SW301.1 (A)
unnamed: Q302.B, R303.2, U301.7
unnamed: Q302.C, Q303.C, R308.2, U302.1 (Iout)
unnamed: Q302.E, R304.2
unnamed: Q303.B, R307.2, R315.1
unnamed: Q303.E, R316.1
unnamed: Q304.2 (B), R325.2, U301.1
unnamed: Q304.4 (E), R327.2, R329.2
unnamed: Q304.6 (C), R318.2
unnamed: Q305.2 (B), SW302.2 (B)
unnamed: R302.2, R303.1, R313.2, R314.1, U301.6 (-)
unnamed: R310.2, U302.2 (-In)
unnamed: R311.1, R320.2, U302.6 (Vout)
unnamed: R311.2, R312.2, U302.8 (Gain)
unnamed: R317.2, R319.2, U302.3 (+In)
unnamed: R318.1, U302.5 (Iset)
unnamed: R321.2, U303.6 (-), U303.7
unnamed: R323.2, R325.1, R328.2, R329.1, U301.2 (-)
SCALE-IN: R322.1, R324.2; also elsewhere on the board
bias_cv: R313.1; also elsewhere on the board
scale_cv: R328.1; also elsewhere on the board

Notes on the sheet:
Bias section
scale section
SCALE-BIAS
CLIPPER

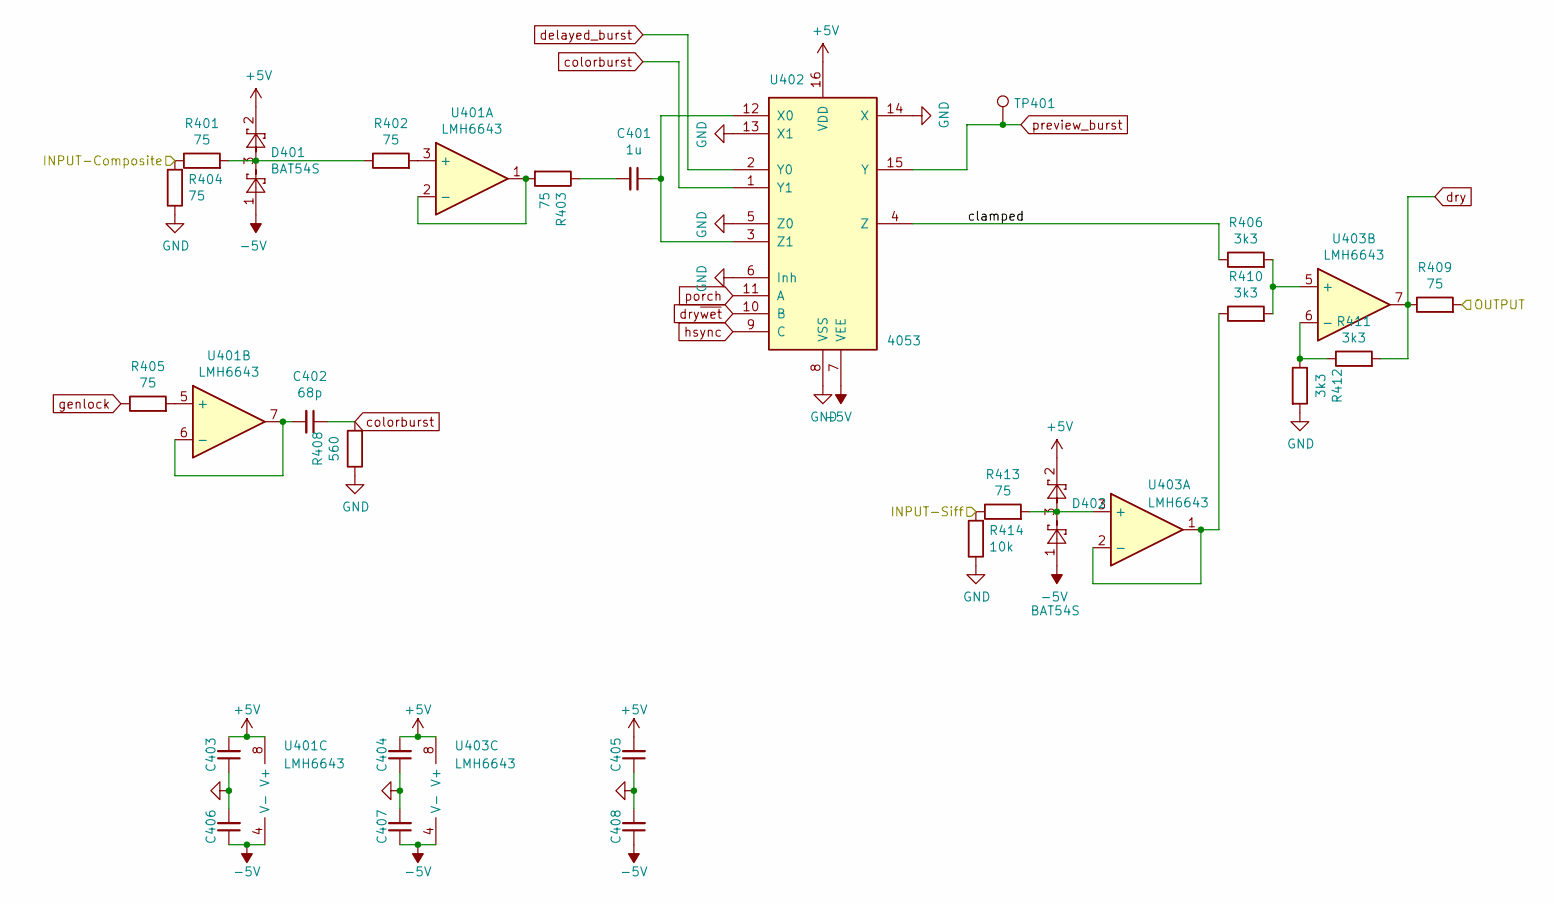
[picture p67: schematic vm013-clamp.sch, vMIX20-Input Conditioning]

Parts:
C401: 1u; C_0603_1608Metric_Pad1.05x0.95mm_HandSolder
C402: 68p; C_1206_3216Metric_Pad1.42x1.75mm_HandSolder
C403, C404, C405, C406, C407, C408: 100n; C_0603_1608Metric_Pad1.05x0.95mm_HandSolder
D401, D402: BAT54S; SOT-23
R401, R402, R403, R404, R405, R409, R413: 75; R_0805_2012Metric_Pad1.15x1.40mm_HandSolder
R406, R410, R411, R412: 3k3; R_0805_2012Metric_Pad1.15x1.40mm_HandSolder
R408: 560; R_0805_2012Metric_Pad1.15x1.40mm_HandSolder
R414: 10k; R_0805_2012Metric_Pad1.15x1.40mm_HandSolder
TP401: TestPoint; Solderpad_1mm
U401, U403: LMH6643; SOIC-8_3.9x4.9mm_P1.27mm
U402: 4053; SOIC-16_3.9x9.9mm_P1.27mm

Connections:
+5V: C403.2, C404.2, C405.2, D401.2, D402.2, U401.8 (V+), U402.16 (VDD), U403.8 (V+); also elsewhere on the board
-5V: C406.1, C407.1, C408.1, D401.1, D402.1, U401.4 (V-), U402.7 (VEE), U403.4 (V-); also elsewhere on the board
/Input-Clamp/INPUT-Composite: R401.1, R404.2; also elsewhere on the board
/Input-Clamp/INPUT-Siff: R413.1, R414.2; also elsewhere on the board
/Input-Clamp/clamped: R406.1, U402.4 (Z)
/clamp_to_eq: R409.2; also elsewhere on the board
GND: C403.1, C404.1, C405.1, C406.2, C407.2, C408.2, R404.1, R408.1, R412.2, R414.1, U402.5 (Z0), U402.6 (Inh), U402.8 (VSS), U402.13 (X1), U402.14 (X); also elsewhere on the board
unnamed: C401.1, U402.3 (Z1), U402.12 (X0)
unnamed: C401.2, R403.1
unnamed: C402.2, U401.6 (-), U401.7
unnamed: D401.3, R401.2, R402.1
unnamed: D402.3, R413.2, U403.3 (+)
unnamed: R402.2, U401.3 (+)
unnamed: R403.2, U401.1, U401.2 (-)
unnamed: R405.2, U401.5 (+)
unnamed: R406.2, R410.2, U403.5 (+)
unnamed: R410.1, U403.1, U403.2 (-)
unnamed: R411.1, R412.1, U403.6 (-)
colorburst: C402.1, R408.2, U402.1 (Y1); also elsewhere on the board
delayed_burst: U402.2 (Y0); also elsewhere on the board
dry: R409.1, R411.2, U403.7; also elsewhere on the board
dry~wet~: U402.10 (B); also elsewhere on the board
genlock: R405.1; also elsewhere on the board
hsync: U402.9 (C); also elsewhere on the board
porch: U402.11 (A); also elsewhere on the board
preview_burst: TP401.1, U402.15 (Y); also elsewhere on the board

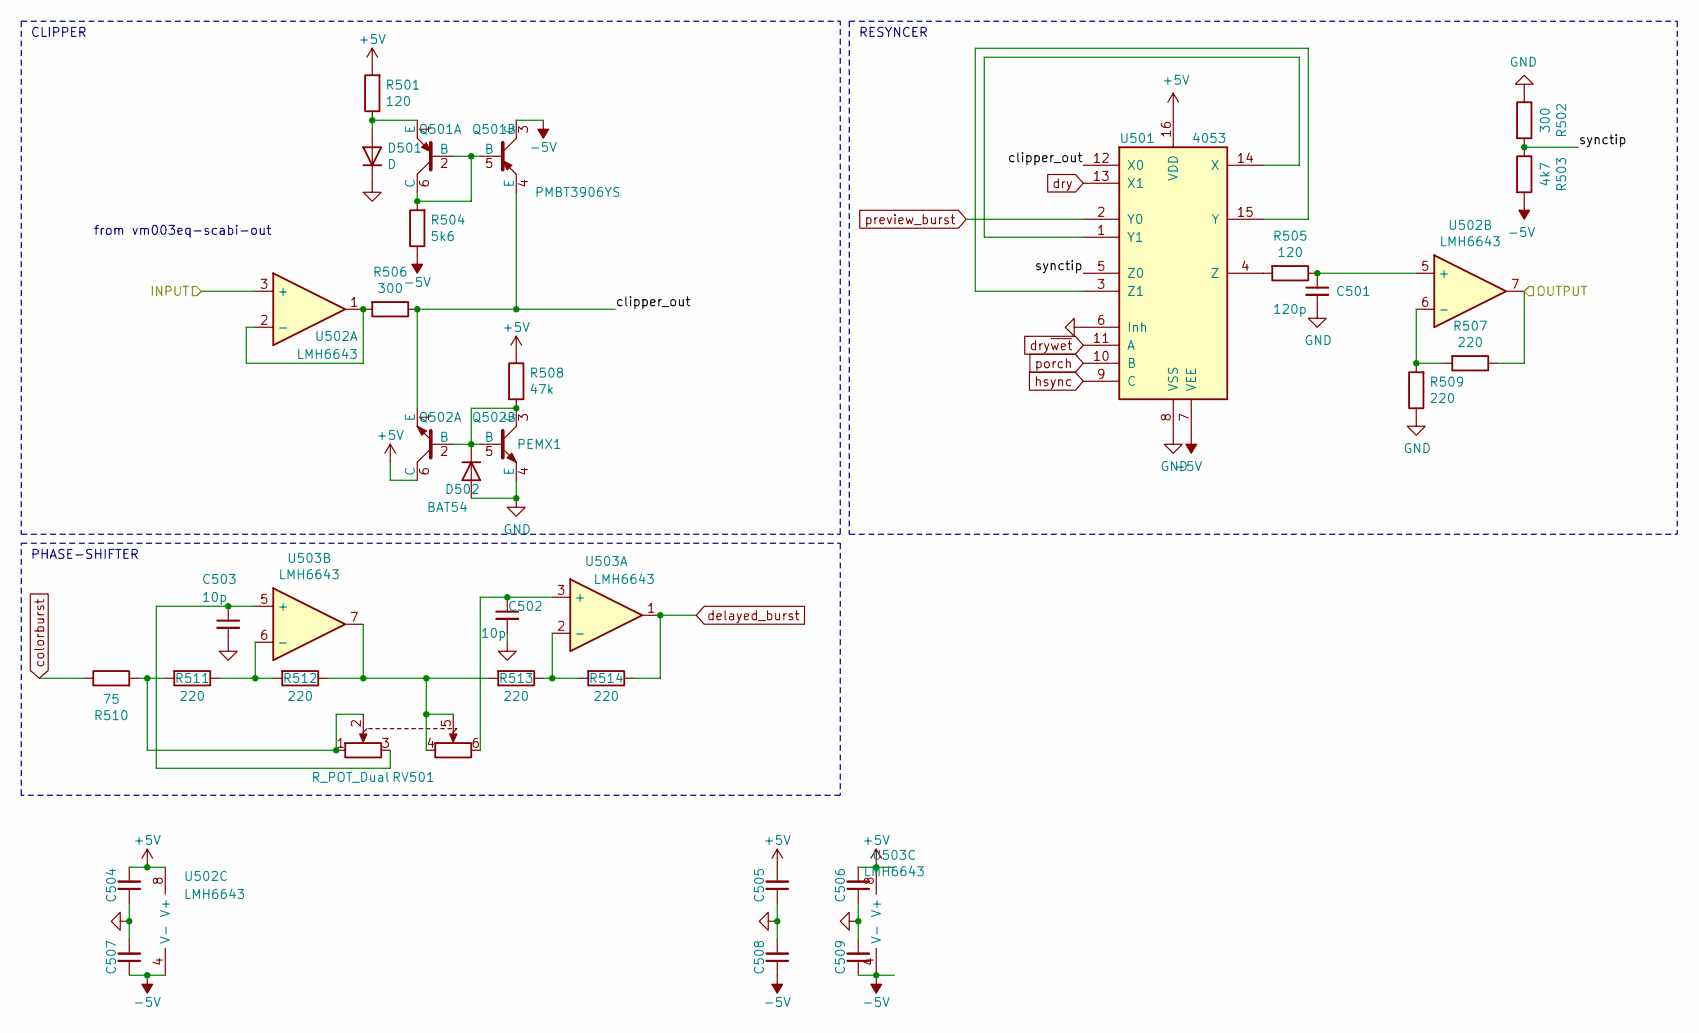
[picture p68: schematic vm013-resync.sch, vMIX20-Resyncer]

Parts:
C501: 120p; C_0805_2012Metric_Pad1.15x1.40mm_HandSolder
C502, C503: 10p; C_0805_2012Metric_Pad1.15x1.40mm_HandSolder
C504, C505, C506, C507, C508, C509: 100n; C_0603_1608Metric_Pad1.05x0.95mm_HandSolder
D501: D; D_MiniMELF
D502: BAT54; D_SOT-23_ANK
Q501: PMBT3906YS; SOT-363_SC-70-6_Handsoldering
Q502: PEMX1; SOT-666
R501, R505: 120; R_0805_2012Metric_Pad1.15x1.40mm_HandSolder
R502, R506: 300; R_0805_2012Metric_Pad1.15x1.40mm_HandSolder
R503: 4k7; R_0805_2012Metric_Pad1.15x1.40mm_HandSolder
R504: 5k6; R_0805_2012Metric_Pad1.15x1.40mm_HandSolder
R507, R509, R511, R512, R513, R514: 220; R_0805_2012Metric_Pad1.15x1.40mm_HandSolder
R508: 47k; R_0805_2012Metric_Pad1.15x1.40mm_HandSolder
R510: 75; R_0805_2012Metric_Pad1.15x1.40mm_HandSolder
RV501: R_POT_Dual; RK12L123
U501: 4053; SOIC-16_3.9x9.9mm_P1.27mm
U502, U503: LMH6643; SOIC-8_3.9x4.9mm_P1.27mm

Connections:
+5V: C504.2, C505.2, C506.2, Q502.6 (C), R501.2, R508.1, U501.16 (VDD), U502.8 (V+), U503.8 (V+); also elsewhere on the board
-5V: C507.1, C508.1, C509.1, Q501.3 (C), R503.2, R504.1, U501.7 (VEE), U502.4 (V-), U503.4 (V-); also elsewhere on the board
/Resyncer/OUTPUT: R507.1, U502.7; also elsewhere on the board
/Resyncer/clipper_out: Q501.4 (E), Q502.1 (E), R506.1, U501.12 (X0)
/Resyncer/synctip: R502.2, R503.1, U501.5 (Z0)
/prefader-out: U502.3 (+); also elsewhere on the board
GND: C501.2, C502.2, C503.2, C504.1, C505.1, C506.1, C507.2, C508.2, C509.2, D501.1 (K), D502.2 (A), Q502.4 (E), R502.1, R509.1, U501.6 (Inh), U501.8 (VSS); also elsewhere on the board
unnamed: C501.1, R505.1, U502.5 (+)
unnamed: C502.1, RV501.6, U503.3 (+)
unnamed: C503.1, RV501.3, U503.5 (+)
unnamed: D501.2 (A), Q501.1 (E), R501.1
unnamed: D502.1 (K), Q502.2 (B), Q502.3 (C), Q502.5 (B), R508.2
unnamed: Q501.2 (B), Q501.5 (B), Q501.6 (C), R504.2
unnamed: R505.2, U501.4 (Z)
unnamed: R506.2, U502.1, U502.2 (-)
unnamed: R507.2, R509.2, U502.6 (-)
unnamed: R510.2, R511.2, RV501.1, RV501.2
unnamed: R511.1, R512.2, U503.6 (-)
unnamed: R512.1, R513.2, RV501.4, RV501.5, U503.7
unnamed: R513.1, R514.2, U503.2 (-)
unnamed: U501.1 (Y1), U501.14 (X)
unnamed: U501.3 (Z1), U501.15 (Y)
colorburst: R510.1; also elsewhere on the board
delayed_burst: R514.1, U503.1; also elsewhere on the board
dry: U501.13 (X1); also elsewhere on the board
dry~wet~: U501.11 (A); also elsewhere on the board
hsync: U501.9 (C); also elsewhere on the board
porch: U501.10 (B); also elsewhere on the board
preview_burst: U501.2 (Y0); also elsewhere on the board

Notes on the sheet:
PHASE-SHIFTER
CLIPPER
RESYNCER
from vm003eq-scabi-out

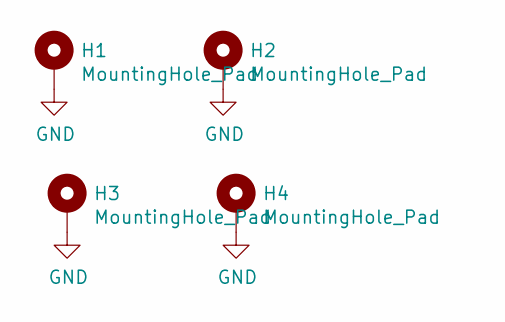
[picture p69: schematic vm013-mechanical.sch]

Parts:
H1, H2, H3, H4: MountingHole_Pad; MountingHole_3.2mm_M3_ISO7380_Pad

Connections:
unnamed: H1.1, H2.1, H3.1, H4.1

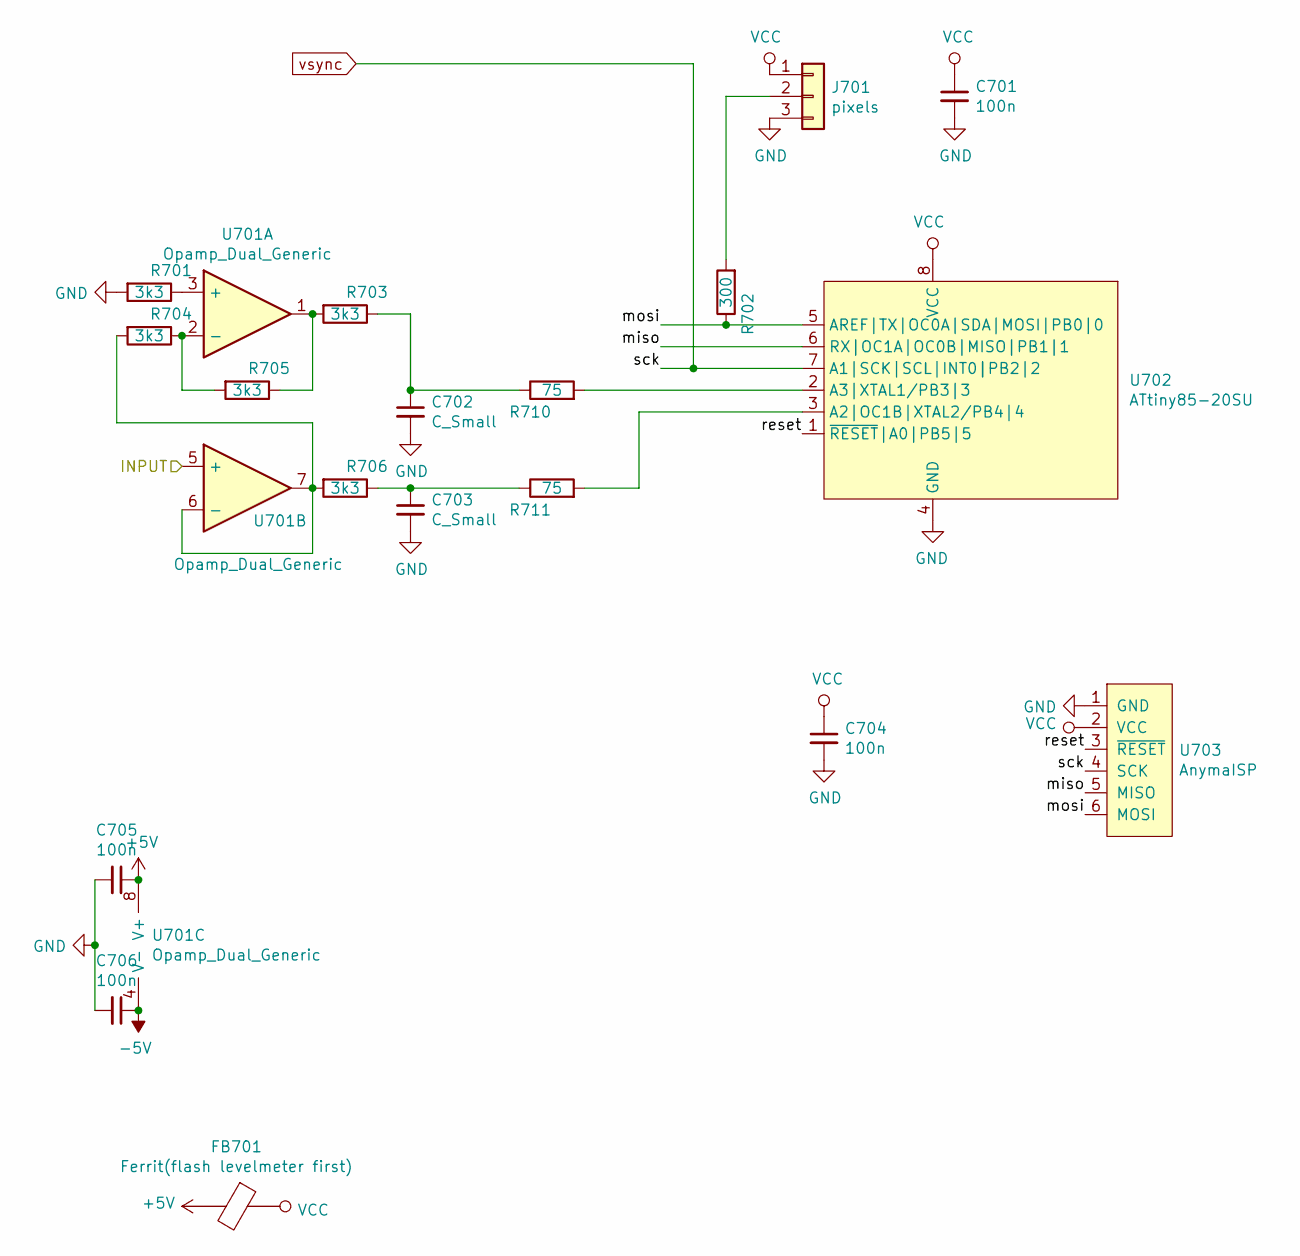
[picture p70: schematic vm013-levelmeter.sch, vMIX20-Levelmeter]

Parts:
C701, C704, C705, C706: 100n; C_0603_1608Metric_Pad1.05x0.95mm_HandSolder
C702, C703: C_Small; C_0603_1608Metric_Pad1.05x0.95mm_HandSolder
FB701: Ferrit(flash levelmeter first); L_0805_2012Metric_Pad1.15x1.40mm_HandSolder
J701: pixels; Molex_KK-254_AE-6410-03A_1x03_P2.54mm_Vertical
R701, R703, R704, R705, R706: 3k3; R_0805_2012Metric_Pad1.15x1.40mm_HandSolder
R702: 300; R_0805_2012Metric_Pad1.15x1.40mm_HandSolder
R710, R711: 75; R_0805_2012Metric_Pad1.15x1.40mm_HandSolder
U701: Opamp_Dual_Generic; SOIC-8_3.9x4.9mm_P1.27mm
U702: ATtiny85-20SU; SOIJ-8_5.3x5.3mm_P1.27mm
U703: AnymaISP; PinHeader_1x06_P2.54mm_Vertical

Connections:
+5V: C705.1, FB701.2, U701.8 (V+); also elsewhere on the board
-5V: C706.1, U701.4 (V-); also elsewhere on the board
/Levelmeter/miso: U702.6 (RX|OC1A|OC0B|MISO|PB1|1), U703.5 (MISO)
/Levelmeter/mosi: R702.1, U702.5 (AREF|TX|OC0A|SDA|MOSI|PB0|0), U703.6 (MOSI)
/Levelmeter/reset: U702.1 (~RESET~|A0|PB5|5), U703.3 (~RESET)
/prefader-out: U701.5 (+); also elsewhere on the board
GND: C701.2, C702.2, C703.2, C704.2, C705.2, C706.2, J701.3, R701.2, U702.4 (GND), U703.1 (GND); also elsewhere on the board
unnamed: C702.1, R703.1, R710.1
unnamed: C703.1, R706.1, R711.1
unnamed: J701.2, R702.2
unnamed: R701.1, U701.3 (+)
unnamed: R703.2, R705.1, U701.1
unnamed: R704.1, R705.2, U701.2 (-)
unnamed: R704.2, R706.2, U701.6 (-), U701.7
unnamed: R710.2, U702.2 (A3|XTAL1/PB3|3)
unnamed: R711.2, U702.3 (A2|OC1B|XTAL2/PB4|4)
VCC: C701.1, C704.1, FB701.1, J701.1, U702.8 (VCC), U703.2 (VCC)
vsync: U702.7 (A1|SCK|SCL|INT0|PB2|2), U703.4 (SCK); also elsewhere on the board

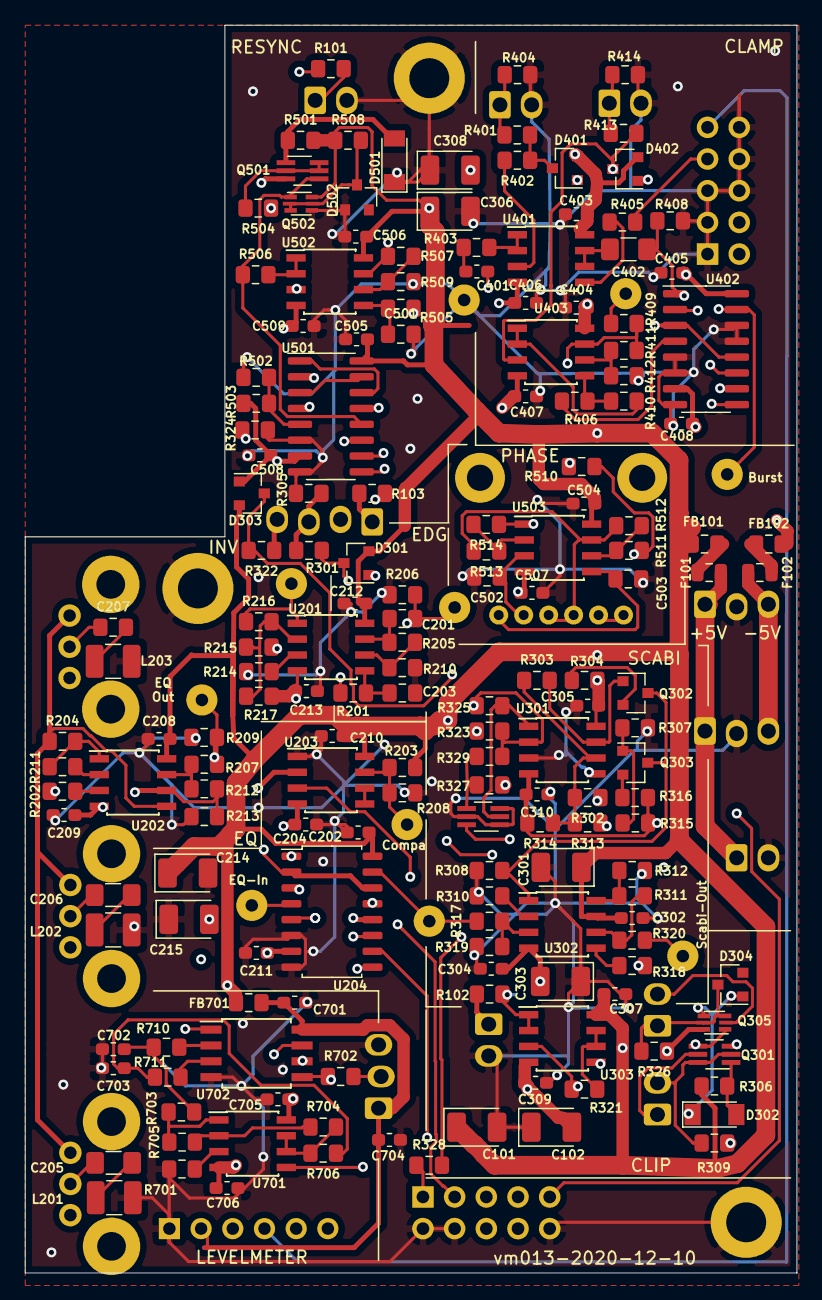
[picture p71: board vm013-analog-section.kicad_pcb from above]

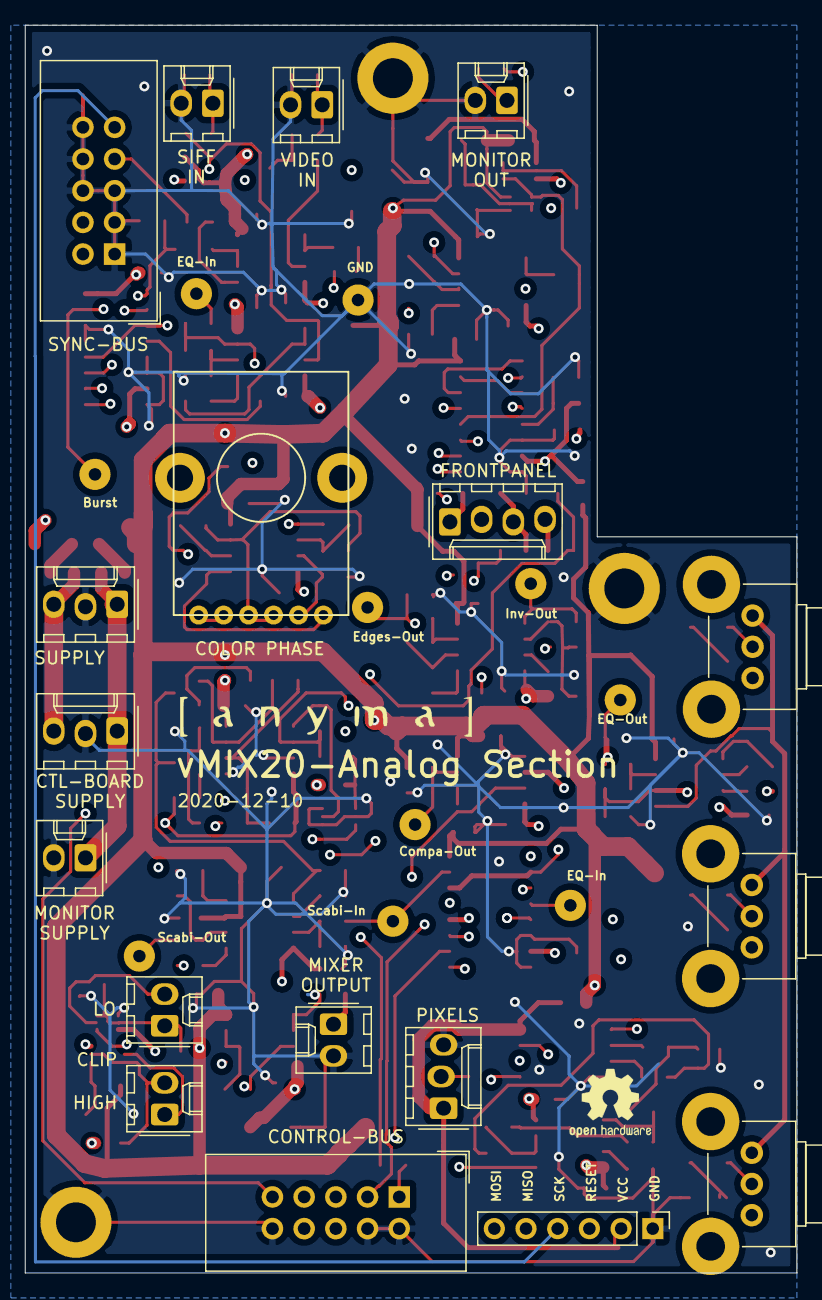
[picture p72: board vm013-analog-section.kicad_pcb from below]

Board: 4 copper layers, 61.8 x 100.0 mm, 205 parts (20 on the bottom side), 124 nets.

Other parts of the board:
H601, H602, H603: MountingHole_Pad; MountingHole_3.2mm_M3_ISO7380_Pad
U601: LOGO; logo_anyma
U602: LOGO; OSHW-Logo2_7.3x6mm_SilkScreen

Their connections:
GND: H601.1, H602.1, H603.1; also elsewhere on the board
