mirdej/vmix/vm005-mix/vm005-mix.kicad_pcb

## KiCad design vm005-mix/vm005-mix.kicad_pcb (2020-12-14)

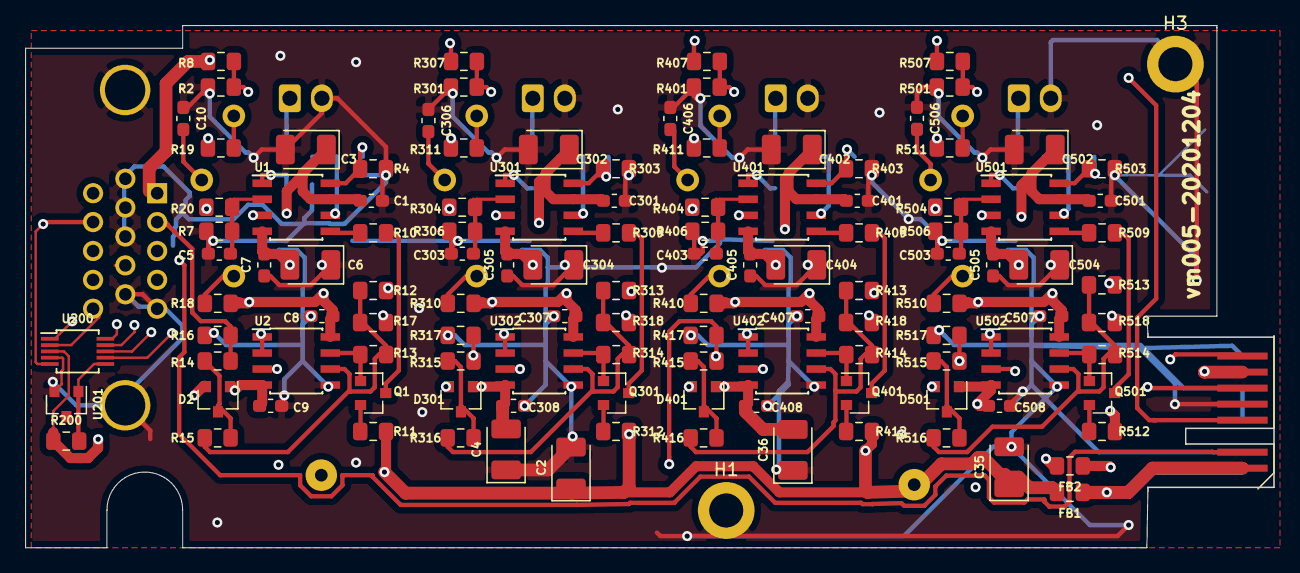
[picture p73: board vm005-mix.kicad_pcb from above]

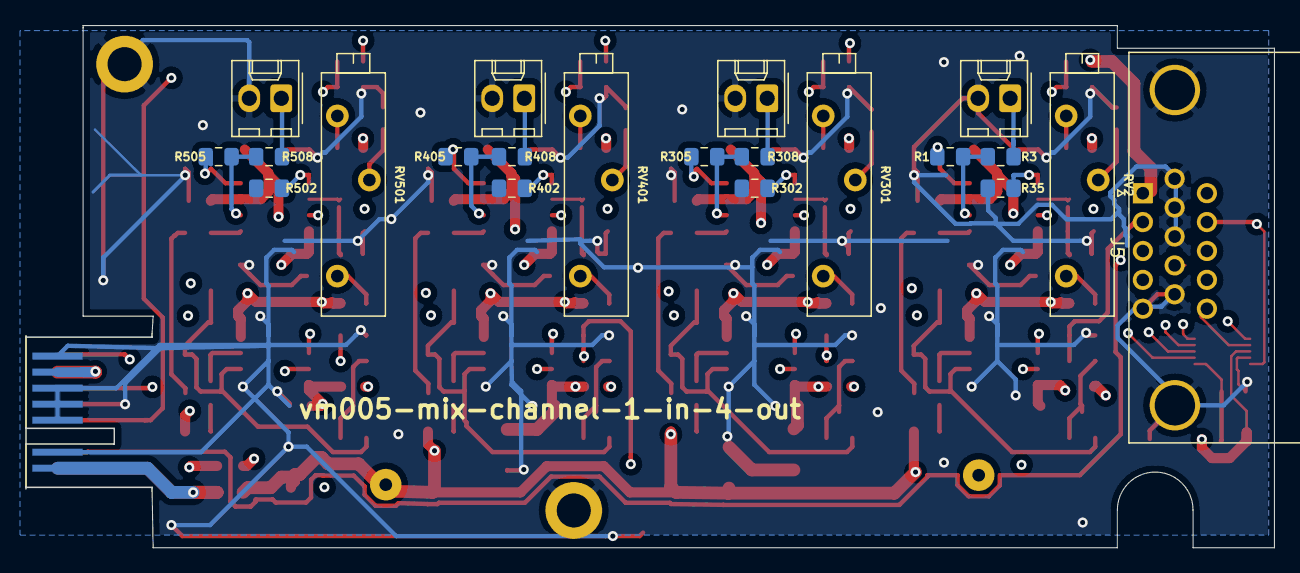
[picture p74: board vm005-mix.kicad_pcb from below]

Board: 4 copper layers, 99.0 x 41.4 mm, 144 parts (21 on the bottom side), 82 nets.

Parts:
C1, C7, C8, C9, C301, C305, C307, C308, C401, C405, C407, C408, C501, C505, C507, C508: 100n; C_0603_1608Metric_Pad1.05x0.95mm_HandSolder
C2, C4, C35, C36: 10u; CP_EIA-3528-21_Kemet-B_Pad1.50x2.35mm_HandSolder
C3, C6, C302, C304, C402, C404, C502, C504: 4u7; CP_EIA-3528-21_Kemet-B_Pad1.50x2.35mm_HandSolder
C5, C10, C303, C306, C403, C406, C503, C506: 1u; C_0603_1608Metric_Pad1.05x0.95mm_HandSolder
D2, D301, D401, D501: BAT54S; SOT-23
FB1, FB2: 330u; L_0805_2012Metric_Pad1.15x1.40mm_HandSolder
G1: LOGO; logo_anyma
H1, H3: MountingHole_Pad; MountingHole_2.7mm_M2.5_ISO7380_Pad
J1: Conn_EDGE; Samtec_MECF-08-0_-L-DV_2x08_P1.27mm_Polarized_Edge
J2, J301, J401, J501: Conn_01x02; Molex_KK-254_AE-6410-02A_1x02_P2.54mm_Vertical
J5: DB15_Female_HighDensity_MountingHoles; DSUB-15-HD_Female_FCI
Q1, Q301, Q401, Q501: PNP; SOT-23_BEC
R1, R35, R302, R305, R402, R405, R502, R505: (560); R_0805_2012Metric_Pad1.15x1.40mm_HandSolder
R2, R10, R301, R309, R401, R409, R501, R509: 1k; R_0805_2012Metric_Pad1.15x1.40mm_HandSolder
R3, R308, R408, R508: (75); R_0805_2012Metric_Pad1.15x1.40mm_HandSolder
R4, R303, R403, R503: 120; R_0805_2012Metric_Pad1.15x1.40mm_HandSolder
R7, R8, R14, R306, R307, R315, R406, R407, R415, R506, R507, R515: 100; R_0805_2012Metric_Pad1.15x1.40mm_HandSolder
R11, R312, R412, R512: 2k2; R_0805_2012Metric_Pad1.15x1.40mm_HandSolder
R12, R15, R313, R316, R413, R416, R513, R516: 12K; R_0805_2012Metric_Pad1.15x1.40mm_HandSolder
R13, R314, R414, R514: 20k; R_0805_2012Metric_Pad1.15x1.40mm_HandSolder
R16, R317, R417, R517: 47k; R_0805_2012Metric_Pad1.15x1.40mm_HandSolder
R17, R318, R418, R518: 22k; R_0805_2012Metric_Pad1.15x1.40mm_HandSolder
R18, R19, R20, R304, R310, R311, R404, R410, R411, R504, R510, R511: 3k; R_0805_2012Metric_Pad1.15x1.40mm_HandSolder
R200: 560; R_0805_2012Metric_Pad1.15x1.40mm_HandSolder
RV2, RV301, RV401, RV501: 500; Potentiometer_Bourns_3006P_Horizontal
TP1, TP2: TestPoint; Solderpad_1mm
U1, U301, U401, U501: LT1228; SOIC-8_3.9x4.9mm_P1.27mm
U2, U302, U402, U502: LMH6643; SOIC-8_3.9x4.9mm_P1.27mm
U200: MAX5741; MSOP-10_3x3mm_P0.5mm
U201: ADR510; SOT-23

Connections:
+5V: C1.2, C2.1, C3.1, C8.1, C35.1, C301.2, C302.1, C307.1, C401.2, C402.1, C407.1, C501.2, C502.1, C507.1, D2.2, D301.2, D401.2, D501.2, FB1.2, R11.2, R18.2, R200.1, R310.2, R312.2, R410.2, R412.2, R510.2, R512.2, TP1.1, U1.7, U2.8, U200.3, U301.7, U302.8, U401.7, U402.8, U501.7, U502.8
-5V: C4.2, C6.2, C7.2, C9.1, C36.2, C304.2, C305.2, C308.1, C404.2, C405.2, C408.1, C504.2, C505.2, C508.1, D2.1, D301.1, D401.1, D501.1, FB2.2, R17.1, R19.1, R311.1, R318.1, R411.1, R418.1, R511.1, R518.1, TP2.1, U1.4, U2.4, U301.4, U302.4, U401.4, U402.4, U501.4, U502.4
/cv_a: J5.2, R14.2, R16.2
/cv_b: J5.3, R315.2, R317.2
/cv_c: J5.13, R415.2, R417.2
/cv_d: J5.14, R515.2, R517.2
/dac_a: R12.2, U200.7
/dac_b: R313.2, U200.8
/dac_c: R413.2, U200.9
/dac_d: R513.2, U200.10
/dac_select: J5.9, U200.1
/input: J5.1, R2.2, R301.2, R401.2, R501.2
/mosi: J5.12, U200.5
/out_a: J1.3, R35.2, U1.1
/out_b: J1.7, R302.2, U301.1
/out_c: J1.11, R402.2, U401.1
/out_d: J1.15, R502.2, U501.1
/sck: J5.15, U200.2
/supply+: FB1.1, J1.1, J1.2
/supply-: FB2.1, J1.13, J1.14
GND: C1.1, C2.2, C3.2, C4.1, C5.1, C6.1, C7.1, C8.2, C9.2, C10.1, C35.2, C36.1, C301.1, C302.2, C303.1, C304.1, C305.1, C306.1, C307.2, C308.2, C401.1, C402.2, C403.1, C404.1, C405.1, C406.1, C407.2, C408.2, C501.1, C502.2, C503.1, C504.1, C505.1, C506.1, C507.2, C508.2, H1.1, H3.1, J1.4, J1.8, J1.9, J1.10, J1.12, J1.16, J2.2, J5.0, J5.5, J5.6, J5.7, J5.8, J5.10, J301.2, J401.2, J501.2, R4.2, R7.1, R8.1, R16.1, R35.1, R302.1, R303.2, R306.1, R307.1, R317.1, R402.1, R403.2, R406.1, R407.1, R417.1, R502.1, R503.2, R506.1, R507.1, R517.1, U2.5, U200.4, U201.2, U302.5, U402.5, U502.5
unnamed: C5.2, R7.2, R20.1, U1.2
unnamed: C10.2, RV2.2, U2.3
unnamed: C303.2, R304.1, R306.2, U301.2
unnamed: C306.2, RV301.2, U302.3
unnamed: C403.2, R404.1, R406.2, U401.2
unnamed: C406.2, RV401.2, U402.3
unnamed: C503.2, R504.1, R506.2, U501.2
unnamed: C506.2, RV501.2, U502.3
unnamed: D2.3, R14.1, R15.2
unnamed: D301.3, R315.1, R316.2
unnamed: D401.3, R415.1, R416.2
unnamed: D501.3, R515.1, R516.2
unnamed: J2.1, R3.2
unnamed: J301.1, R308.2
unnamed: J401.1, R408.2
unnamed: J501.1, R508.2
unnamed: Q1.B, R13.1, U2.7
unnamed: Q1.C, R10.1
unnamed: Q1.E, R11.1
unnamed: Q301.B, R314.1, U302.7
unnamed: Q301.C, R309.1
unnamed: Q301.E, R312.1
unnamed: Q401.B, R414.1, U402.7
unnamed: Q401.C, R409.1
unnamed: Q401.E, R412.1
unnamed: Q501.B, R514.1, U502.7
unnamed: Q501.C, R509.1
unnamed: Q501.E, R512.1
unnamed: R1.1, R3.1, U1.6
unnamed: R1.2, R4.1, U1.8
unnamed: R2.1, R8.2, U1.3
unnamed: R10.2, U1.5
unnamed: R12.1, R13.2, R15.1, R17.2, U2.6
unnamed: R18.1, RV2.1
unnamed: R19.2, RV2.3
unnamed: R20.2, U2.1, U2.2
unnamed: R200.2, U200.6, U201.1
unnamed: R301.1, R307.2, U301.3
unnamed: R303.1, R305.2, U301.8
unnamed: R304.2, U302.1, U302.2
unnamed: R305.1, R308.1, U301.6
unnamed: R309.2, U301.5
unnamed: R310.1, RV301.1
unnamed: R311.2, RV301.3
unnamed: R313.1, R314.2, R316.1, R318.2, U302.6
unnamed: R401.1, R407.2, U401.3
unnamed: R403.1, R405.2, U401.8
unnamed: R404.2, U402.1, U402.2
unnamed: R405.1, R408.1, U401.6
unnamed: R409.2, U401.5
unnamed: R410.1, RV401.1
unnamed: R411.2, RV401.3
unnamed: R413.1, R414.2, R416.1, R418.2, U402.6
unnamed: R501.1, R507.2, U501.3
unnamed: R503.1, R505.2, U501.8
unnamed: R504.2, U502.1, U502.2
unnamed: R505.1, R508.1, U501.6
unnamed: R509.2, U501.5
unnamed: R510.1, RV501.1
unnamed: R511.2, RV501.3
unnamed: R513.1, R514.2, R516.1, R518.2, U502.6
