mirdej/vmix/vm009-cpu/vm009-cpu.kicad_pcb

## KiCad design vm009-cpu/vm009-cpu.kicad_pcb (2020-12-03)

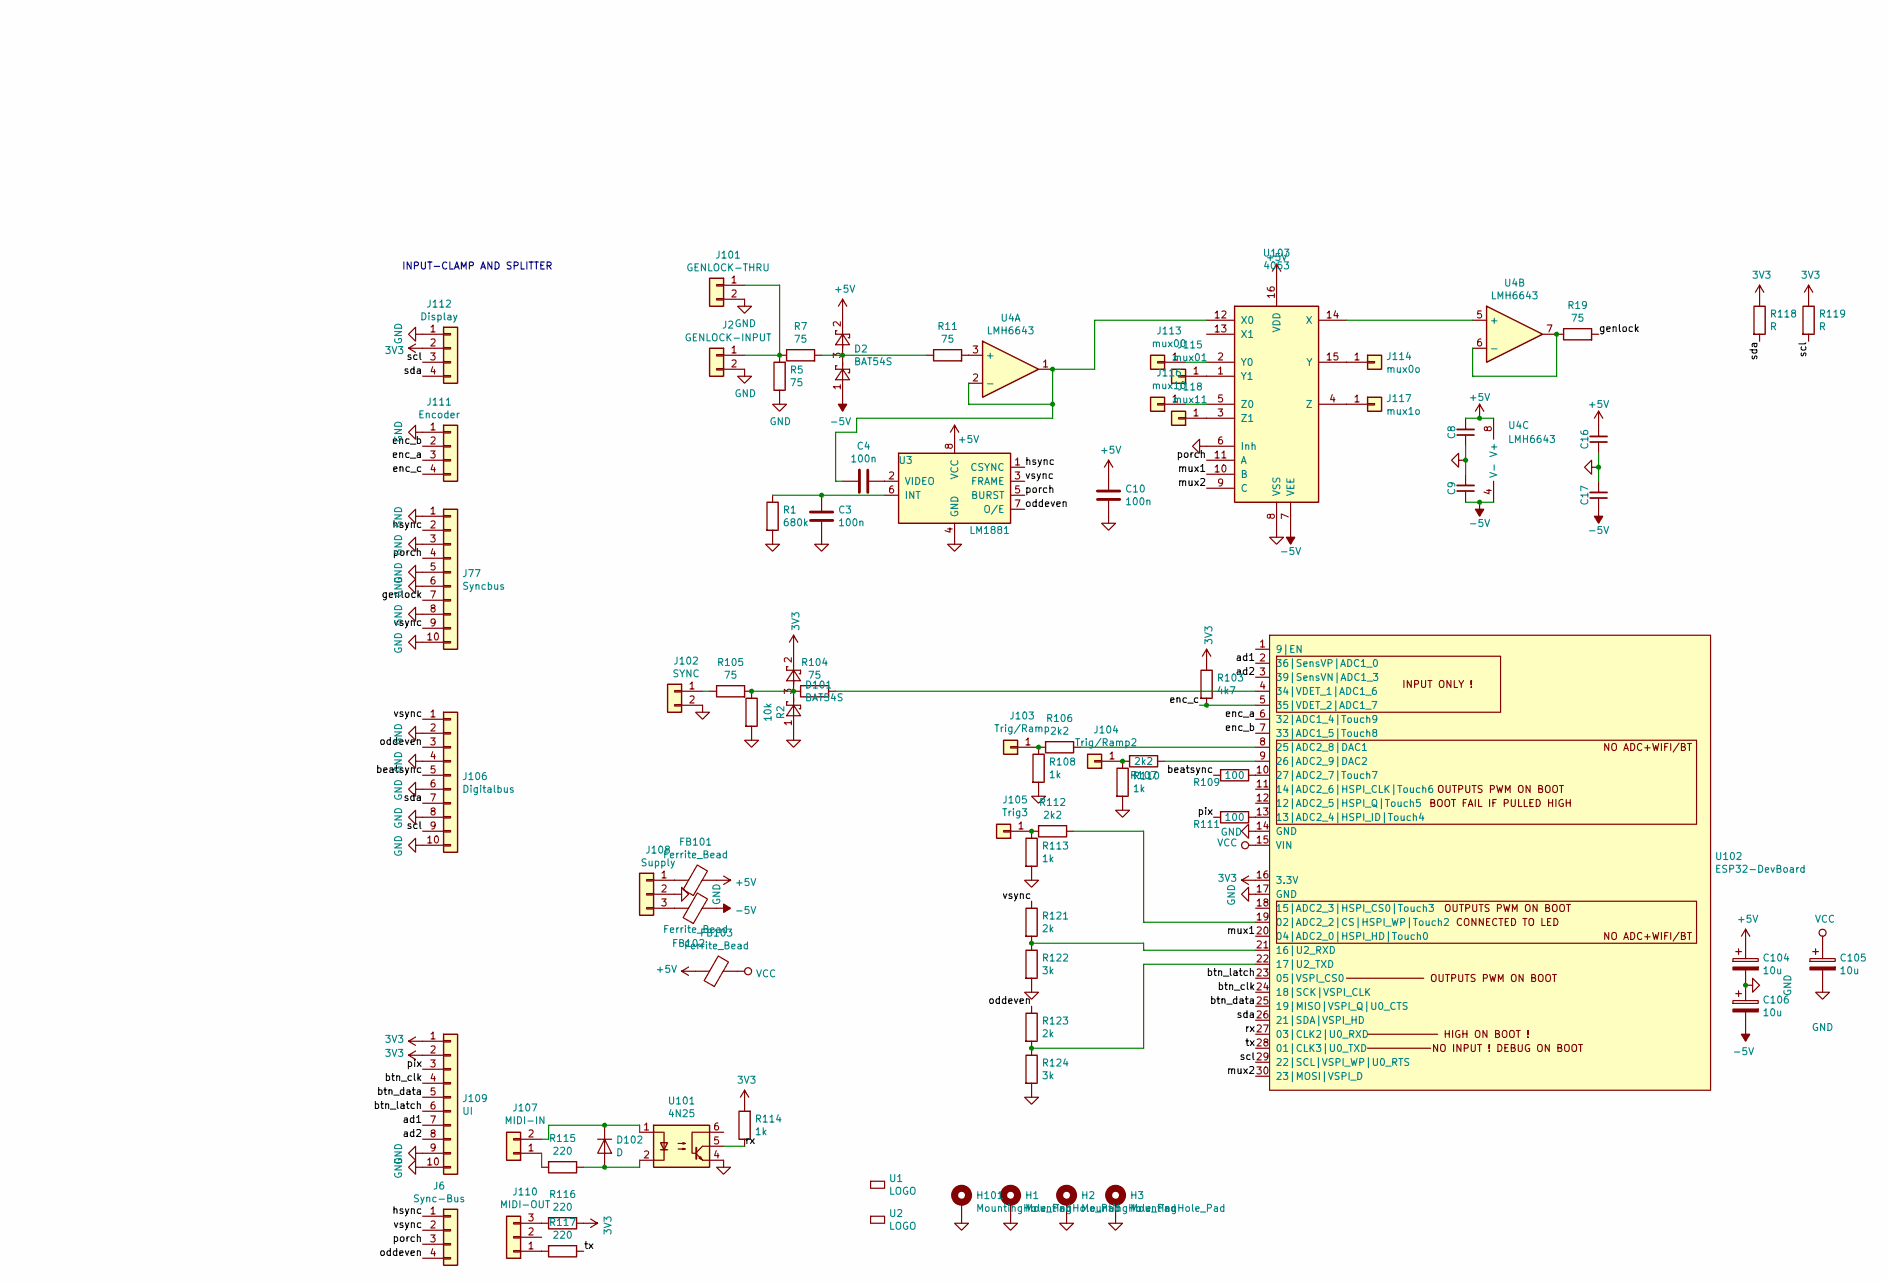
[picture p75: schematic vm009-cpu.sch, part in row 2, column 2]

Parts:
C3, C4, C8, C9, C10, C16, C17: 100n; C_0603_1608Metric_Pad1.05x0.95mm_HandSolder
C104, C105, C106: 10u; CP_EIA-3528-21_Kemet-B_Pad1.50x2.35mm_HandSolder
D2, D101: BAT54S; SOT-23
D102: D; D_MiniMELF_Handsoldering
FB101, FB102, FB103: Ferrite_Bead; L_0805_2012Metric_Pad1.15x1.40mm_HandSolder
H1, H2, H3, H101: MountingHole_Pad; MountingHole_2.7mm_M2.5_ISO7380_Pad
J2: GENLOCK-INPUT; Molex_KK-254_AE-6410-02A_1x02_P2.54mm_Vertical
J6: Sync-Bus; Molex_KK-254_AE-6410-04A_1x04_P2.54mm_Vertical
J77: Syncbus; IDC-Header_2x05_P2.54mm_Vertical
J101: GENLOCK-THRU; Molex_KK-254_AE-6410-02A_1x02_P2.54mm_Vertical
J102: SYNC; Molex_KK-254_AE-6410-02A_1x02_P2.54mm_Vertical
J103: Trig/Ramp; Solderpad_1mm
J104: Trig/Ramp2; Solderpad_1mm
J105: Trig3; Solderpad_1mm
J106: Digitalbus; IDC-Header_2x05_P2.54mm_Vertical
J107: MIDI-IN; Molex_KK-254_AE-6410-02A_1x02_P2.54mm_Vertical
J108: Supply; Molex_KK-254_AE-6410-03A_1x03_P2.54mm_Vertical
J109: UI; IDC-Header_2x05_P2.54mm_Vertical
J110: MIDI-OUT; Molex_KK-254_AE-6410-03A_1x03_P2.54mm_Vertical
J111: Encoder; Molex_KK-254_AE-6410-04A_1x04_P2.54mm_Vertical
J112: Display; Molex_KK-254_AE-6410-04A_1x04_P2.54mm_Vertical
J113: mux00; Solderpad_1mm
J114: mux0o; Solderpad_1mm
J115: mux01; Solderpad_1mm
J116: mux10; Solderpad_1mm
J117: mux1o; Solderpad_1mm
J118: mux11; Solderpad_1mm
R1: 680k; R_0805_2012Metric_Pad1.15x1.40mm_HandSolder
R2: 10k; R_0805_2012Metric_Pad1.15x1.40mm_HandSolder
R5, R7, R11, R19, R104, R105: 75; R_0805_2012Metric_Pad1.15x1.40mm_HandSolder
R103: 4k7; R_0805_2012Metric_Pad1.15x1.40mm_HandSolder
R106, R107, R112: 2k2; R_0805_2012Metric_Pad1.15x1.40mm_HandSolder
R108, R110, R113, R114: 1k; R_0805_2012Metric_Pad1.15x1.40mm_HandSolder
R109, R111: 100; R_0805_2012Metric_Pad1.15x1.40mm_HandSolder
R115, R116, R117: 220; R_0805_2012Metric_Pad1.15x1.40mm_HandSolder
R118, R119: R; R_0805_2012Metric_Pad1.15x1.40mm_HandSolder
R121, R123: 2k; R_0805_2012Metric_Pad1.15x1.40mm_HandSolder
R122, R124: 3k; R_0805_2012Metric_Pad1.15x1.40mm_HandSolder
U1: LOGO; logo_anyma
U2: LOGO; OSHW-Logo2_7.3x6mm_SilkScreen
U3: LM1881; SOIC-8_3.9x4.9mm_P1.27mm
U4: LMH6643; SOIC-8_3.9x4.9mm_P1.27mm
U101: 4N25; DIP-6_W8.89mm_SMDSocket_LongPads
U102: ESP32-DevBoard; ESP32_Devboard
U103: 4053; SOIC-16_3.9x9.9mm_P1.27mm

Connections:
3V3: D101.2, J109.1, J109.2, J112.2, R103.1, R114.2, R116.1, R118.1, R119.1, U102.16 (3.3V)
+5V: C8.2, C10.1, C16.2, C104.1, D2.2, FB101.2, FB103.1, U3.8 (VCC), U4.8 (V+), U103.16 (VDD)
-5V: C9.1, C17.1, C106.2, D2.1, FB102.2, U4.4 (V-), U103.7 (VEE)
/ad1: J109.7, U102.2 (36|SensVP|ADC1_0)
/ad2: J109.8, U102.3 (39|SensVN|ADC1_3)
/beatsync: J106.5, R109.2
/btn_clk: J109.4, U102.24 (18|SCK|VSPI_CLK)
/btn_data: J109.5, U102.25 (19|MISO|VSPI_Q|U0_CTS)
/btn_latch: J109.6, U102.23 (05|VSPI_CS0)
/enc_a: J111.3, U102.6 (32|ADC1_4|Touch9)
/enc_b: J111.2, U102.7 (33|ADC1_5|Touch8)
/enc_c: J111.4, R103.2, U102.5 (35|VDET_2|ADC1_7)
/genlock: J77.7, R19.2
/hsync: J6.1, J77.2, U3.1 (CSYNC)
/mux1: U102.20 (04|ADC2_0|HSPI_HD|Touch0), U103.10 (B)
/mux2: U102.30 (23|MOSI|VSPI_D), U103.9 (C)
/oddeven: J6.4, J106.3, R123.1, U3.7 (O/E)
/pix: J109.3, R111.2
/porch: J6.3, J77.4, U3.5 (BURST), U103.11 (A)
/rx: R114.1, U101.5, U102.27 (03|CLK2|U0_RXD)
/scl: J106.9, J112.3, R119.2, U102.29 (22|SCL|VSPI_WP|U0_RTS)
/sda: J106.7, J112.4, R118.2, U102.26 (21|SDA|VSPI_HD)
/tx: R117.1, U102.28 (01|CLK3|U0_TXD)
/vsync: J6.2, J77.9, J106.1, R121.1, U3.3 (FRAME)
GND: C3.2, C8.1, C9.2, C10.2, C16.1, C17.2, C104.2, C105.2, C106.1, D101.1, H1.1, H2.1, H3.1, H101.1, J2.2, J77.1, J77.3, J77.5, J77.6, J77.8, J77.10, J101.2, J102.2, J106.2, J106.4, J106.6, J106.8, J106.10, J108.2, J109.9, J109.10, J111.1, J112.1, R1.2, R2.2, R5.1, R108.2, R110.2, R113.2, R122.2, R124.2, U3.4 (GND), U101.4, U102.14 (GND), U102.17 (GND), U103.6 (Inh), U103.8 (VSS)
unnamed: C3.1, R1.1, U3.6 (INT)
unnamed: C4.1, U3.2 (VIDEO)
unnamed: C4.2, U4.1, U4.2 (-), U103.12 (X0)
unnamed: D2.3, R7.2, R11.1
unnamed: D101.3, R2.1, R104.1, R105.2
unnamed: D102.1 (K), J107.2, U101.1
unnamed: D102.2 (A), R115.1, U101.2
unnamed: FB101.1, J108.1
unnamed: FB102.1, J108.3
unnamed: J2.1, J101.1, R5.2, R7.1
unnamed: J102.1, R105.1
unnamed: J103.1, R106.2, R108.1
unnamed: J104.1, R107.2, R110.1
unnamed: J105.1, R112.2, R113.1
unnamed: J107.1, R115.2
unnamed: J110.1, R117.2
unnamed: J110.3, R116.2
unnamed: J113.1, U103.2 (Y0)
unnamed: J114.1, U103.15 (Y)
unnamed: J115.1, U103.1 (Y1)
unnamed: J116.1, U103.5 (Z0)
unnamed: J117.1, U103.4 (Z)
unnamed: J118.1, U103.3 (Z1)
unnamed: R11.2, U4.3 (+)
unnamed: R19.1, U4.6 (-), U4.7
unnamed: R104.2, U102.4 (34|VDET_1|ADC1_6)
unnamed: R106.1, U102.8 (25|ADC2_8|DAC1)
unnamed: R107.1, U102.9 (26|ADC2_9|DAC2)
unnamed: R109.1, U102.10 (27|ADC2_7|Touch7)
unnamed: R111.1, U102.13 (13|ADC2_4|HSPI_ID|Touch4)
unnamed: R112.1, U102.19 (02|ADC2_2|CS|HSPI_WP|Touch2)
unnamed: R121.2, R122.1, U102.21 (16|U2_RXD)
unnamed: R123.2, R124.1, U102.22 (17|U2_TXD)
unnamed: U4.5 (+), U103.14 (X)
VCC: C105.1, FB103.2, U102.15 (VIN)

Notes on the sheet:
INPUT-CLAMP AND SPLITTER

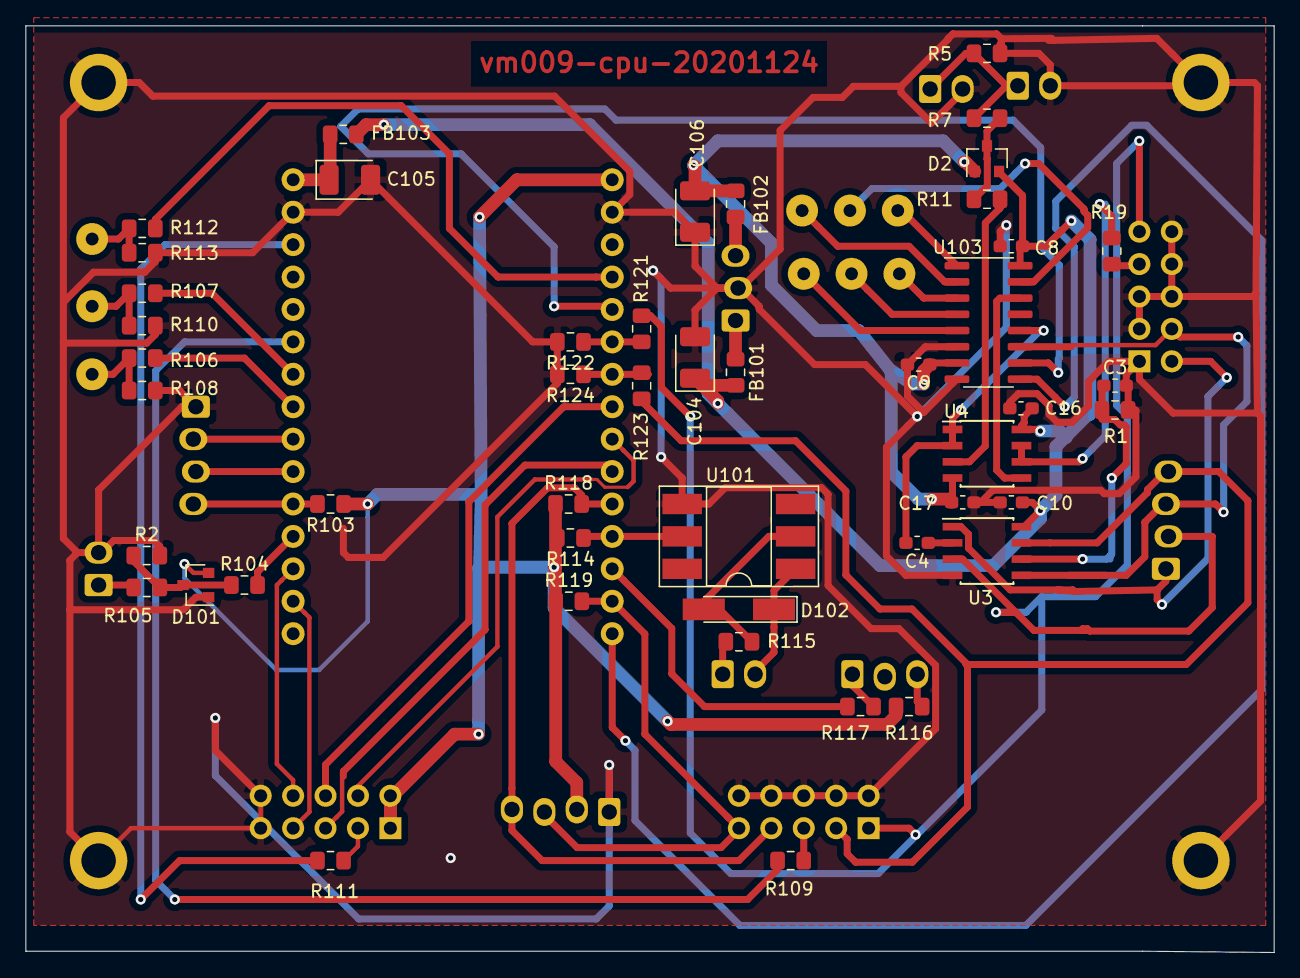
[picture p76: board vm009-cpu.kicad_pcb from above]

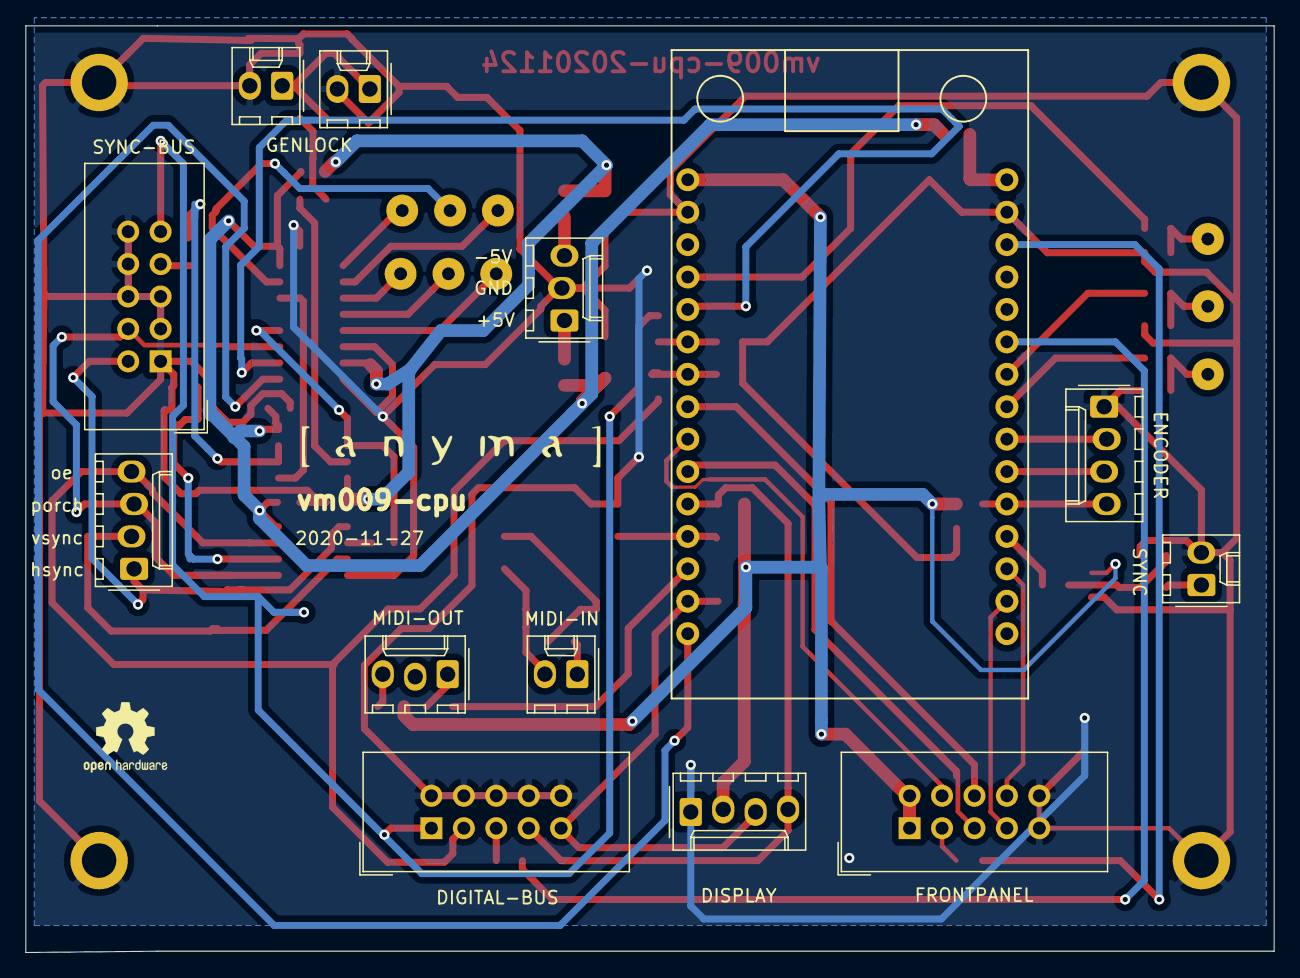
[picture p77: board vm009-cpu.kicad_pcb from below]

Board: 2 copper layers, 97.8 x 72.6 mm, 75 parts (15 on the bottom side), 60 nets.
