mirdej/vmix/vm008-splitter/vm008-splitter.kicad_pcb

## KiCad design vm008-splitter/vm008-splitter.kicad_pcb (2020-11-30)

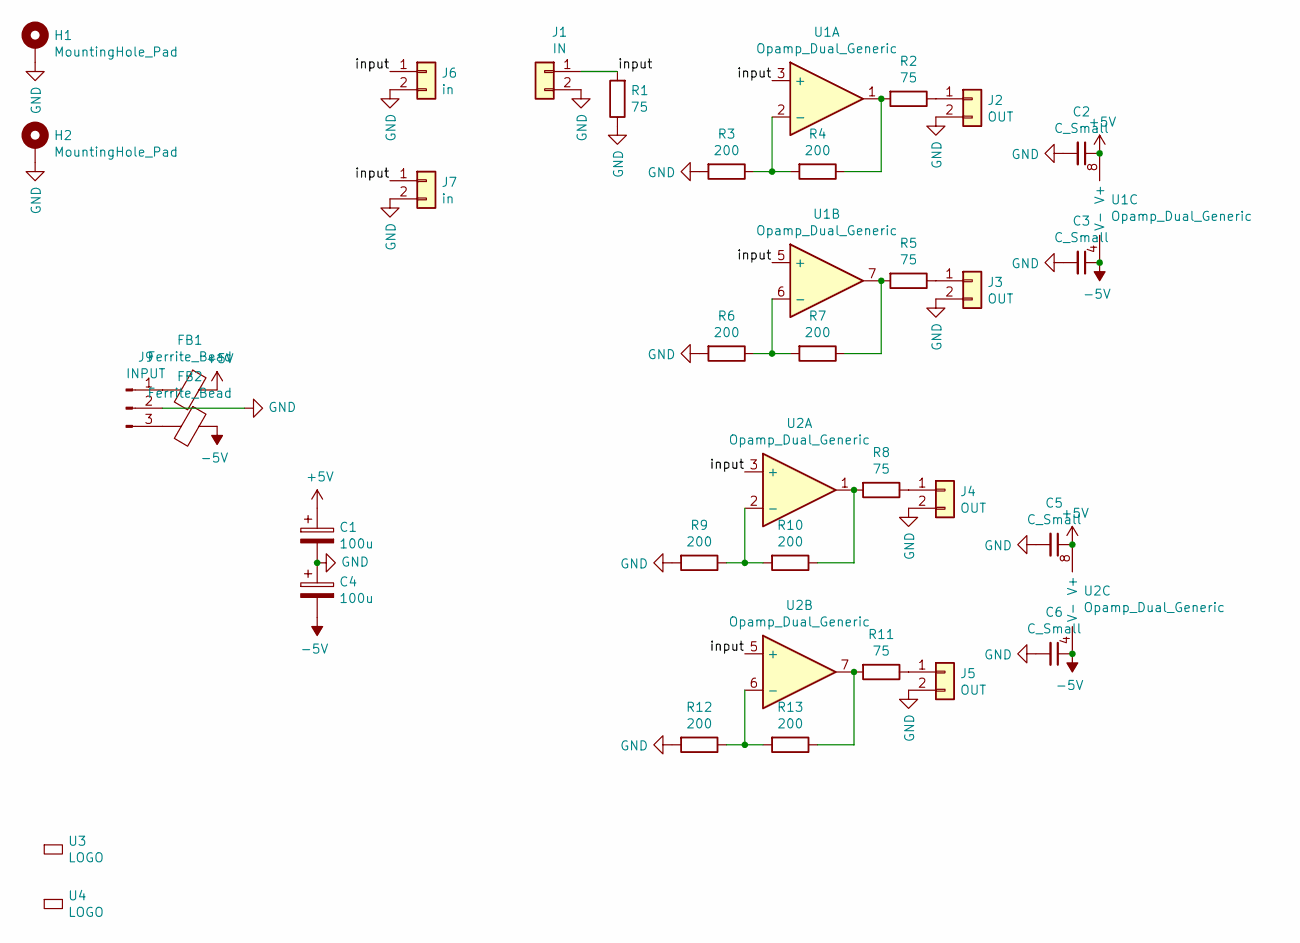
[picture p78: schematic vm008-splitter.sch]

Parts:
C1, C4: 100u; CP_EIA-3528-21_Kemet-B_Pad1.50x2.35mm_HandSolder
C2, C3, C5, C6: C_Small; C_0603_1608Metric_Pad1.05x0.95mm_HandSolder
FB1, FB2: Ferrite_Bead; L_1206_3216Metric_Pad1.42x1.75mm_HandSolder
H1, H2: MountingHole_Pad; MountingHole_3.2mm_M3_ISO7380_Pad
J1: IN; BNC_TEConnectivity_1478204_Vertical
J2, J3, J4, J5: OUT; BNC_TEConnectivity_1478204_Vertical
J6, J7: in; smd-2pin
J9: INPUT; smd-3pin
R1, R2, R5, R8, R11: 75; R_0805_2012Metric_Pad1.15x1.40mm_HandSolder
R3, R4, R6, R7, R9, R10, R12, R13: 200; R_0805_2012Metric_Pad1.15x1.40mm_HandSolder
U1, U2: Opamp_Dual_Generic; SOIC-8_3.9x4.9mm_P1.27mm
U3, U4: LOGO; logo_anyma

Connections:
+5V: C1.1, C2.1, C5.1, FB1.1, U1.8 (V+), U2.8 (V+)
-5V: C3.1, C4.2, C6.1, FB2.1, U1.4 (V-), U2.4 (V-)
/input: J1.1, J6.1, J7.1, R1.2, U1.3 (+), U1.5 (+), U2.3 (+), U2.5 (+)
GND: C1.2, C2.2, C3.2, C4.1, C5.2, C6.2, H1.1, H2.1, J1.2, J2.2, J3.2, J4.2, J5.2, J6.2, J7.2, J9.2, R1.1, R3.2, R6.2, R9.2, R12.2
unnamed: FB1.2, J9.1
unnamed: FB2.2, J9.3
unnamed: J2.1, R2.1
unnamed: J3.1, R5.1
unnamed: J4.1, R8.1
unnamed: J5.1, R11.1
unnamed: R2.2, R4.1, U1.1
unnamed: R3.1, R4.2, U1.2 (-)
unnamed: R5.2, R7.1, U1.7
unnamed: R6.1, R7.2, U1.6 (-)
unnamed: R8.2, R10.1, U2.1
unnamed: R9.1, R10.2, U2.2 (-)
unnamed: R11.2, R13.1, U2.7
unnamed: R12.1, R13.2, U2.6 (-)

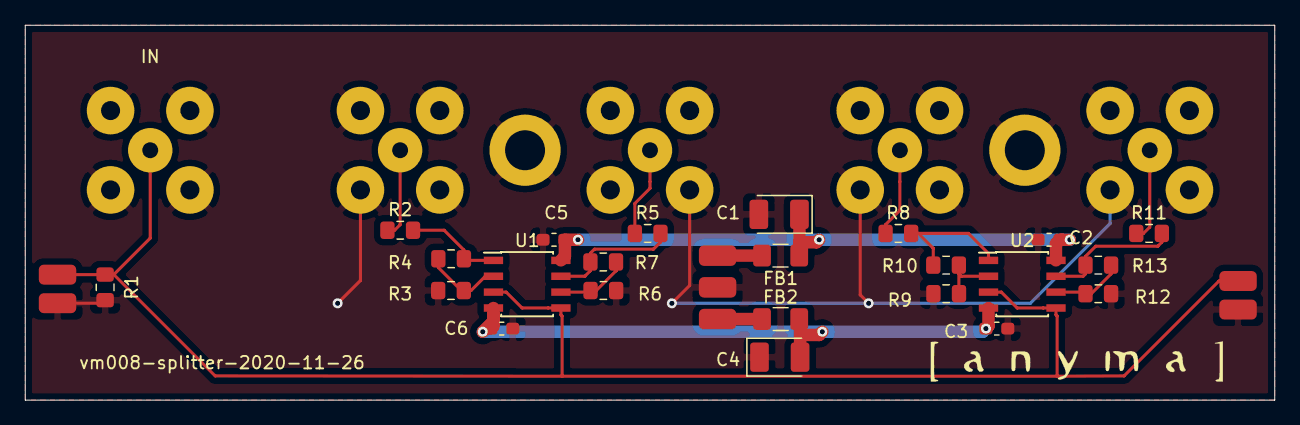
[picture p79: board vm008-splitter.kicad_pcb from above]

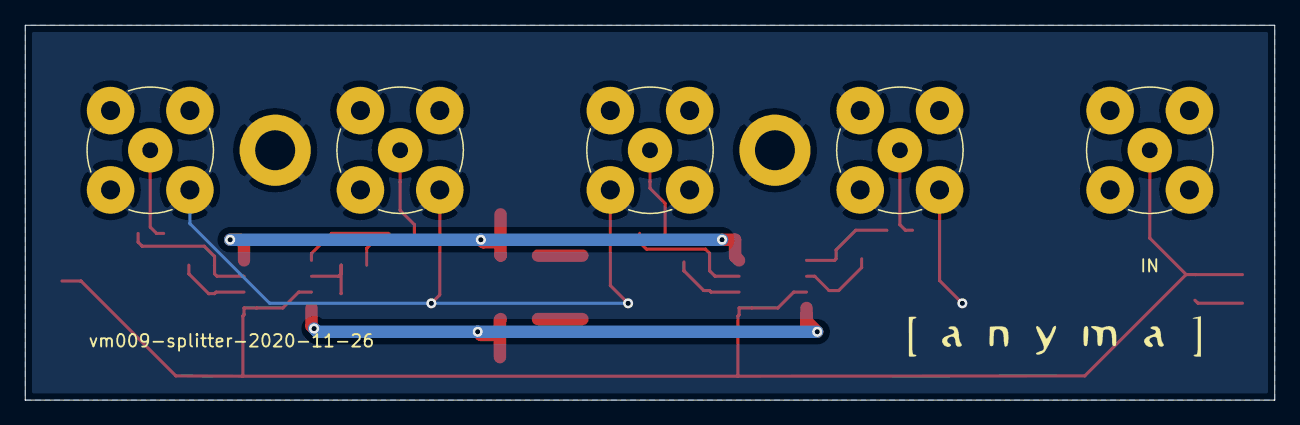
[picture p80: board vm008-splitter.kicad_pcb from below]

Board: 2 copper layers, 100.0 x 30.0 mm, 35 parts (6 on the bottom side), 18 nets.
