mirdej/vmix/vm001-input/vm001-input.kicad_pcb

## KiCad design vm001-input/vm001-input.kicad_pcb (2020-11-13)

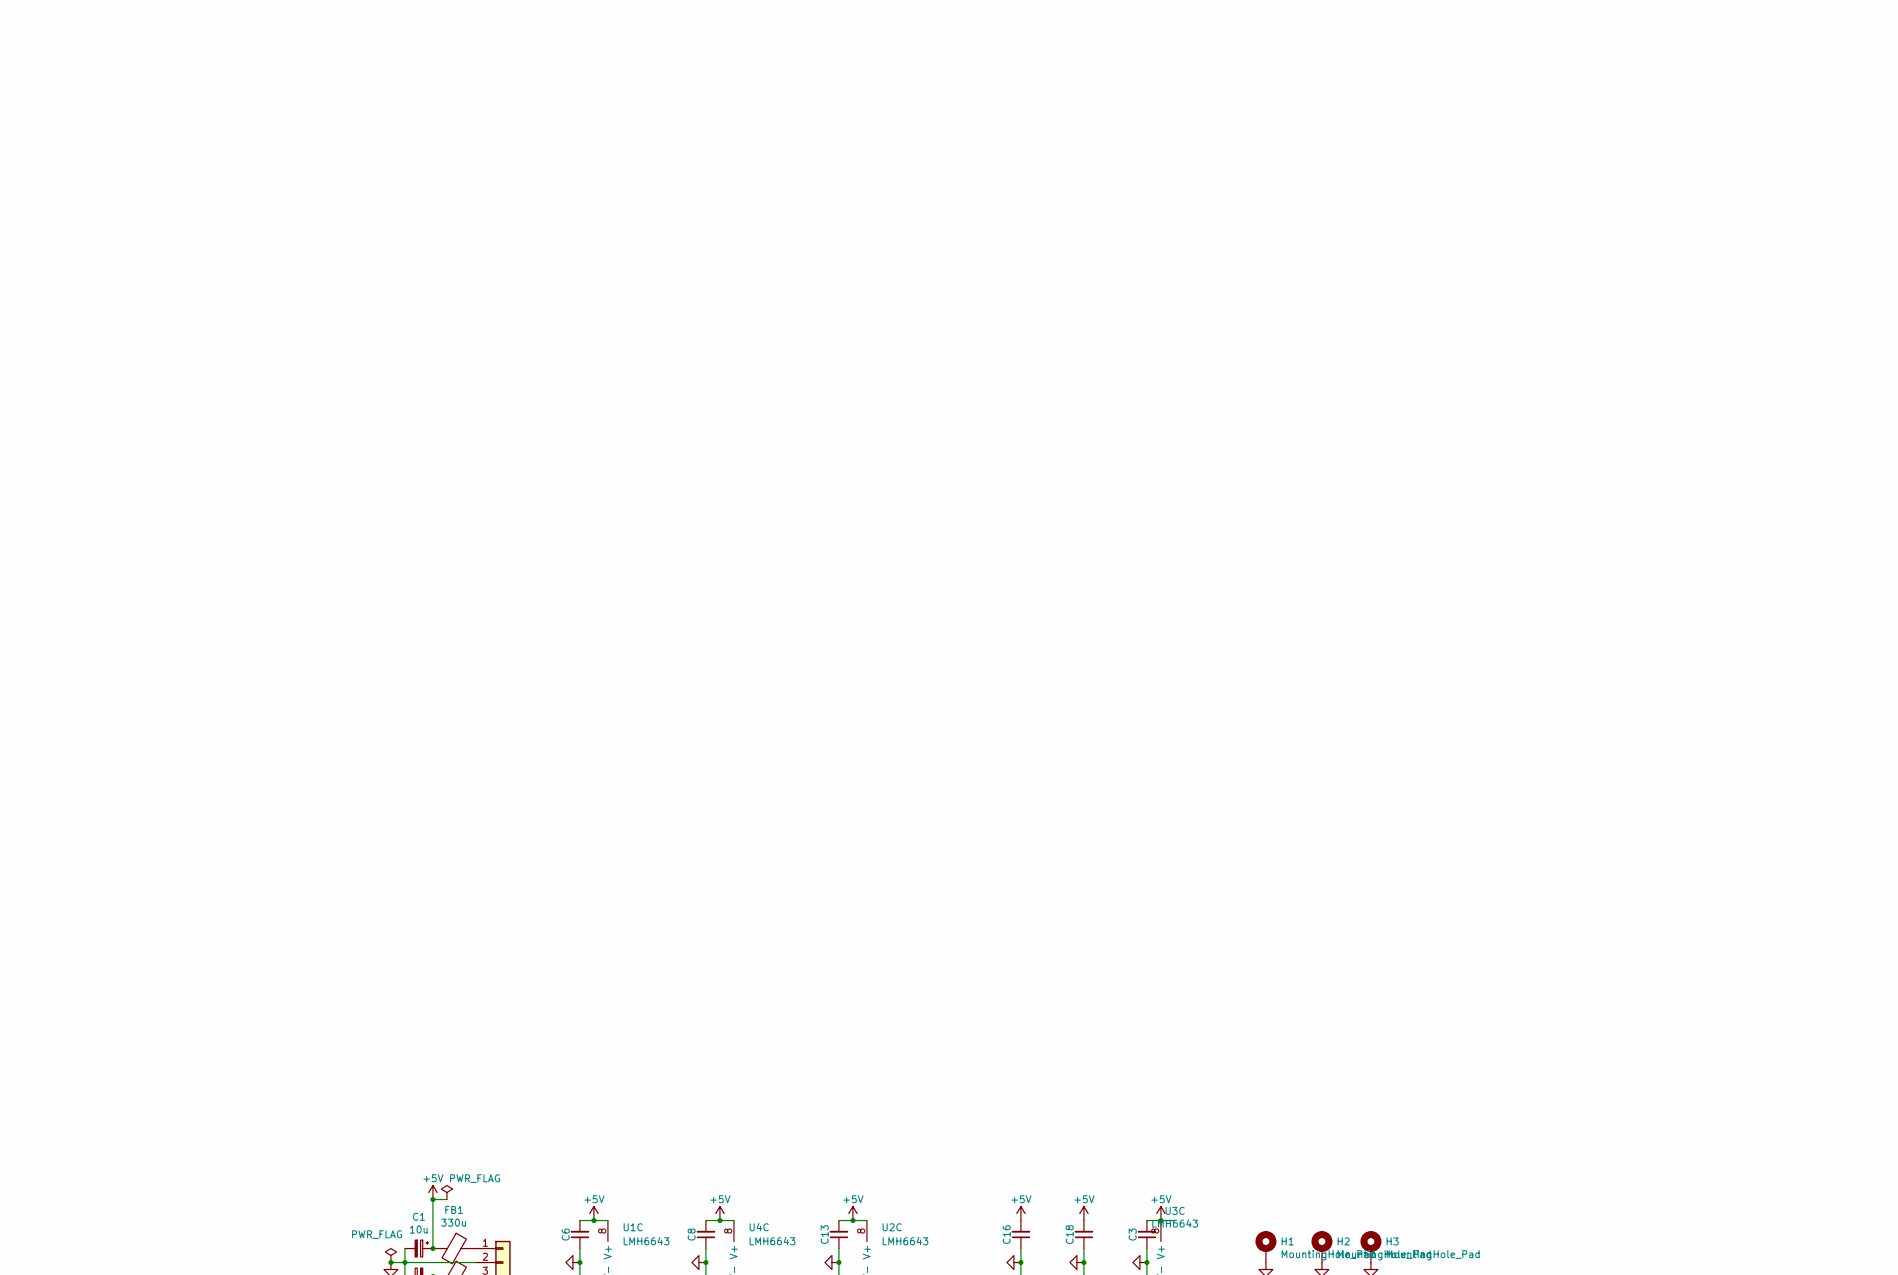
[picture p81: schematic vm001-input.sch, vm001-VMIX20 INPUT AND RESYNCER SECTION, part in row 1, column 2]

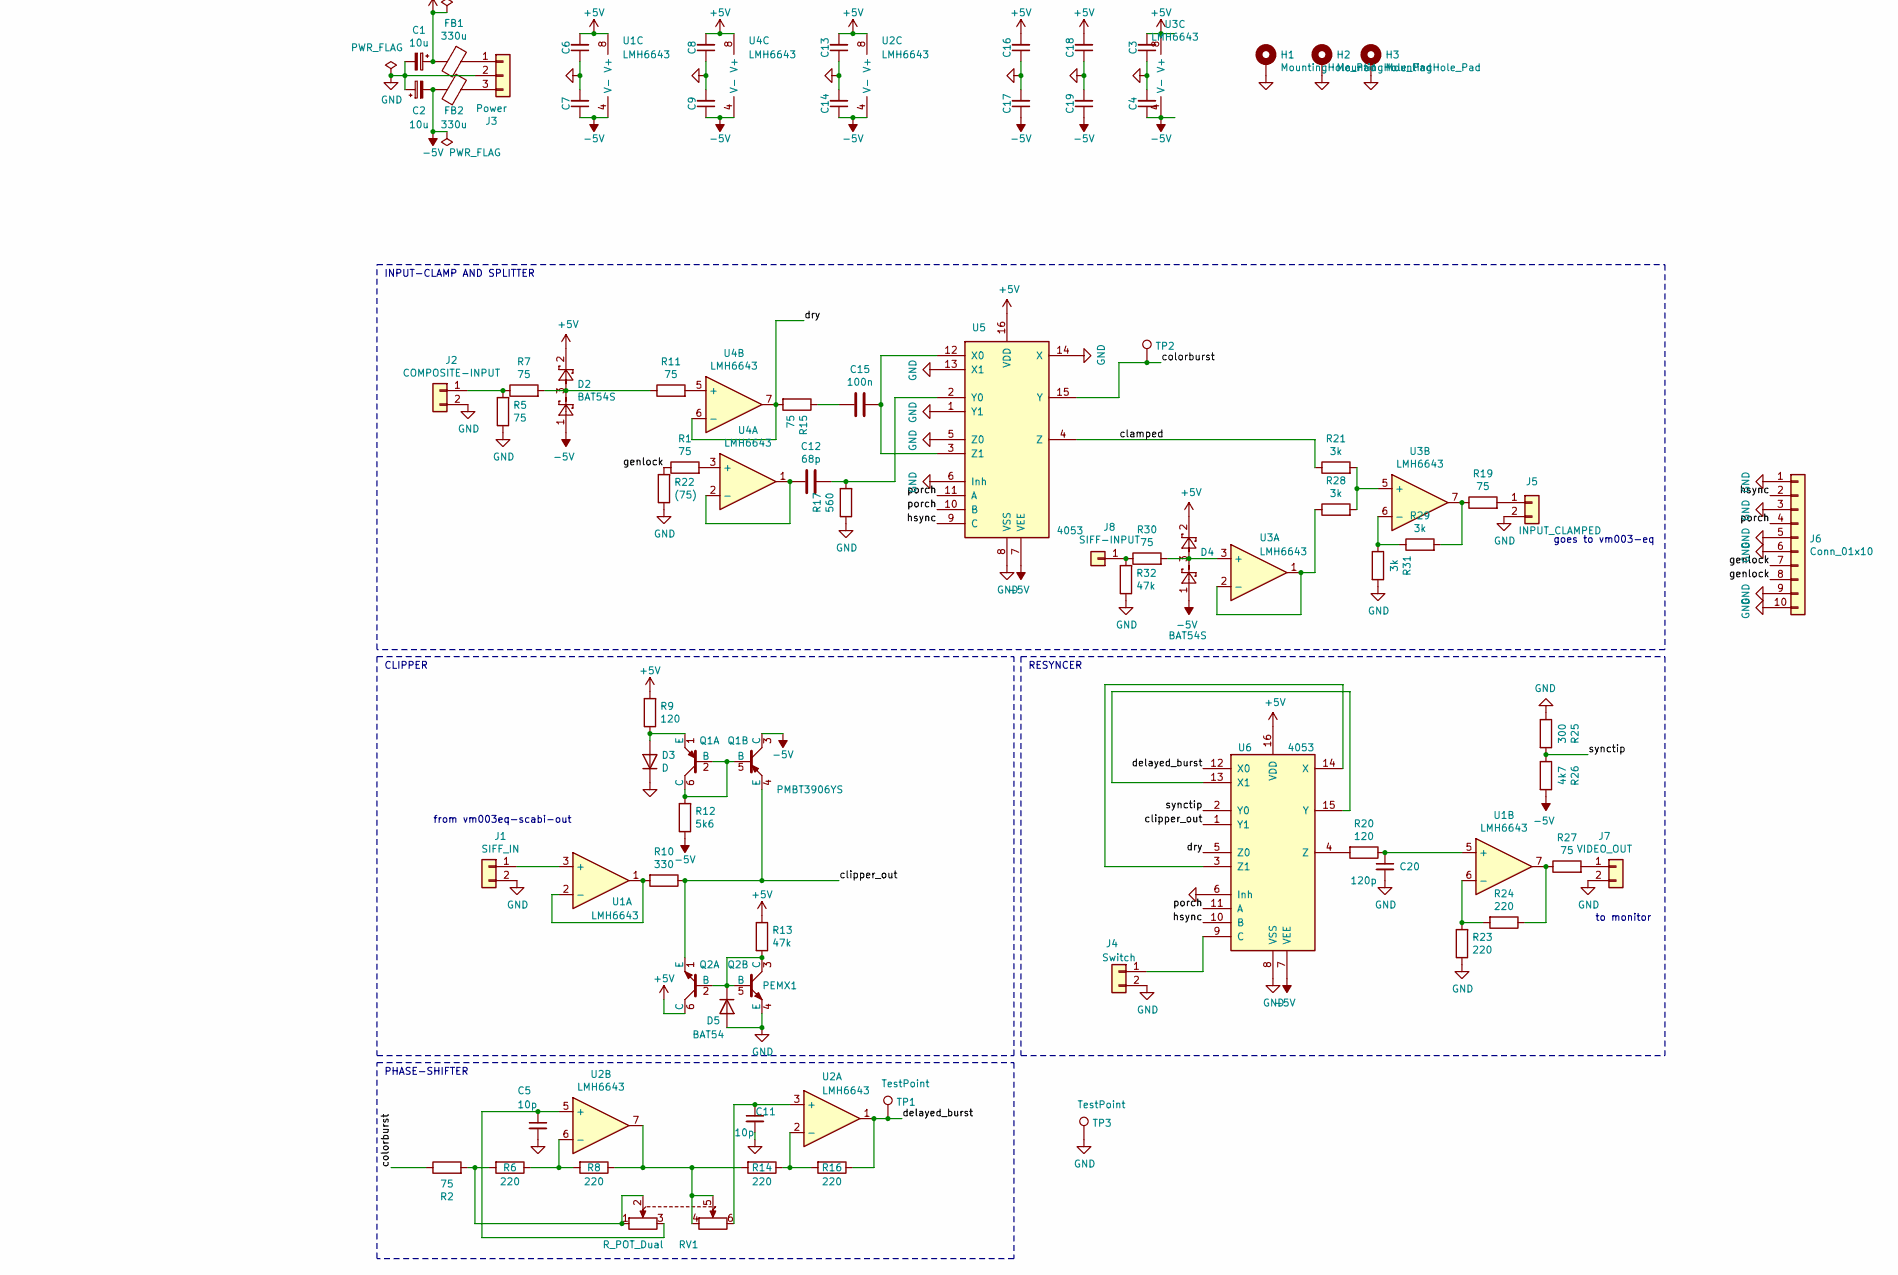
[picture p82: schematic vm001-input.sch, vm001-VMIX20 INPUT AND RESYNCER SECTION, part in row 2, column 2]

Parts:
C1, C2: 10u; CP_EIA-3528-21_Kemet-B_Pad1.50x2.35mm_HandSolder
C3, C4, C6, C7, C8, C9, C13, C14, C15, C16, C17, C18, C19: 100n; C_0603_1608Metric_Pad1.05x0.95mm_HandSolder
C5, C11: 10p; C_0805_2012Metric_Pad1.15x1.40mm_HandSolder
C12: 68p; C_1206_3216Metric_Pad1.42x1.75mm_HandSolder
C20: 120p; C_0603_1608Metric_Pad1.05x0.95mm_HandSolder
D2, D4: BAT54S; SOT-23
D3: D; D_MiniMELF
D5: BAT54; D_SOT-23_ANK
FB1, FB2: 330u; L_1206_3216Metric_Pad1.42x1.75mm_HandSolder
H1, H2, H3: MountingHole_Pad; MountingHole_2.7mm_M2.5_ISO7380_Pad
J1: SIFF_IN; Molex_KK-254_AE-6410-02A_1x02_P2.54mm_Vertical
J2: COMPOSITE-INPUT; Molex_KK-254_AE-6410-02A_1x02_P2.54mm_Vertical
J3: Power; Molex_KK-254_AE-6410-03A_1x03_P2.54mm_Vertical
J4: Switch; PinHeader_1x02_P2.54mm_Vertical
J5: INPUT_CLAMPED; Molex_KK-254_AE-6410-02A_1x02_P2.54mm_Vertical
J6: Conn_01x10; IDC-Header_2x05_P2.54mm_Vertical
J7: VIDEO_OUT; Molex_KK-254_AE-6410-02A_1x02_P2.54mm_Vertical
J8: SIFF-INPUT; Solderpad_1mm
Q1: PMBT3906YS; SOT-363_SC-70-6_Handsoldering
Q2: PEMX1; SOT-666
R1, R2, R5, R7, R11, R15, R19, R27, R30: 75; R_0805_2012Metric_Pad1.15x1.40mm_HandSolder
R6, R8, R14, R16, R23, R24: 220; R_0805_2012Metric_Pad1.15x1.40mm_HandSolder
R9, R20: 120; R_0805_2012Metric_Pad1.15x1.40mm_HandSolder
R10: 330; R_0805_2012Metric_Pad1.15x1.40mm_HandSolder
R12: 5k6; R_0805_2012Metric_Pad1.15x1.40mm_HandSolder
R13, R32: 47k; R_0805_2012Metric_Pad1.15x1.40mm_HandSolder
R17: 560; R_0805_2012Metric_Pad1.15x1.40mm_HandSolder
R21, R28, R29, R31: 3k; R_0805_2012Metric_Pad1.15x1.40mm_HandSolder
R22: (75); R_0805_2012Metric_Pad1.15x1.40mm_HandSolder
R25: 300; R_0805_2012Metric_Pad1.15x1.40mm_HandSolder
R26: 4k7; R_0805_2012Metric_Pad1.15x1.40mm_HandSolder
RV1: R_POT_Dual; RK12L123
TP1, TP2, TP3: TestPoint; Solderpad_1mm
U1, U2, U3, U4: LMH6643; SOIC-8_3.9x4.9mm_P1.27mm
U5, U6: 4053; SOIC-16_3.9x9.9mm_P1.27mm

Connections:
+5V: C1.1, C3.2, C6.2, C8.2, C13.2, C16.2, C18.2, D2.2, D4.2, FB1.2, Q2.6 (C), R9.2, R13.1, U1.8 (V+), U2.8 (V+), U3.8 (V+), U4.8 (V+), U5.16 (VDD), U6.16 (VDD)
-5V: C2.2, C4.1, C7.1, C9.1, C14.1, C17.1, C19.1, D2.1, D4.1, FB2.2, Q1.3 (C), R12.1, R26.2, U1.4 (V-), U2.4 (V-), U3.4 (V-), U4.4 (V-), U5.7 (VEE), U6.7 (VEE)
/clamped: R21.1, U5.4 (Z)
/clipper_out: Q1.4 (E), Q2.1 (E), R10.1, U6.1 (Y1)
/colorburst: R2.1, TP2.1, U5.15 (Y)
/delayed_burst: R16.1, TP1.1, U2.1, U6.12 (X0)
/dry: R15.2, U4.6 (-), U4.7, U6.5 (Z0)
/genlock: J6.7, J6.8, R1.1, R22.2
/hsync: J6.2, U5.9 (C), U6.10 (B)
/porch: J6.4, U5.10 (B), U5.11 (A), U6.11 (A)
/synctip: R25.2, R26.1, U6.2 (Y0)
GND: C1.2, C2.1, C3.1, C4.2, C5.2, C6.1, C7.2, C8.1, C9.2, C11.2, C13.1, C14.2, C16.1, C17.2, C18.1, C19.2, C20.2, D3.1 (K), D5.2 (A), H1.1, H2.1, H3.1, J1.2, J2.2, J3.2, J4.2, J5.2, J6.1, J6.3, J6.5, J6.6, J6.9, J6.10, J7.2, Q2.4 (E), R5.1, R17.1, R22.1, R23.1, R25.1, R31.2, R32.1, TP3.1, U5.1 (Y1), U5.5 (Z0), U5.6 (Inh), U5.8 (VSS), U5.13 (X1), U5.14 (X), U6.6 (Inh), U6.8 (VSS)
unnamed: C5.1, RV1.3, U2.5 (+)
unnamed: C11.1, RV1.6, U2.3 (+)
unnamed: C12.1, R17.2, U5.2 (Y0)
unnamed: C12.2, U4.1, U4.2 (-)
unnamed: C15.1, U5.3 (Z1), U5.12 (X0)
unnamed: C15.2, R15.1
unnamed: C20.1, R20.1, U1.5 (+)
unnamed: D2.3, R7.2, R11.1
unnamed: D3.2 (A), Q1.1 (E), R9.1
unnamed: D4.3, R30.2, U3.3 (+)
unnamed: D5.1 (K), Q2.2 (B), Q2.3 (C), Q2.5 (B), R13.2
unnamed: FB1.1, J3.1
unnamed: FB2.1, J3.3
unnamed: J1.1, U1.3 (+)
unnamed: J2.1, R5.2, R7.1
unnamed: J4.1, U6.9 (C)
unnamed: J5.1, R19.2
unnamed: J7.1, R27.2
unnamed: J8.1, R30.1, R32.2
unnamed: Q1.2 (B), Q1.5 (B), Q1.6 (C), R12.2
unnamed: R1.2, U4.3 (+)
unnamed: R2.2, R6.2, RV1.1, RV1.2
unnamed: R6.1, R8.2, U2.6 (-)
unnamed: R10.2, U1.1, U1.2 (-)
unnamed: R11.2, U4.5 (+)
unnamed: R14.1, R16.2, U2.2 (-)
unnamed: R8.1, R14.2, RV1.4, RV1.5, U2.7
unnamed: R19.1, R29.2, U3.7
unnamed: R20.2, U6.4 (Z)
unnamed: R21.2, R28.2, U3.5 (+)
unnamed: R23.2, R24.2, U1.6 (-)
unnamed: R24.1, R27.1, U1.7
unnamed: R28.1, U3.1, U3.2 (-)
unnamed: R29.1, R31.1, U3.6 (-)
unnamed: U6.13 (X1), U6.15 (Y)
unnamed: U6.3 (Z1), U6.14 (X)

Notes on the sheet:
PHASE-SHIFTER
CLIPPER
RESYNCER
INPUT-CLAMP AND SPLITTER
goes to vm003-eq
to monitor
from vm003eq-scabi-out

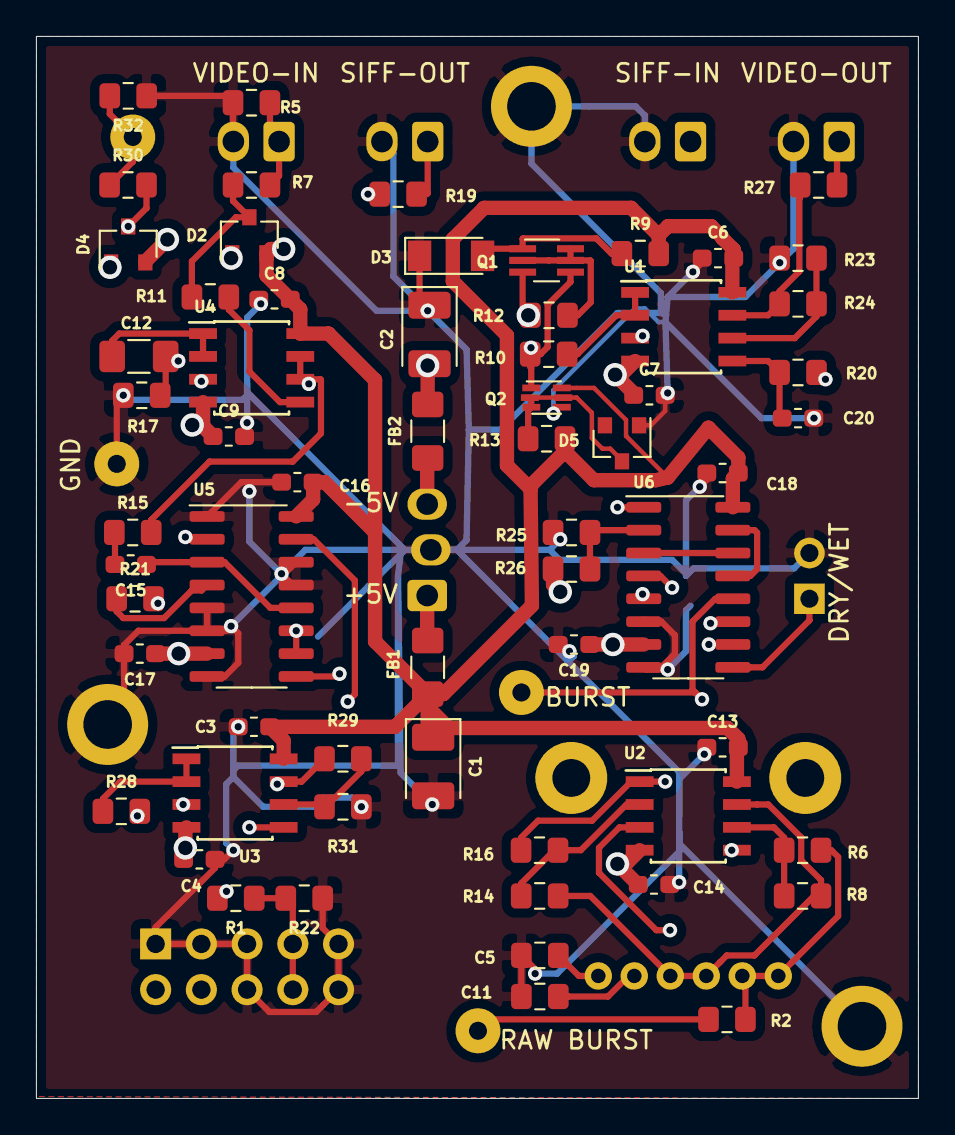
[picture p83: board vm001-input.kicad_pcb from above]

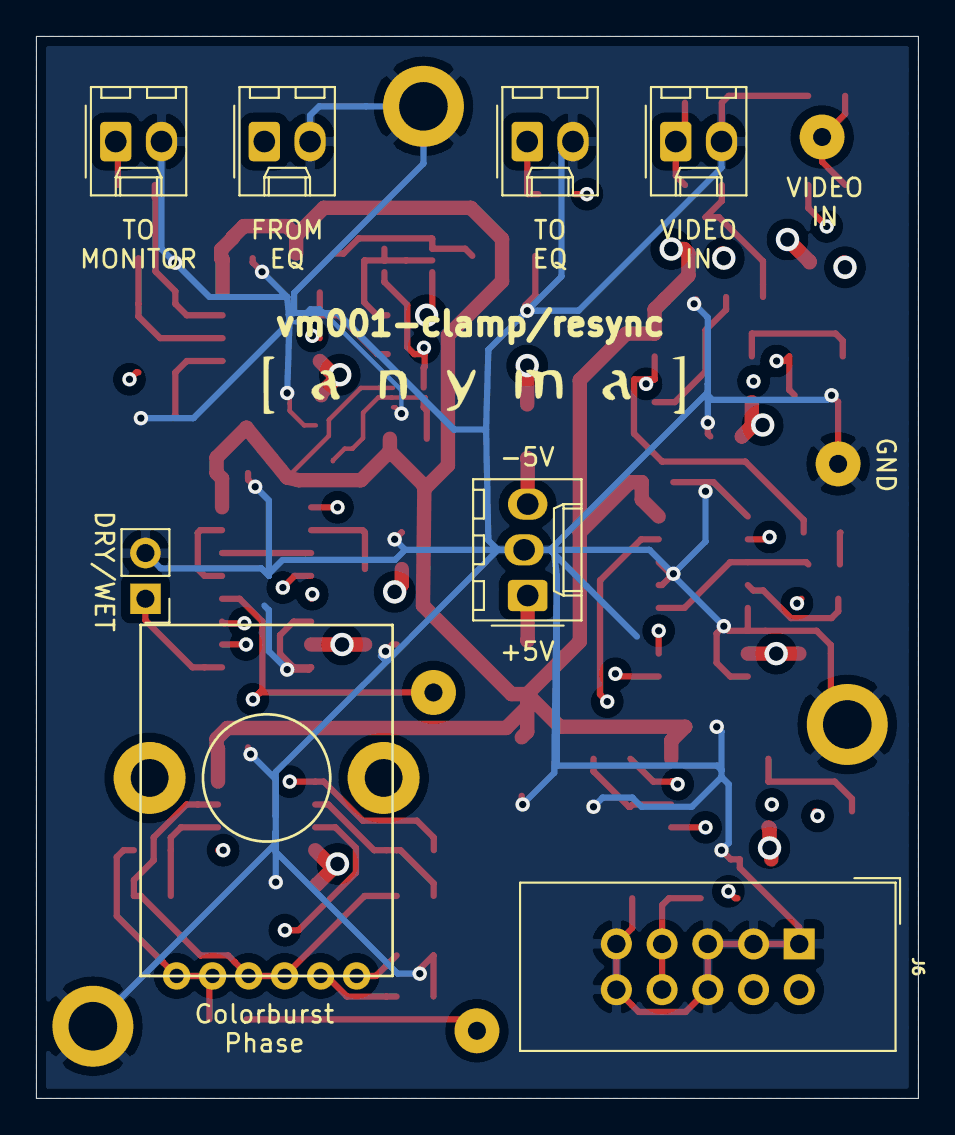
[picture p84: board vm001-input.kicad_pcb from below]

Board: 4 copper layers, 49.0 x 59.0 mm, 77 parts (8 on the bottom side), 48 nets.
