mirdej/vmix/vm006-mixbus/vm006-mixbus.kicad_pcb

## KiCad design vm006-mixbus/vm006-mixbus.kicad_pcb (2020-11-08)

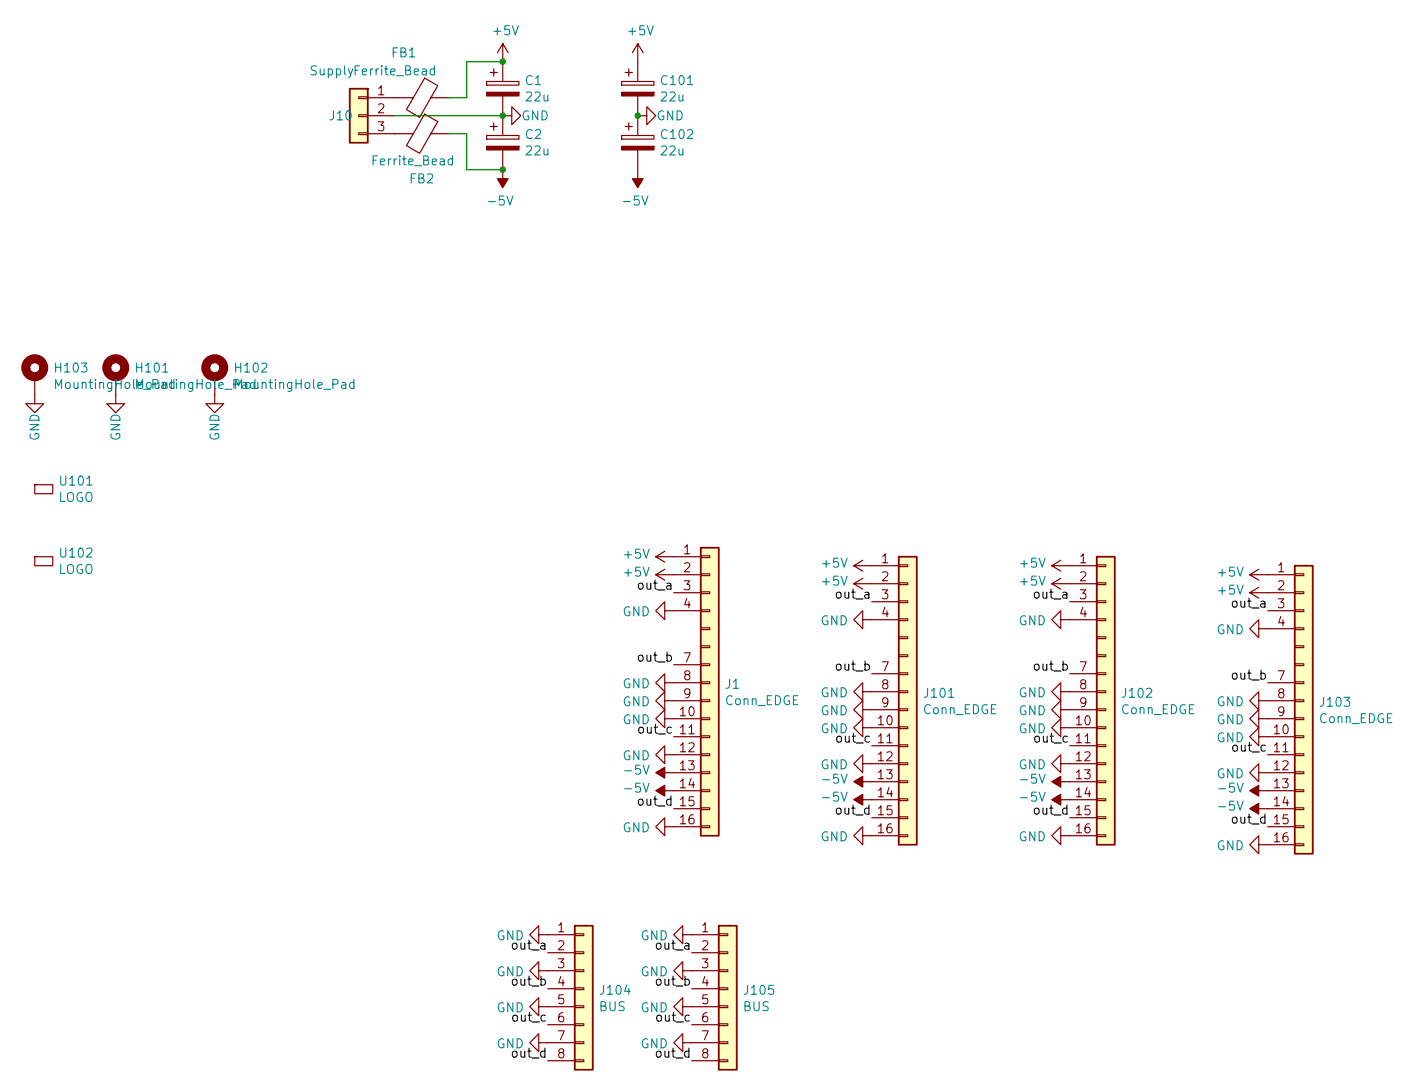
[picture p85: schematic vm006-mixbus.sch]

Parts:
C1, C2, C101, C102: 22u; CP_EIA-7360-38_Kemet-E_Pad2.25x4.25mm_HandSolder
FB1, FB2: Ferrite_Bead; L_1206_3216Metric_Pad1.42x1.75mm_HandSolder
H101, H102, H103: MountingHole_Pad; MountingHole_3.2mm_M3_Pad
J1, J101, J102, J103: Conn_EDGE; Samtec_MECF-08-01-L-DV-WT_2x08_P1.27mm_Polarized_Socket_Hor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
J10: Supply; Molex_KK-254_AE-6410-03A_1x03_P2.54mm_Vertical
J104, J105: BUS; PinHeader_1x08_P2.54mm_Vertical
U101: LOGO; logo_anyma
U102: LOGO; OSHW-Logo2_9.8x8mm_SilkScreen

Connections:
+5V: C1.1, C101.1, FB1.1, J1.1, J1.2, J101.1, J101.2, J102.1, J102.2, J103.1, J103.2
-5V: C2.2, C102.2, FB2.1, J1.13, J1.14, J101.13, J101.14, J102.13, J102.14, J103.13, J103.14
/out_a: J1.3, J101.3, J102.3, J103.3, J104.2, J105.2
/out_b: J1.7, J101.7, J102.7, J103.7, J104.4, J105.4
/out_c: J1.11, J101.11, J102.11, J103.11, J104.6, J105.6
/out_d: J1.15, J101.15, J102.15, J103.15, J104.8, J105.8
GND: C1.2, C2.1, C101.2, C102.1, H101.1, H102.1, H103.1, J1.4, J1.8, J1.9, J1.10, J1.12, J1.16, J10.2, J101.4, J101.8, J101.9, J101.10, J101.12, J101.16, J102.4, J102.8, J102.9, J102.10, J102.12, J102.16, J103.4, J103.8, J103.9, J103.10, J103.12, J103.16, J104.1, J104.3, J104.5, J104.7, J105.1, J105.3, J105.5, J105.7
unnamed: FB1.2, J10.1
unnamed: FB2.2, J10.3

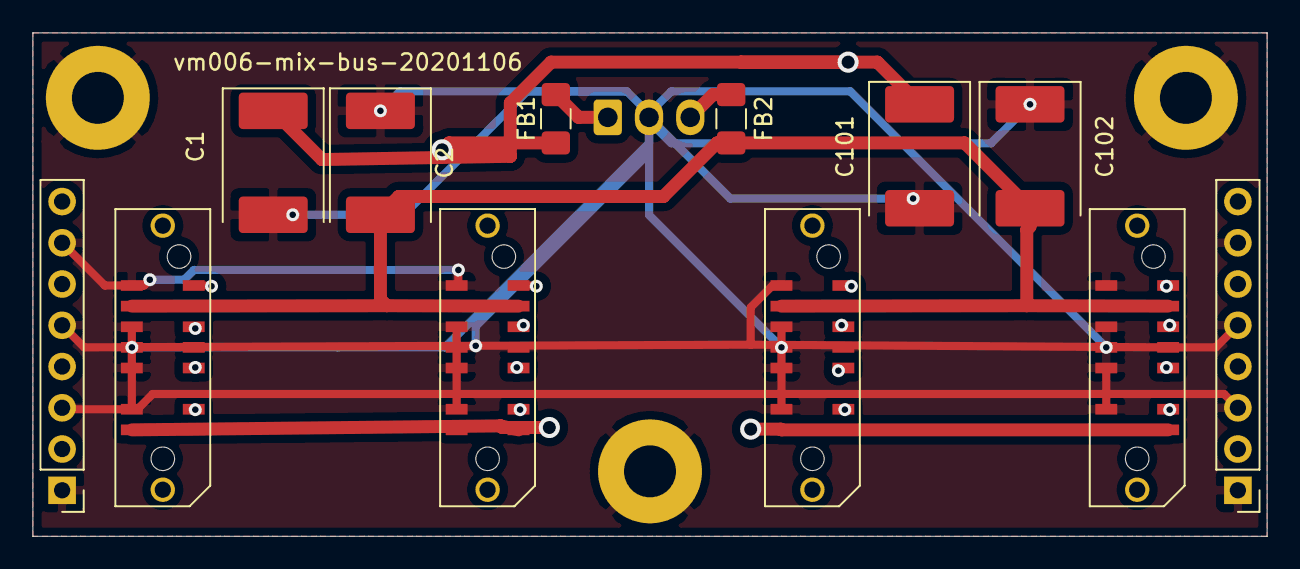
[picture p86: board vm006-mixbus.kicad_pcb from above]

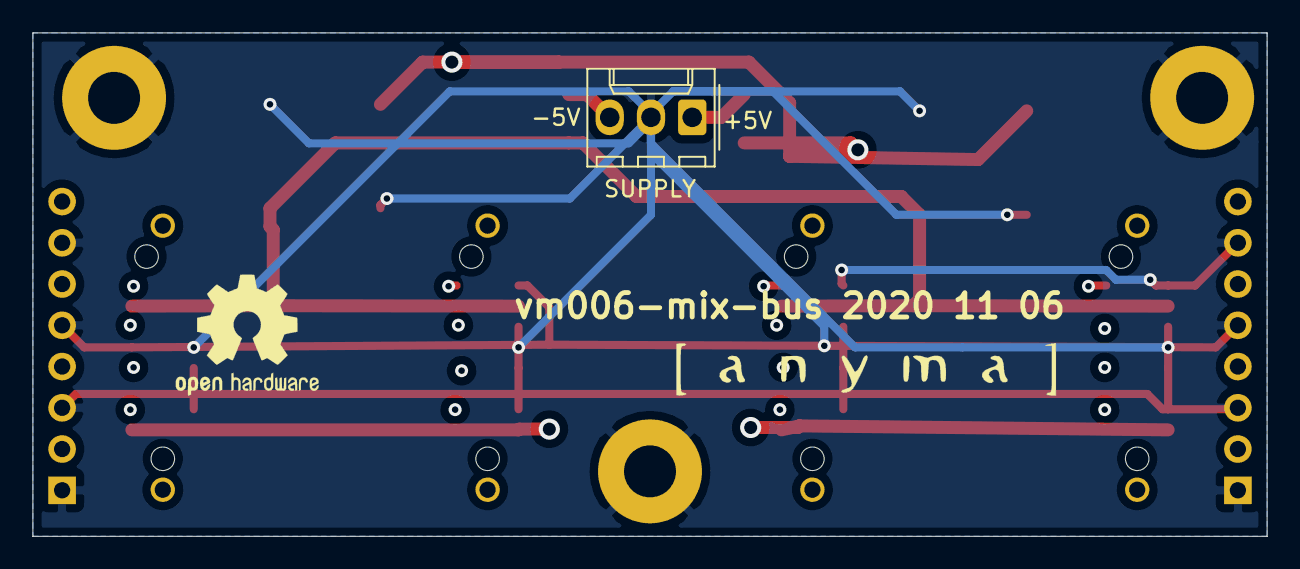
[picture p87: board vm006-mixbus.kicad_pcb from below]

Board: 4 copper layers, 76.0 x 31.0 mm, 18 parts (3 on the bottom side), 9 nets.
