mirdej/vmix/vm002-resync/vm002-resync.kicad_pcb

## KiCad design vm002-resync/vm002-resync.kicad_pcb (2020-08-20)

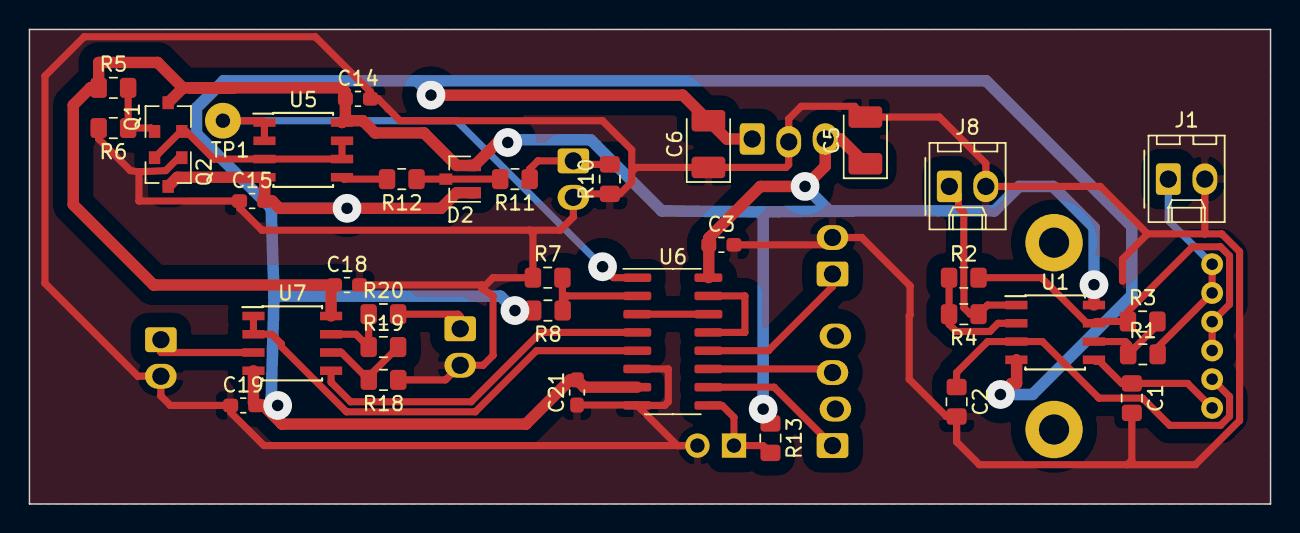
[picture p88: board vm002-resync.kicad_pcb from above]

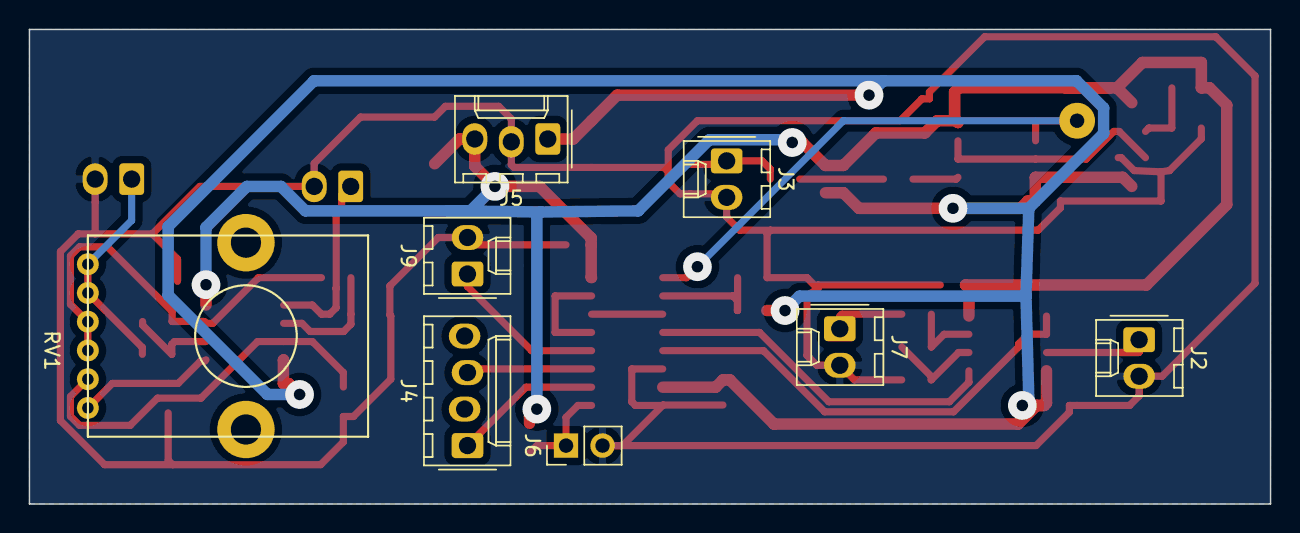
[picture p89: board vm002-resync.kicad_pcb from below]

Board: 2 copper layers, 86.4 x 33.0 mm, 43 parts (8 on the bottom side), 29 nets.

Parts:
C1, C2: 10p; C_0805_2012Metric_Pad1.15x1.40mm_HandSolder
C3, C14, C15, C18, C19, C21: 100n; C_0603_1608Metric_Pad1.05x0.95mm_HandSolder
C5, C6: 10u; CP_EIA-3528-21_Kemet-B_Pad1.50x2.35mm_HandSolder
D2: BAT54S; SOT-23
J1: BURST_IN; Molex_KK-254_AE-6410-02A_1x02_P2.54mm_Vertical
J2: GENLOCK; Molex_KK-254_AE-6410-02A_1x02_P2.54mm_Vertical
J3: SIFF_IN; Molex_KK-254_AE-6410-02A_1x02_P2.54mm_Vertical
J4: Conn_01x04; Molex_KK-254_AE-6410-04A_1x04_P2.54mm_Vertical
J5: Conn_01x03; Molex_KK-254_AE-6410-03A_1x03_P2.54mm_Vertical
J6: Switch; PinHeader_1x02_P2.54mm_Vertical
J7: VIDEO_OUT; Molex_KK-254_AE-6410-02A_1x02_P2.54mm_Vertical
J8: BURST_DELAYED; Molex_KK-254_AE-6410-02A_1x02_P2.54mm_Vertical
J9: Colorburst; Molex_KK-254_AE-6410-02A_1x02_P2.54mm_Vertical
Q1: Trans_NPN_Generic; SOT-23_BEC
Q2: Trans_PNP_Generic; SOT-23_BEC
R1, R2, R3, R4, R18, R19: 220; R_0805_2012Metric_Pad1.15x1.40mm_HandSolder
R5: 1k; R_0805_2012Metric_Pad1.15x1.40mm_HandSolder
R6: 150; R_0805_2012Metric_Pad1.15x1.40mm_HandSolder
R7: 300; R_0805_2012Metric_Pad1.15x1.40mm_HandSolder
R8, R13: 4k7; R_0805_2012Metric_Pad1.15x1.40mm_HandSolder
R10: 47k; R_0805_2012Metric_Pad1.15x1.40mm_HandSolder
R11, R12, R20: 75; R_0805_2012Metric_Pad1.15x1.40mm_HandSolder
RV1: R_POT_Dual; RK12L123
TP1: TestPoint; Solderpad_1mm
U1, U5, U7: LMH6643; SOIC-8_3.9x4.9mm_P1.27mm
U6: 4053; SOIC-16_3.9x9.9mm_P1.27mm

Connections:
+5V: C3.1, C5.1, C14.1, C18.1, D2.2, J5.3, Q1.C, R5.1, R13.1, U1.8, U5.8, U6.16, U7.8
-5V: C6.2, C15.2, C19.2, C21.2, D2.1, J5.1, Q2.C, R8.2, U1.4, U5.4, U6.7, U7.4
/clipper_out: TP1.1, U5.1, U5.2, U6.1
/colorburst: J9.1, U6.12
/hsync: J4.1, U6.10
/porch: J4.3, U6.11
/synctip: R7.2, R8.1, U6.2
GND: C1.2, C2.2, C3.2, C5.2, C6.1, C14.2, C15.1, C18.2, C19.1, C21.1, J1.2, J2.2, J3.2, J5.2, J6.2, J7.2, J8.2, J9.2, Q2.B, R6.2, R7.1, R10.1, R18.1, U6.6, U6.8
unnamed: C1.1, RV1.3, U1.5
unnamed: C2.1, RV1.6, U1.3
unnamed: D2.3, R11.2, R12.1
unnamed: J1.1, R1.2, RV1.1, RV1.2
unnamed: J2.1, U7.3
unnamed: J3.1, R10.2, R11.1
unnamed: J6.1, R13.2, U6.9
unnamed: J7.1, R20.2
unnamed: J8.1, R4.1, U1.1
unnamed: Q1.B, R5.2, R6.1
unnamed: Q1.E, Q2.E, U5.3, U5.6, U5.7
unnamed: R1.1, R3.2, U1.6
unnamed: R2.1, R4.2, U1.2
unnamed: R2.2, R3.1, RV1.4, RV1.5, U1.7
unnamed: R12.2, U5.5
unnamed: R18.2, R19.2, U7.6
unnamed: R19.1, R20.1, U7.7
unnamed: U6.4, U7.5
unnamed: U6.5, U7.1, U7.2
unnamed: U6.13, U6.15
unnamed: U6.3, U6.14
