mirdej/vmix/vm003-eq/stade1.kicad_pcb

## KiCad design vm003-eq/stade1.kicad_pcb (2020-08-20)

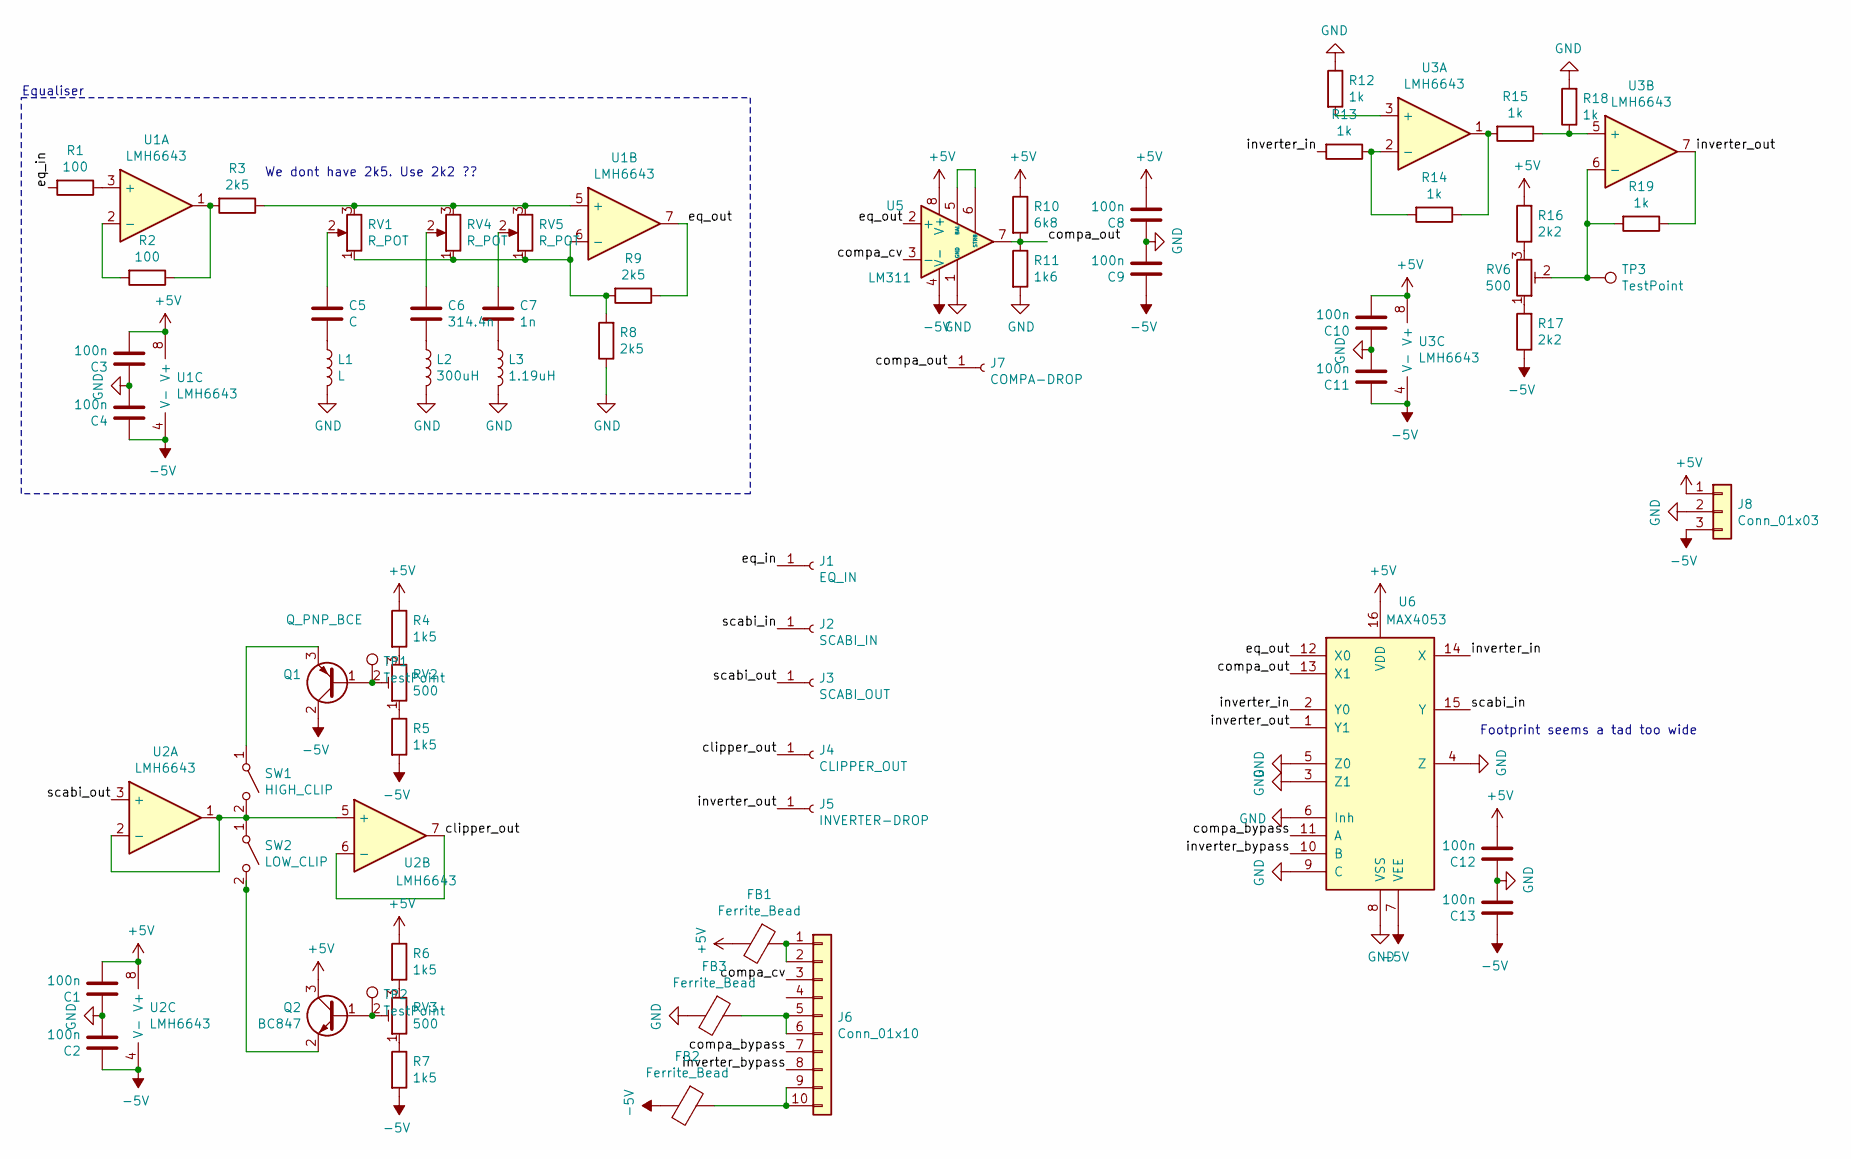
[picture p90: schematic vm003-eq.sch]

Parts:
C1, C2, C3, C4, C8, C9, C10, C11, C12, C13: 100n; C_0603_1608Metric_Pad1.05x0.95mm_HandSolder
C5: C; C_1206_3216Metric_Pad1.42x1.75mm_HandSolder
C6: 314.4n; C_1206_3216Metric_Pad1.42x1.75mm_HandSolder
C7: 1n; C_1206_3216Metric_Pad1.42x1.75mm_HandSolder
FB1, FB2, FB3: Ferrite_Bead; L_0805_2012Metric_Pad1.15x1.40mm_HandSolder
J1: EQ_IN; Solderpad_1mm
J2: SCABI_IN; Solderpad_1mm
J3: SCABI_OUT; Solderpad_1mm
J4: CLIPPER_OUT; Solderpad_1mm
J5: INVERTER-DROP; Solderpad_1mm
J6: Conn_01x10; IDC-Header_2x05_P2.54mm_Vertical
J7: COMPA-DROP; Solderpad_1mm
J8: Conn_01x03; Molex_KK-254_AE-6410-03A_1x03_P2.54mm_Vertical
L1: L; L_1206_3216Metric_Pad1.42x1.75mm_HandSolder
L2: 300uH; L_1206_3216Metric_Pad1.42x1.75mm_HandSolder
L3: 1.19uH; L_1206_3216Metric_Pad1.42x1.75mm_HandSolder
Q1: Q_PNP_BCE; SOT-23
Q2: BC847; SOT-23
R1, R2: 100; R_0805_2012Metric_Pad1.15x1.40mm_HandSolder
R3, R8, R9: 2k5; R_0805_2012Metric_Pad1.15x1.40mm_HandSolder
R4, R5, R6, R7: 1k5; R_0805_2012Metric_Pad1.15x1.40mm_HandSolder
R10: 6k8; R_0805_2012Metric_Pad1.15x1.40mm_HandSolder
R11: 1k6; R_0805_2012Metric_Pad1.15x1.40mm_HandSolder
R12, R13, R14, R15, R18, R19: 1k; R_0805_2012Metric_Pad1.15x1.40mm_HandSolder
R16, R17: 2k2; R_0805_2012Metric_Pad1.15x1.40mm_HandSolder
RV1, RV4, RV5: R_POT; Potentiometer_Alps_RK09K_Single_Horizontal
RV2, RV3, RV6: 500; Potentiometer_Bourns_3296Y_Vertical
SW1: HIGH_CLIP; PinHeader_1x02_P2.54mm_Vertical
SW2: LOW_CLIP; PinHeader_1x02_P2.54mm_Vertical
TP1, TP2, TP3: TestPoint; TestPoint_Pad_D2.0mm
U1, U2, U3: LMH6643; SOIC-8_3.9x4.9mm_P1.27mm
U5: LM311; SOIC-8_3.9x4.9mm_P1.27mm
U6: MAX4053; SOP-16_4.55x10.3mm_P1.27mm

Connections:
+5V: C1.2, C3.2, C8.2, C10.2, C12.2, FB1.2, J8.1, Q2.3 (C), R4.1, R6.1, R10.1, R16.2, U1.8 (V+), U2.8 (V+), U3.8 (V+), U5.8 (V+), U6.16 (VDD)
-5V: C2.1, C4.1, C9.1, C11.1, C13.1, FB2.2, J8.3, Q1.2 (C), R5.2, R7.2, R17.1, U1.4 (V-), U2.4 (V-), U3.4 (V-), U5.4 (V-), U6.7 (VEE)
/clipper_out: J4.1, U2.6 (-), U2.7
/compa_bypass: J6.7, U6.11 (A)
/compa_cv: J6.3, U5.3 (-)
/compa_out: J7.1, R10.2, R11.1, U5.7, U6.13 (X1)
/eq_in: J1.1, R1.2
/eq_out: R9.1, U1.7, U5.2 (+), U6.12 (X0)
/inverter_bypass: J6.8, U6.10 (B)
/inverter_in: R13.2, U6.2 (Y0), U6.14 (X)
/inverter_out: J5.1, R19.1, U3.7, U6.1 (Y1)
/scabi_in: J2.1, U6.15 (Y)
/scabi_out: J3.1, U2.3 (+)
GND: C1.1, C2.2, C3.1, C4.2, C8.1, C9.2, C10.1, C11.2, C12.1, C13.2, FB3.2, J8.2, L1.2, L2.2, L3.2, R8.1, R11.2, R12.1, R18.2, U5.1 (GND), U6.3 (Z1), U6.4 (Z), U6.5 (Z0), U6.6 (Inh), U6.8 (VSS), U6.9 (C)
unnamed: C5.1, RV1.2
unnamed: C5.2, L1.1
unnamed: C6.1, RV4.2
unnamed: C6.2, L2.1
unnamed: C7.1, RV5.2
unnamed: C7.2, L3.1
unnamed: FB1.1, J6.1, J6.2
unnamed: FB2.1, J6.9, J6.10
unnamed: FB3.1, J6.5, J6.6
unnamed: Q1.1 (B), RV2.2, TP1.1
unnamed: Q1.3 (E), SW1.1 (A)
unnamed: Q2.1 (B), RV3.2, TP2.1
unnamed: Q2.2 (E), SW2.2 (B)
unnamed: R1.1, U1.3 (+)
unnamed: R2.1, R3.2, U1.1
unnamed: R2.2, U1.2 (-)
unnamed: R3.1, RV1.3, RV4.3, RV5.3, U1.5 (+)
unnamed: R4.2, RV2.3
unnamed: R5.1, RV2.1
unnamed: R6.2, RV3.3
unnamed: R7.1, RV3.1
unnamed: R8.2, R9.2, RV1.1, RV4.1, RV5.1, U1.6 (-)
unnamed: R12.2, U3.3 (+)
unnamed: R13.1, R14.2, U3.2 (-)
unnamed: R14.1, R15.2, U3.1
unnamed: R15.1, R18.1, U3.5 (+)
unnamed: R16.1, RV6.3
unnamed: R17.2, RV6.1
unnamed: R19.2, RV6.2, TP3.1, U3.6 (-)
unnamed: SW1.2 (B), SW2.1 (A), U2.1, U2.2 (-), U2.5 (+)
unnamed: U5.5 (BAL), U5.6 (STRB)

Notes on the sheet:
Equaliser
We dont have 2k5. Use 2k2 ??
Footprint seems a tad too wide

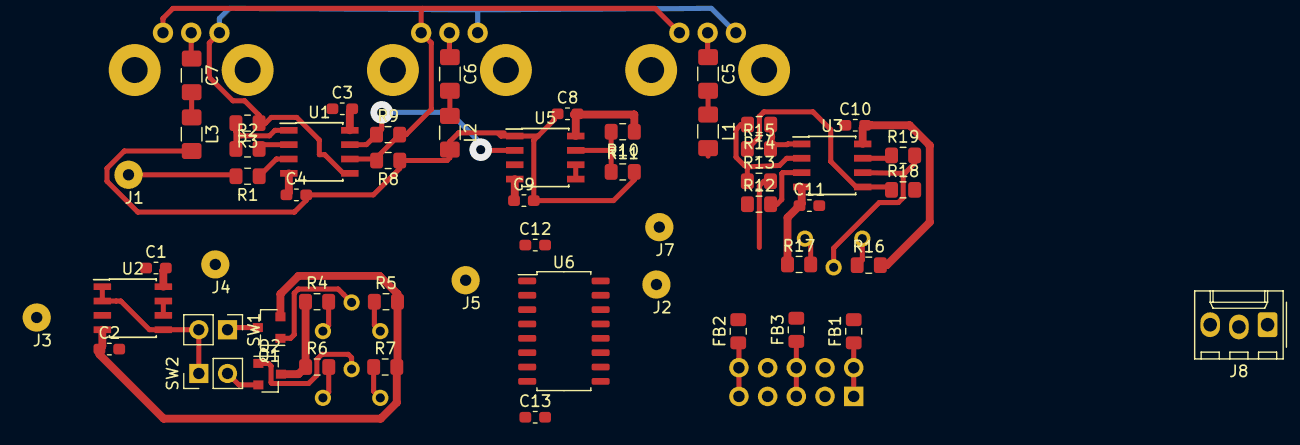
[picture p91: board stade1.kicad_pcb from above]

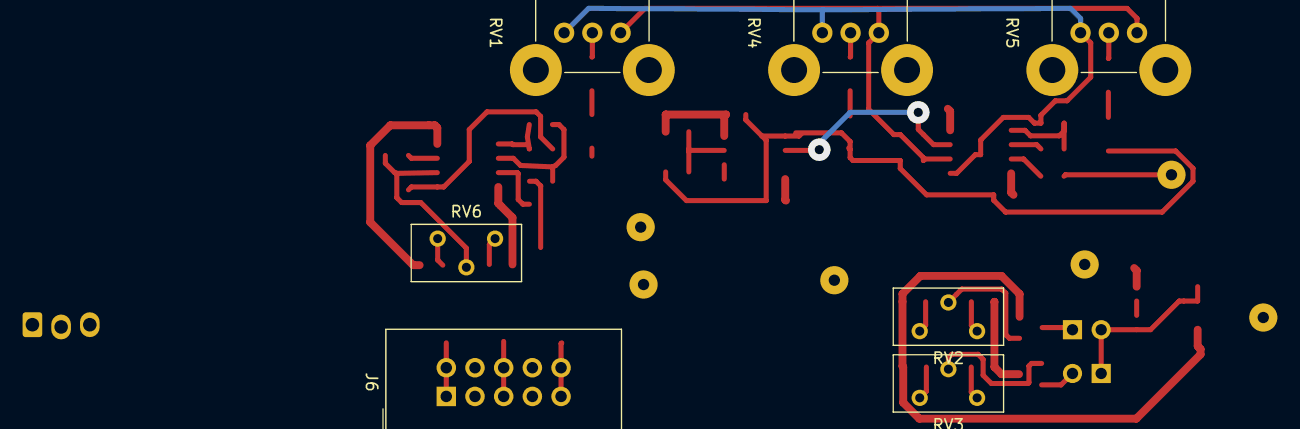
[picture p92: board stade1.kicad_pcb from below]

Board: 2 copper layers, 61 parts (7 on the bottom side), 45 nets.
